fablabbcn/smartcitizen-enclosures/docs/Power Options/Power hub/README.md

# SmartCitizen Power Hub

A simple board to distribute 5V and (maybe in the future) control power outputs in Smart Citizen hardware setups.
