fablabbcn/smartcitizen-enclosures/docs/Power Options/Reset button/README.md

# SmartCitizen Reset

A tiny little board to mount a SWD connector that can be connected to the one in the data board and reset the kit. Serves the same function as the onboard reset button but with easier access.

This board normally can be done in a Fablab very easily.
