fablabbcn/smartcitizen-enclosures/SmartCitizen Water Enclosures/SmartCitizen Water Station/Tentacle Water Station/README.md

# Water Station

Water Station - Patí Científic

## Features

- Up to 6 Water metrics with BNC Connector compatibility
- GPS Location and outdoor antenna
- USB powered

## Enclosure

We used this enclosure with a translucid smoked cover from FIBOX:
https://www.fibox.com/catalog/62/product/176/6016915_ENG3.html

### Supports

All files for laser cutting and 3D printing can be found in [this folder](https://github.com/fablabbcn/smartcitizen-enclosures/tree/master/Smart%20Citizen%20Water%20Station/components).

### Cable glands

We used Icotek QVT16 and QVT20 with different cable grommets (no hole, 1 hole, 4 holes) for passing cables.

### BOM

Find all the components in the [BOM](BOM.csv)

### Docs 

More documentation can be found in [the docs](http://docs.smartcitizen.me/Components/Soil%20and%20water/)

## Contributors

Developed in collaboration with [ICM-CSIC](https://www.icm.csic.es/en) and the [Club Pati Vela de Barcelona](https://pativelabarcelona.com/). Thanks!
