fablabbcn/smartcitizen-enclosures/docs/Water/Electronics/SmartCitizen Water Station/README.md

# Smart Citizen Water Station

This folder contains two iterations of the Smart Citizen Water Station. Currently, we only use the [Isolated Carrier Design](Isolated Carriers Station/) because it's a much more easier to use, assemble, and fix design, with a much lower power consumption. The [Tentacle T3 Design](deprecated/Tentacle%20Water%20Station/) is left for reference.
