fablabbcn/smartcitizen-enclosures/docs/Air/misc/SCK2.1_BIKE_SADDLEBAG/README.md

# Bike enclosure

This folder contains the parts needed to mount the SCK 2.1 with a PMS5003 and a GPS inside a saddle bag.

## Components

1. [Laser Cut PPE Folding](components/ppe-folding.dxf)
2. [3D printed clip](components/clip.stl) and [frame](components/frame.stl)
3. 3D printed intakes: [Left clip](components/inlet-l-clip.stl) and [left shell](components/inlet-l-shell.stl). Same for the [right clip](components/inlet-r-clip.stl) and [shell](components/inlet-r-shell.stl)
4. [3D printed exhaust grid](components/exhaust-grid.stl) and [rim](components/exhaust-rim.stl)
5. [3D printed sensor support](components/support.stl)
6. [3D printed GPS bridge](components/gps-bridge.stl)
6. 2x M3x15mm screw and nut
7. Vaude Race Light L (or similar)

The sensors are placed inside a commercial saddle bag, held with a ppe folding:

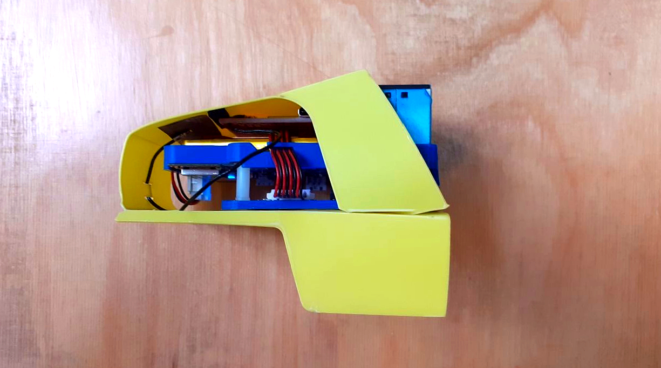
[picture p2: docs/assets/images/bike-saddle/ppe.jpg]


Below more information about how to assemble:

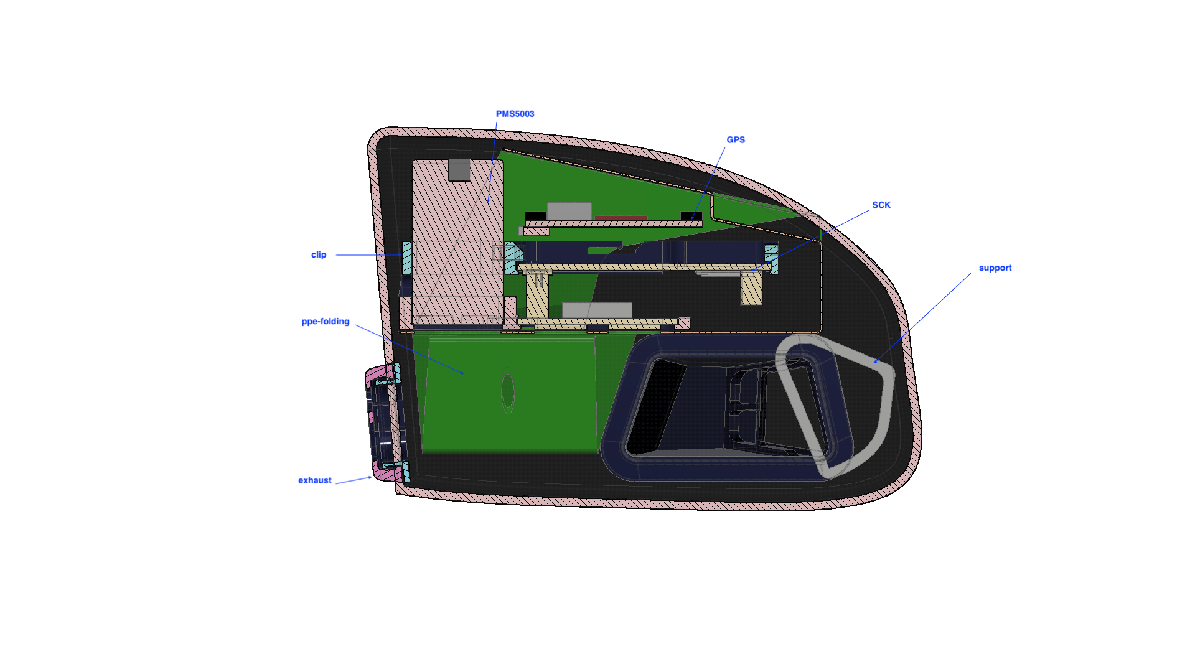
[picture p3: docs/assets/images/bike-saddle/cut-view.png]


## More information

Please, visit the [user manual](https://docs.smartcitizen.me/Use%20cases/Almabike/User%20Manual/) and the [test results](https://docs.smartcitizen.me/Use%20cases/Almabike/Test%20Results/) for more information.
