fablabbcn/smartcitizen-enclosures/docs/Air/SCK2.1/SCK2.1_PMS5003/README.md

Note:

The SCK and the PMS5003 are held together by a 3D printed clip. This can be found in the common components of the HDPE enclosure [here](/Air/SCK2.1/SCK2.1_PMS5003/CNC HDPE circle/components/CLIP_NO_ORING.stl)
