fablabbcn/smartcitizen-enclosures/docs/Air/SCK2.1/SCK2.1_PMS5003_2EC_CO2/README.md

These enclosures are used for the SCK2.1 + PMS5003 with 2xA-series alphasense sensors with one 2-way AFE and a Sensision SCD30 CO2 Sensor.
