fablabbcn/smartcitizen-enclosures/docs/Air/SCK2.1/SCK2.1_PMS5003_CO2/README.md

These enclosures are used for the SCK2.1 + PMS5003 with a Sensision SCD30 CO2 Sensor.
