fablabbcn/smartcitizen-enclosures/docs/Air/misc/CONNECTIVITY_UNIT/README.md

Smart Citizen Connectivity Unit
========================



Check the BOM to see the components needed.

## Enclousure 

An [ABS IP65 Wall Box](https://uk.rs-online.com/web/p/wall-boxes/7696125/?sra=pstk) is used for these unit. For mounting the components  you will need to drill the metal base of the IP65 Wall Box. Use the [*.dxf*](/SmartCitizen Connectivity Unit/base-template.dxf) file as a template using a 5mm drill and a 6mm drill. 


To hold the router, use two 3D printed tubes that you can found [here](/SmartCitizen Connectivity Unit/tube.stl).

 



They are also needed 2 holes on the top side of the box for the router antennas, using a 6.5mm drill, and 1 hole in the bottom part for the AC wire, using a 20mm drill.
