fablabbcn/smartcitizen-enclosures/docs/Air/SCK2.1/SCK2.1_2PMS5003_6EC/6-electrochemical-spec-2pm/README.md

# Station Rev 3.0 6-EC-2PM

This are the hardware design files for a Station Rev3.0 with 6 electrochemical sensors (SPEC) and 2PMS5003.

Components are in the [components](components) folder:

- [3DPRINTING](compontents/3DPRINTING) for parts to be 3D printed to hold components in
- [LASERCUT](compontents/LASERCUT) laser cut acrylic components
