fablabbcn/smartcitizen-enclosures/docs/Air/SCK2.1/SCK2.1_2PMS5003_4EC/4-electrochemical-alphasense-2pm/README.md

# Station Rev 3.0 4-EC-2PM

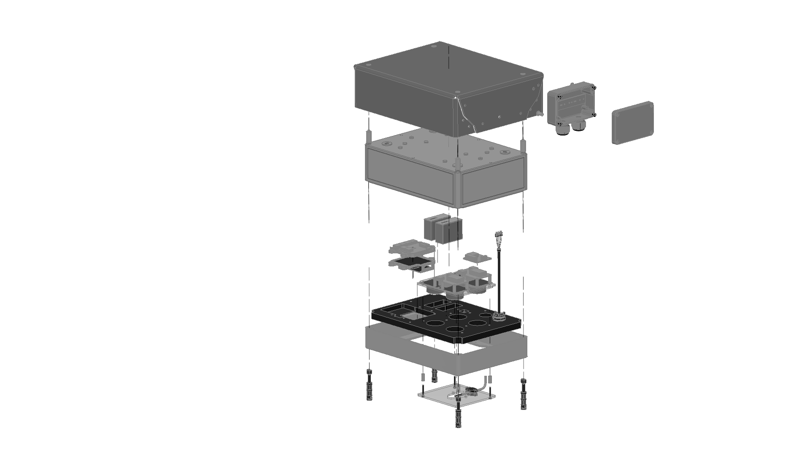
[picture p14: docs/Air/SCK2.1/SCK2.1_2PMS5003_4EC/4-electrochemical-alphasense-2pm/smartcitizen-station-passive-4-sensors.png]


This are the hardware design files for a Station Rev3.0 with 4 electrochemical sensors and 2PMS5003.

Components are in the [components](components) folder:

- [3DPRINTING](compontents/3DPRINTING) for parts to be 3D printed to hold components in
- [AUXLIARIES](compontents/AUXLIARIES) for elements such as the reset button
- [LASERCUT](compontents/LASERCUT) laser cut acrylic components
