fablabbcn/smartcitizen-enclosures/docs/Air/SCK2.1/SCK2.1_PMS5003/UMBRELLA/README.md

# Umbrella Cover

These are small and medium sized covers for the sensors. Made out of Dibond, with an stainless steel plate and some spacers.

Extras:

- M3 /M4 rivet nuts for hanging the enclosure using the spacers
- M4 rivet nuts for hanging the power supply on one side
