fablabbcn/smartcitizen-enclosures/docs/Air/SCK2.1/SCK2.1_2PMS5003_3EC/SmartCitizen Station V2.0/SmartCitizen Station V2.0 - 2.jpg

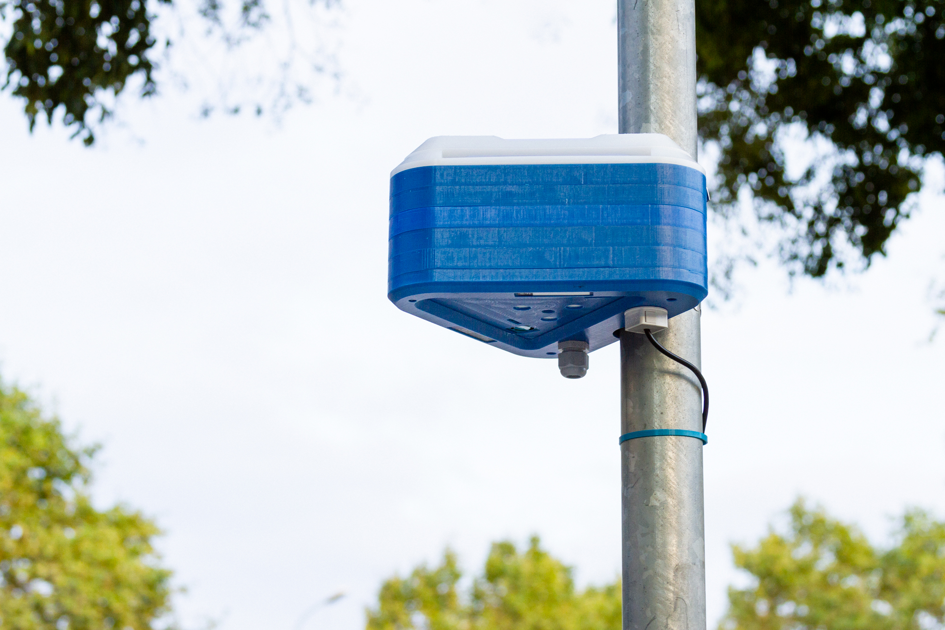
docs/Air/SCK2.1/SCK2.1_2PMS5003_3EC/SmartCitizen Station V2.0/SmartCitizen Station V2.0 - 2.jpg
