fablabbcn/smartcitizen-enclosures/docs/Air/SCK2.1/SCK2.1_PMS5003/CNC HDPE circle/final_render.png

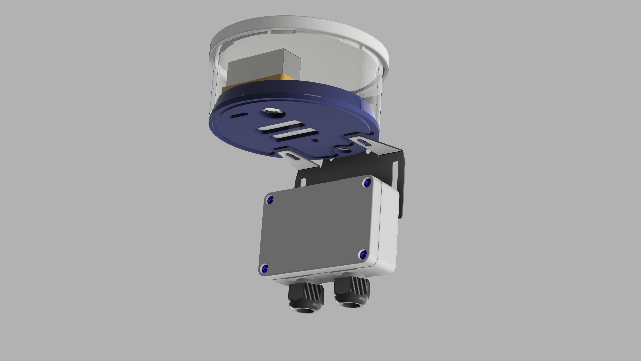
docs/Air/SCK2.1/SCK2.1_PMS5003/CNC HDPE circle/final_render.png
