fablabbcn/smartcitizen-enclosures/docs/assets/images/2.1/SCKit_21.png

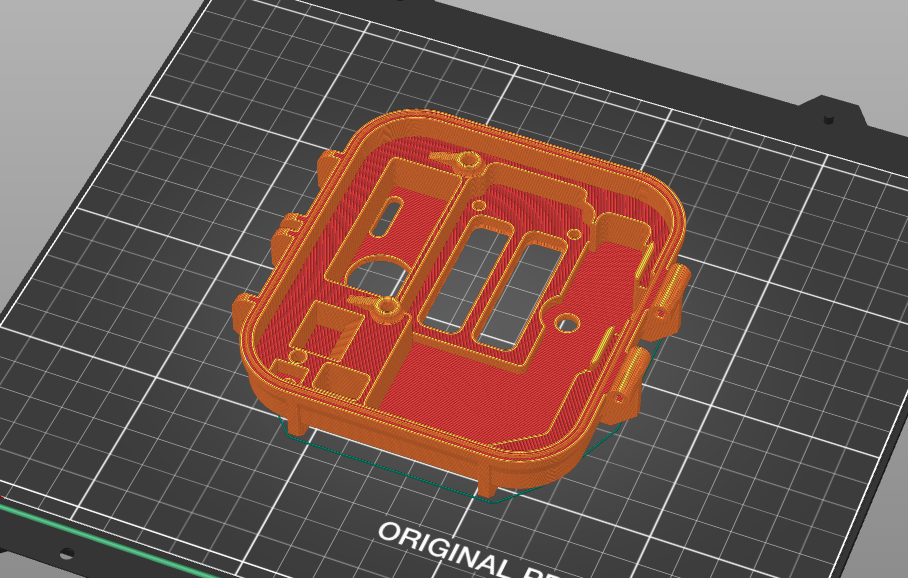
docs/assets/images/2.1/SCKit_21.png
