fablabbcn/smartcitizen-enclosures/docs/assets/images/2.2/PID_TIG_HCHO.jpg

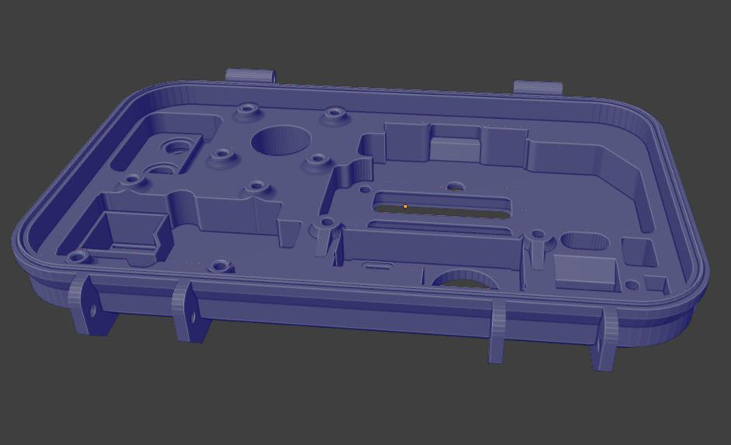
docs/assets/images/2.2/PID_TIG_HCHO.jpg
