fablabbcn/smartcitizen-enclosures/docs/assets/images/2.2/SCKit_22.png

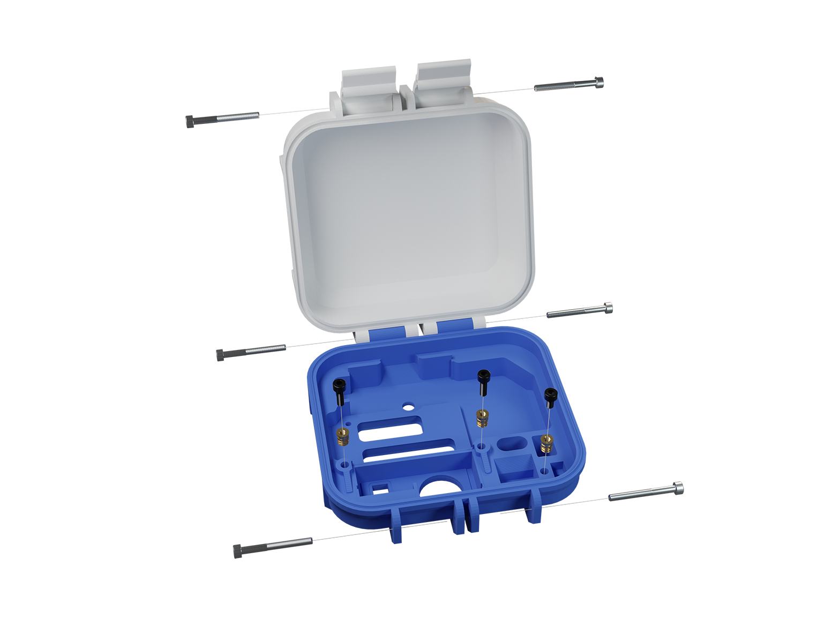
docs/assets/images/2.2/SCKit_22.png
