fablabbcn/smartcitizen-enclosures/docs/assets/images/2.2/SCKit_22_2EC.png

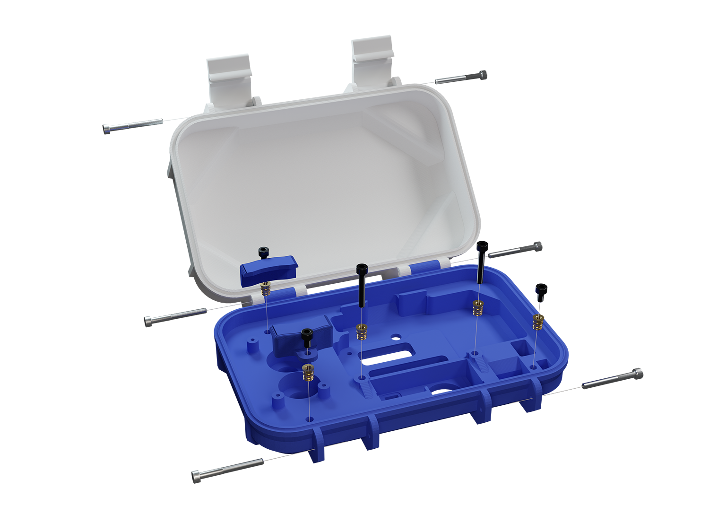
docs/assets/images/2.2/SCKit_22_2EC.png
