fablabbcn/smartcitizen-enclosures/docs/assets/images/2.2/SCKit_22_CO2+2EC.png

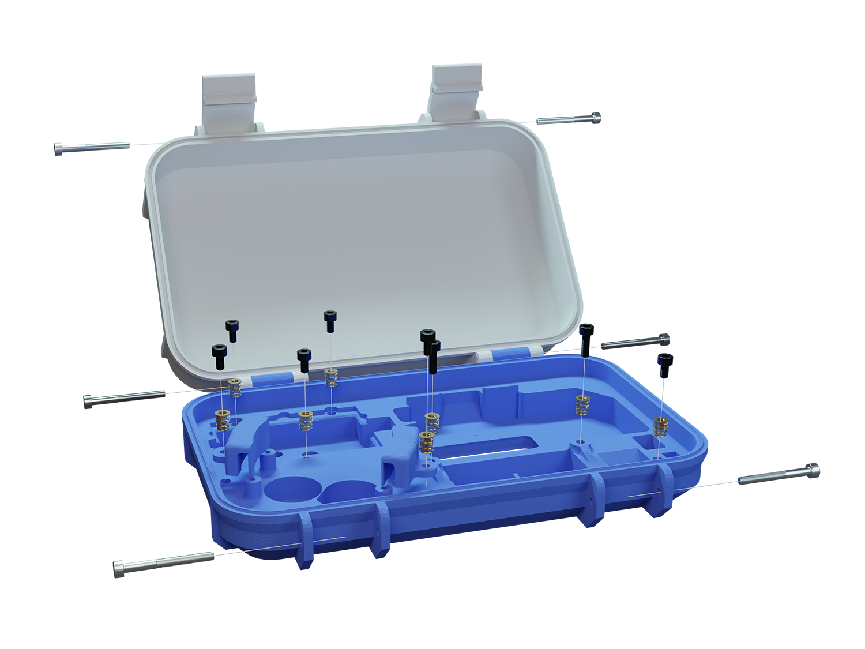
docs/assets/images/2.2/SCKit_22_CO2+2EC.png
