fablabbcn/smartcitizen-enclosures/docs/assets/images/2.2/SCKit_22_CO2+HCHO.png

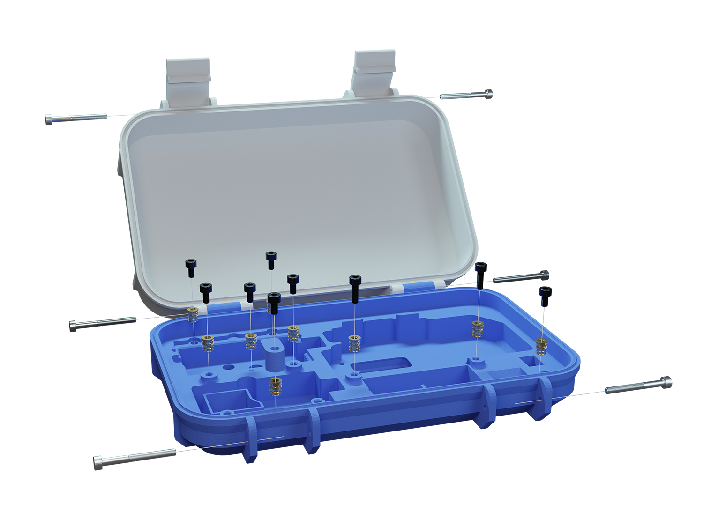
docs/assets/images/2.2/SCKit_22_CO2+HCHO.png
