fablabbcn/smartcitizen-enclosures/docs/assets/images/2.2/SCKit_EC_B-Series.jpg

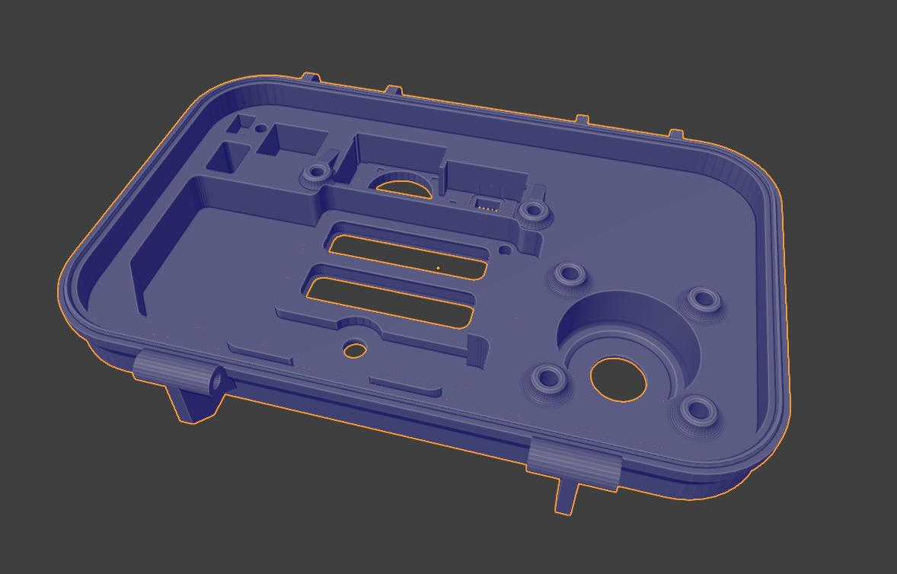
docs/assets/images/2.2/SCKit_EC_B-Series.jpg
