fablabbcn/smartcitizen-enclosures/docs/assets/images/2.3/Unfold.png

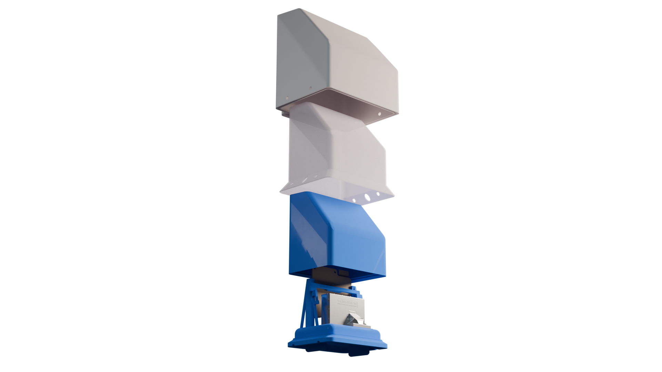
docs/assets/images/2.3/Unfold.png
