fablabbcn/smartcitizen-enclosures/docs/assets/images/power/schematic.png

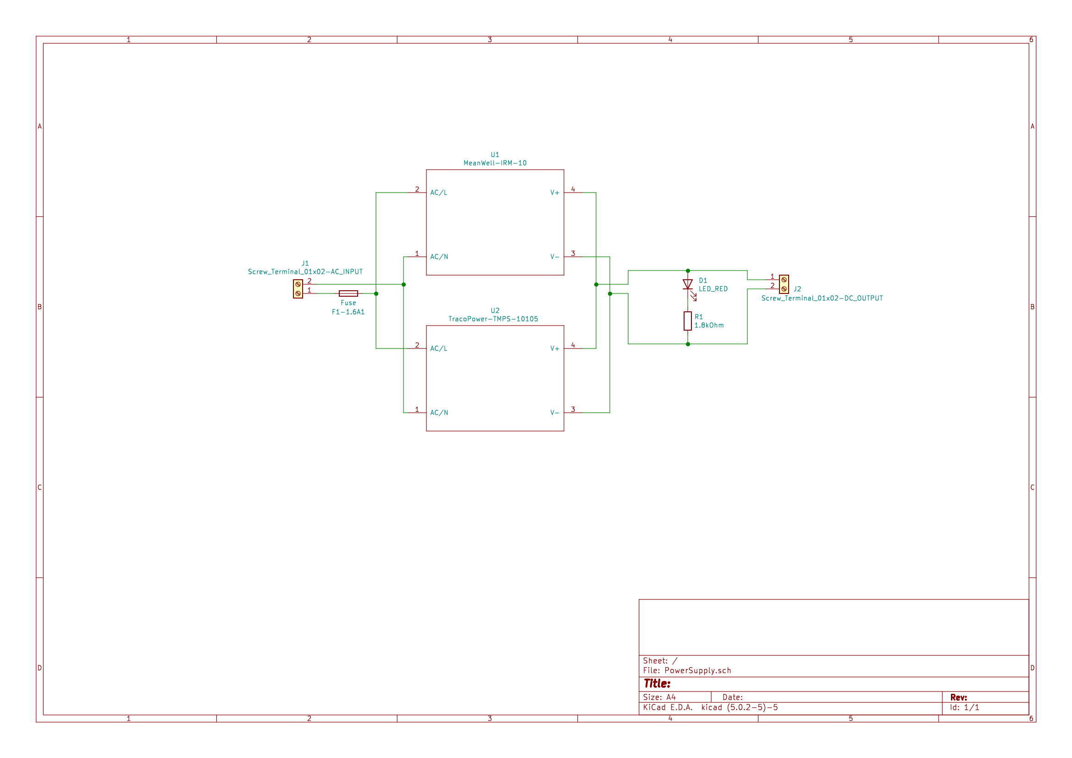
docs/assets/images/power/schematic.png
