fablabbcn/smartcitizen-enclosures/docs/assets/images/SCK2.1.jpg

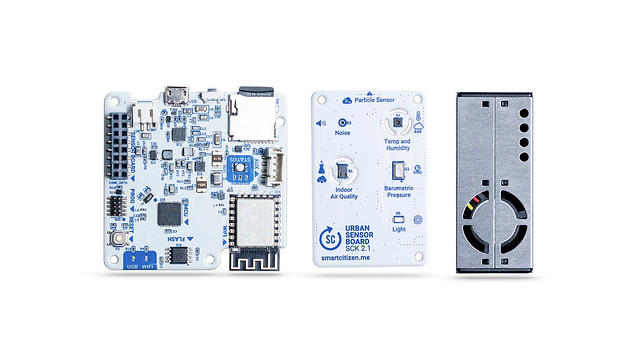
docs/assets/images/SCK2.1.jpg
