fablabbcn/smartcitizen-enclosures/docs/assets/images/SCK2.2.jpg

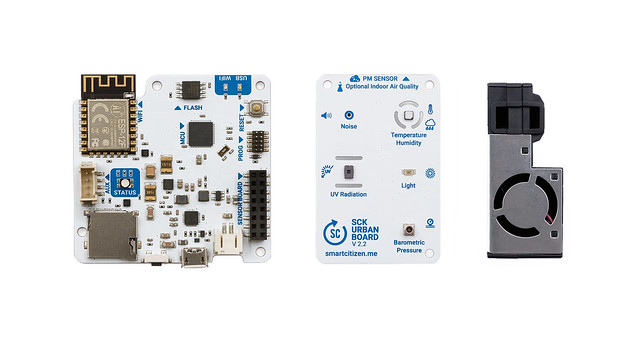
docs/assets/images/SCK2.2.jpg
