fablabbcn/smartcitizen-enclosures/docs/assets/images/water/cable_protection.png

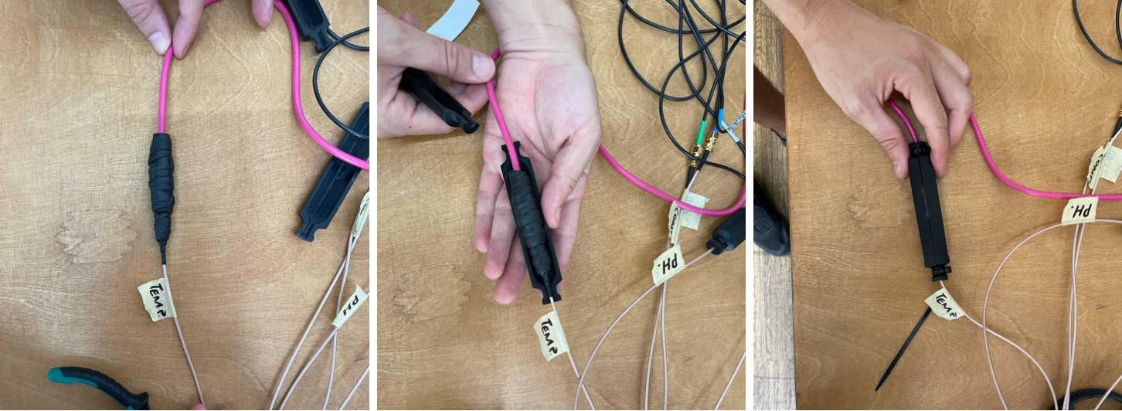
docs/assets/images/water/cable_protection.png
