fablabbcn/smartcitizen-enclosures/docs/assets/images/water/multiple_probe.png

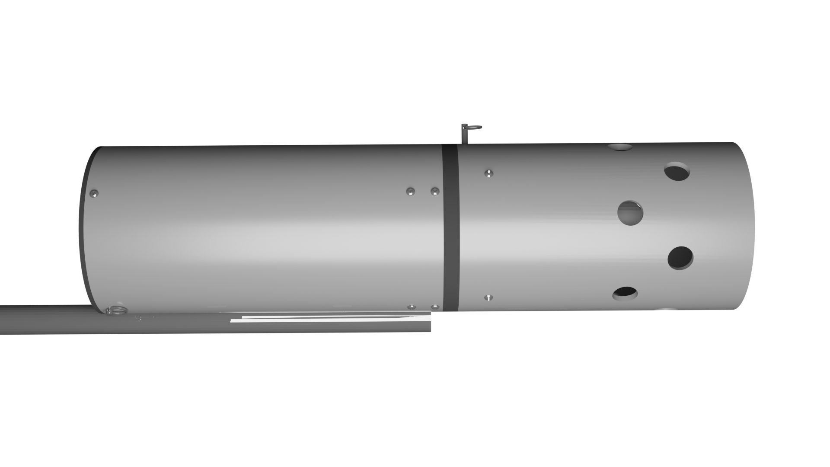
docs/assets/images/water/multiple_probe.png
