fablabbcn/smartcitizen-enclosures/docs/assets/images/water/render.png

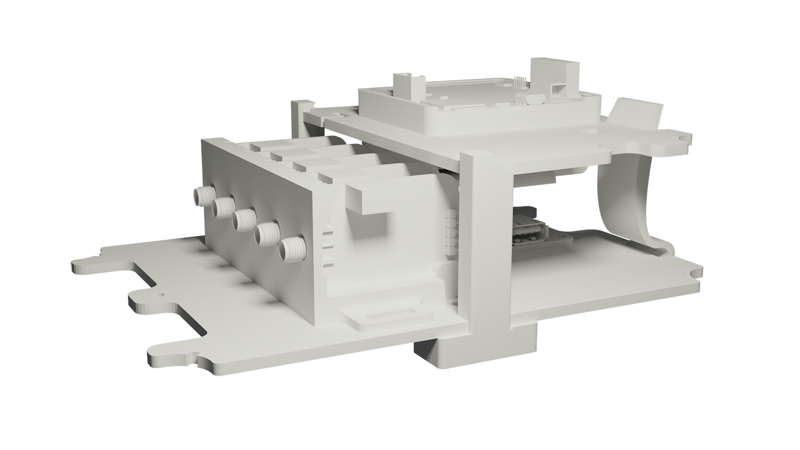
docs/assets/images/water/render.png
