fablabbcn/smartcitizen-enclosures/docs/assets/images/water/steel_tie.png

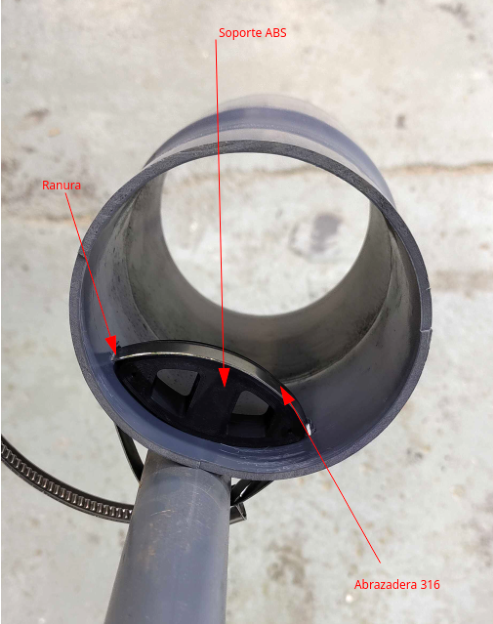
docs/assets/images/water/steel_tie.png
