fablabbcn/smartcitizen-enclosures/docs/assets/images/water/water-station-pipe_detail.png

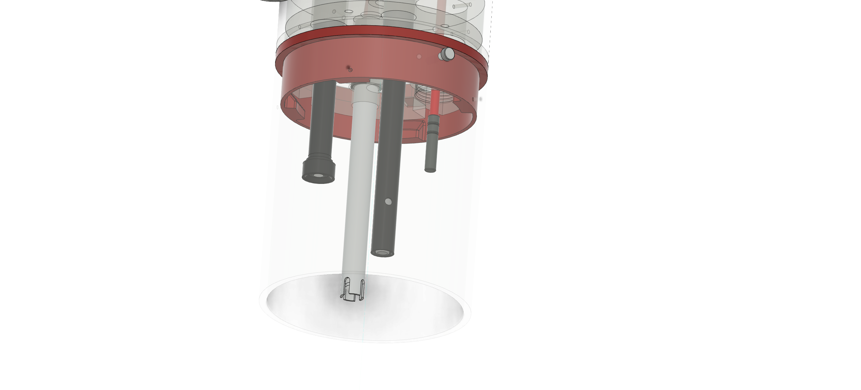
docs/assets/images/water/water-station-pipe_detail.png
