fablabbcn/smartcitizen-enclosures/docs/Power Options/Reset button/sc_reset/exports-fab/sc_reset_small-Drills.png

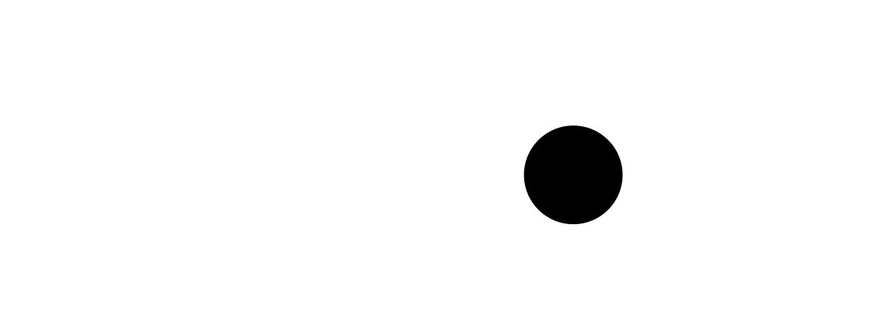
docs/Power Options/Reset button/sc_reset/exports-fab/sc_reset_small-Drills.png
