fablabbcn/smartcitizen-enclosures/docs/Power Options/Reset button/sc_reset/exports-fab/sc_reset_small-F_Cu.png

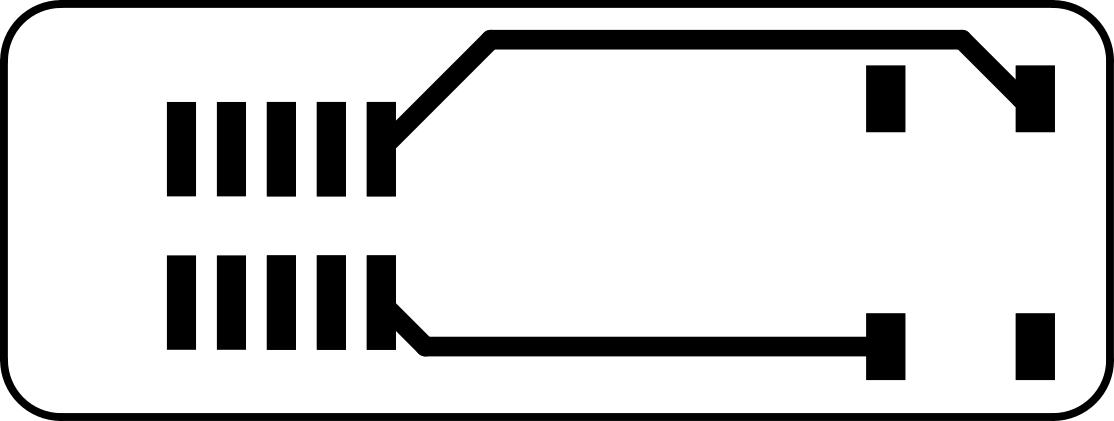
docs/Power Options/Reset button/sc_reset/exports-fab/sc_reset_small-F_Cu.png
