fablabbcn/smartcitizen-enclosures/docs/Power Options/Solar/CUT.png

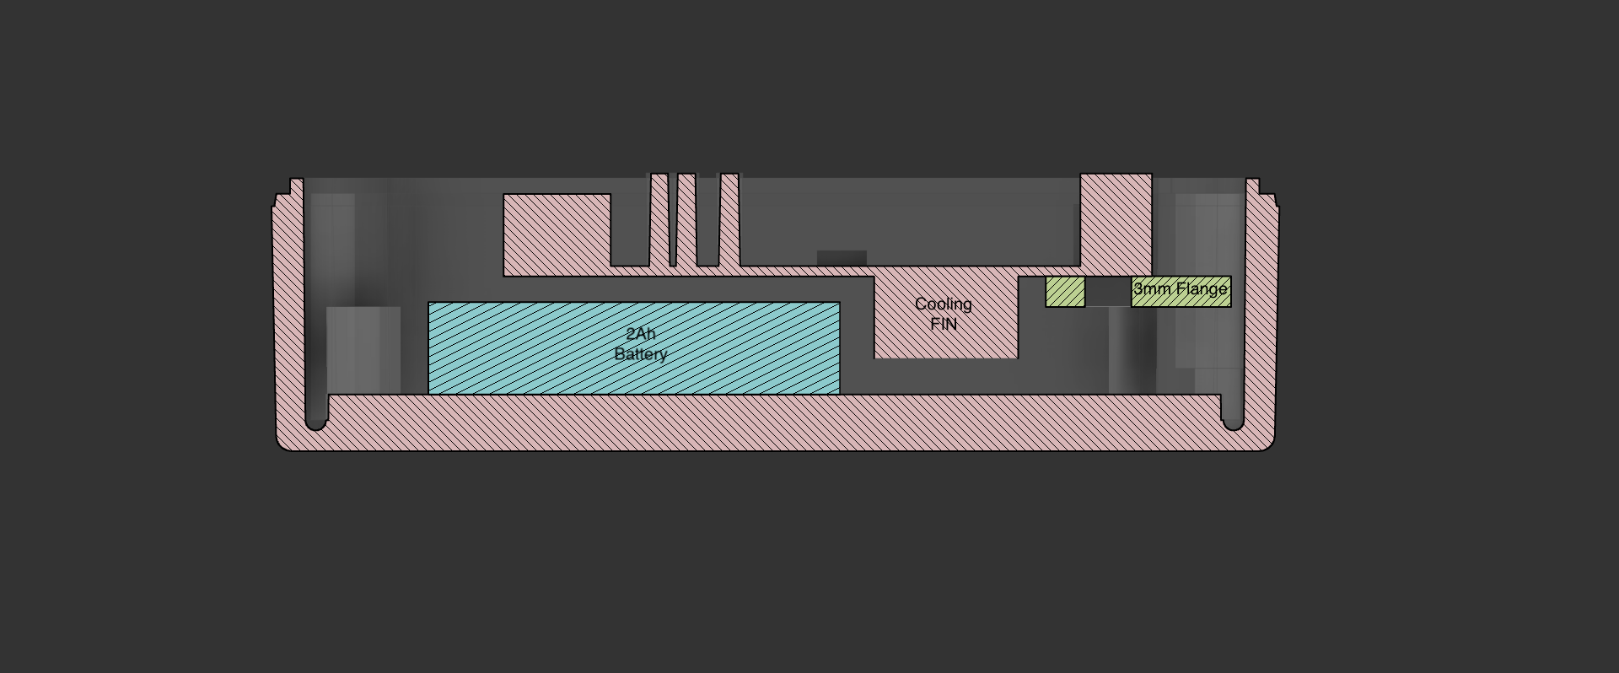
docs/Power Options/Solar/CUT.png
