fablabbcn/smartcitizen-enclosures/docs/Air/SCK2.1/SCK2.1_PMS5003/3D Printed Modular Viadukaduk/components/README.md

These are the components.

SCK 2.1 viadukaduk enclosure 1.0.skp is a file with all the componnents put together. Use this to make coordinated changes.

Other files are single component files.

U can use the stl's to make / order prints directly.

In reality the enclosures printed in PETG required some patience and a bit of corrections with a stanley knife.
