fablabbcn/smartcitizen-enclosures/docs/assets/images/power/DFR0559 (V1.1) Top Component Location.png

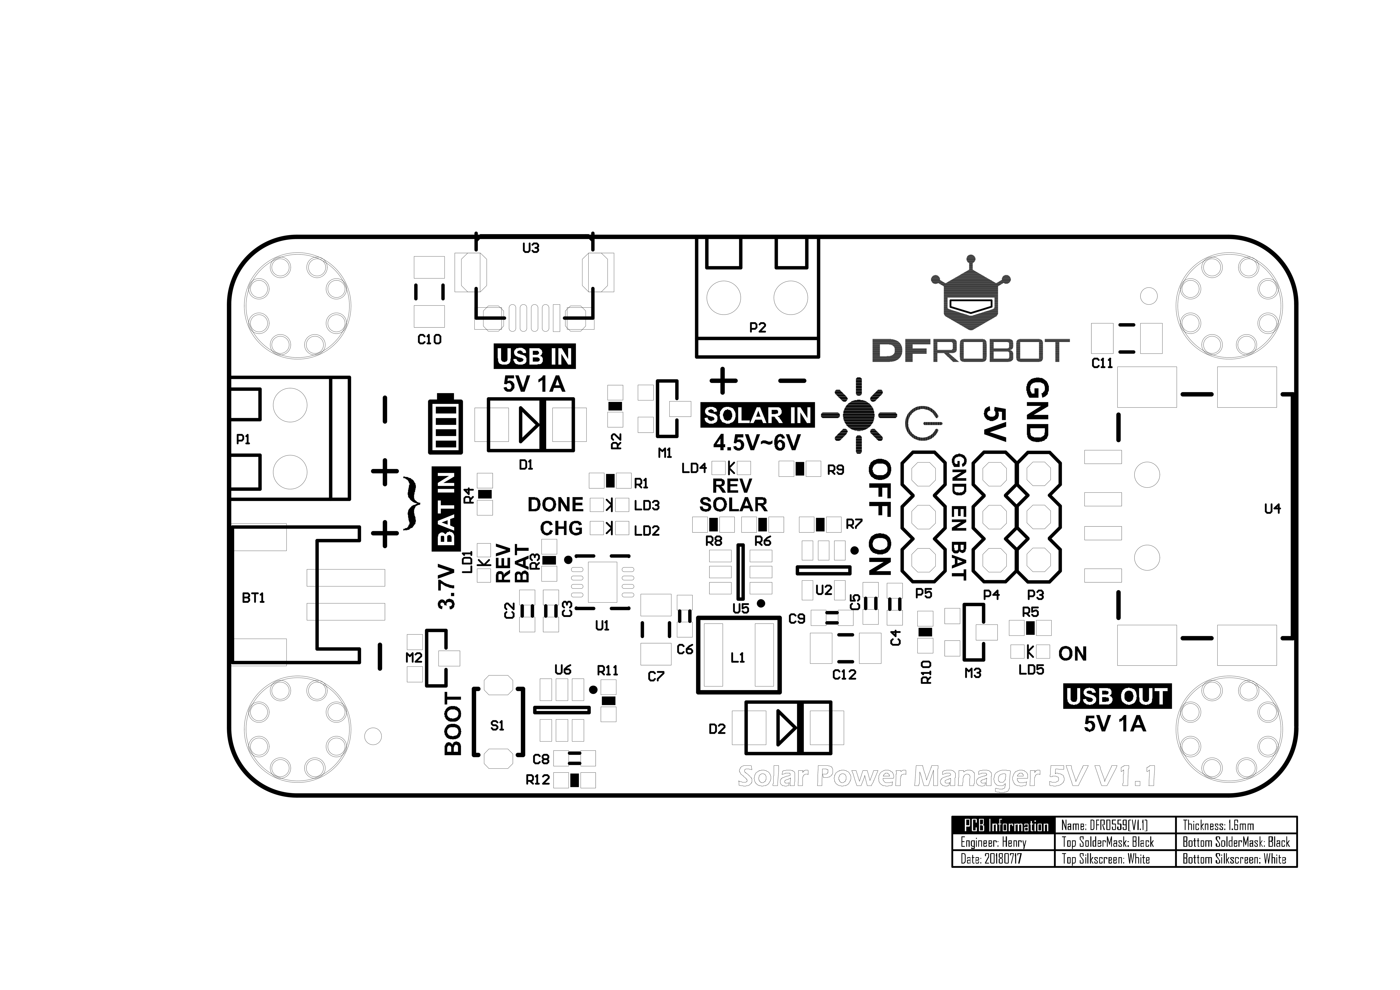
docs/assets/images/power/DFR0559 (V1.1) Top Component Location.png
