fablabbcn/smartcitizen-enclosures/docs/Air/SCK2.1/SCK2.1_PMS5003/3D Printed square/UMBRELLA/cover.dxf

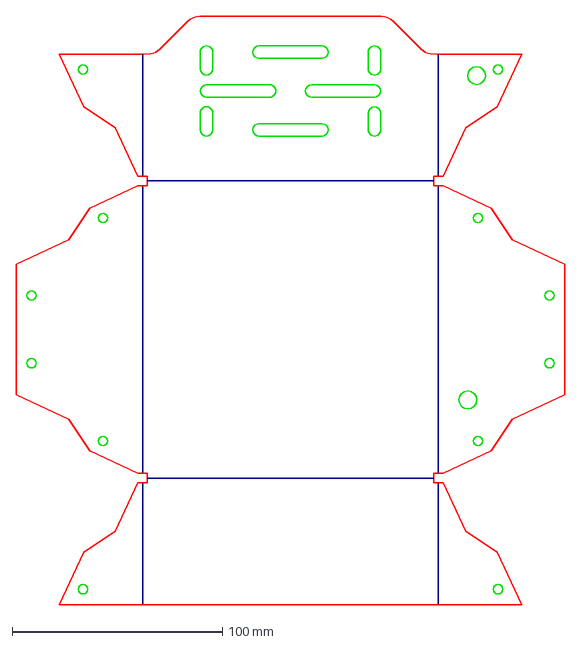
[picture p60: CAD file, 2024-11-13]
docs/Air/SCK2.1/SCK2.1_PMS5003/3D Printed square/UMBRELLA/cover.dxf
261.2 x 280.0 mm
