fablabbcn/smartcitizen-enclosures/docs/Air/SCK2.1/SCK2.1_PMS5003/CNC HDPE circle/components/CAP_MIRROR.stl

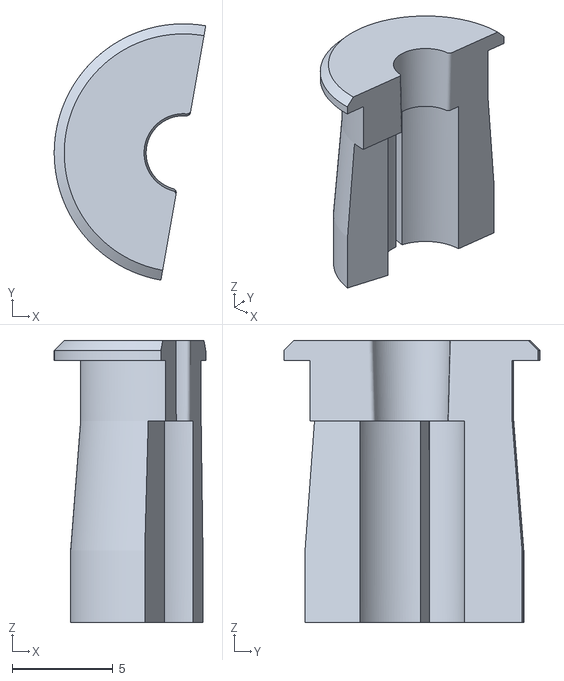
[picture p61: CAD file, 2022-10-10]
docs/Air/SCK2.1/SCK2.1_PMS5003/CNC HDPE circle/components/CAP_MIRROR.stl
7.52 x 12.7 x 14.0
