fablabbcn/smartcitizen-enclosures/docs/Air/SCK2.1/SCK2.1_PMS5003/CNC HDPE square/components/base.stl

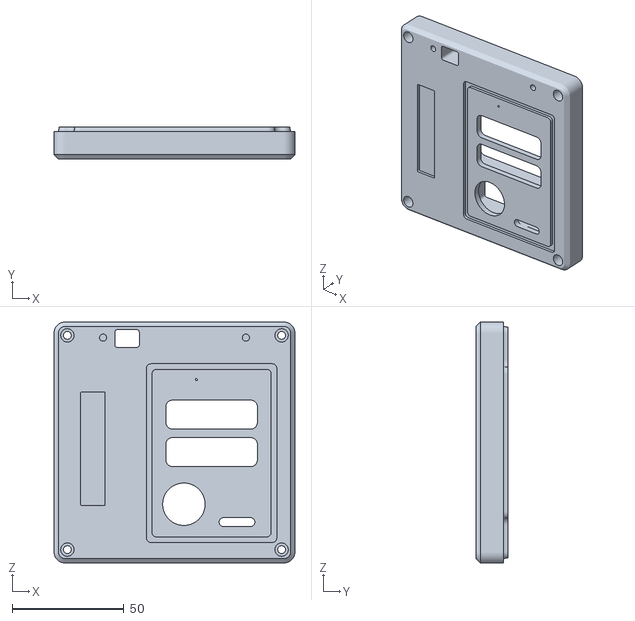
[picture p62: CAD file, 2021-04-20]
docs/Air/SCK2.1/SCK2.1_PMS5003/CNC HDPE square/components/base.stl
108.0 x 14.5 x 108.0
