fablabbcn/smartcitizen-enclosures/docs/Air/SCK2.1/SCK2.1_PMS5003/SCK_3Dprint_Assembly_GER_EN_USTTG_IIGS_2023/sck_17-sensor-rahmen.stl

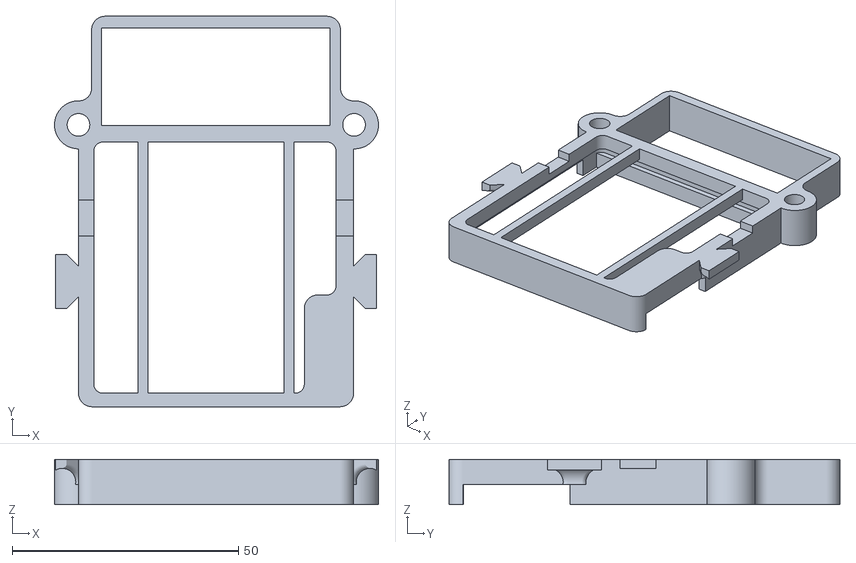
[picture p63: CAD file, 2024-04-08]
docs/Air/SCK2.1/SCK2.1_PMS5003/SCK_3Dprint_Assembly_GER_EN_USTTG_IIGS_2023/sck_17-sensor-rahmen.stl
71.6 x 86.3 x 10.0
