fablabbcn/smartcitizen-enclosures/docs/Air/SCK2.1/SCK2.1_PMS5003/UMBRELLA/components/#cover.dxf

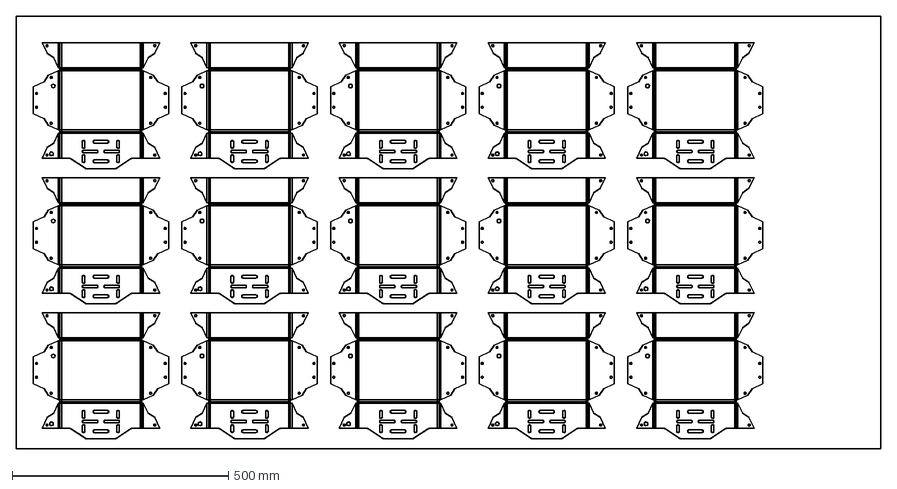
[picture p64: CAD file, 2024-04-19]
docs/Air/SCK2.1/SCK2.1_PMS5003/UMBRELLA/components/#cover.dxf
2000.0 x 1000.0 mm
