fablabbcn/smartcitizen-enclosures/docs/Air/SCK2.1/SCK2.1_PMS5003_1EC_B/3D Printed Square/components/base.step

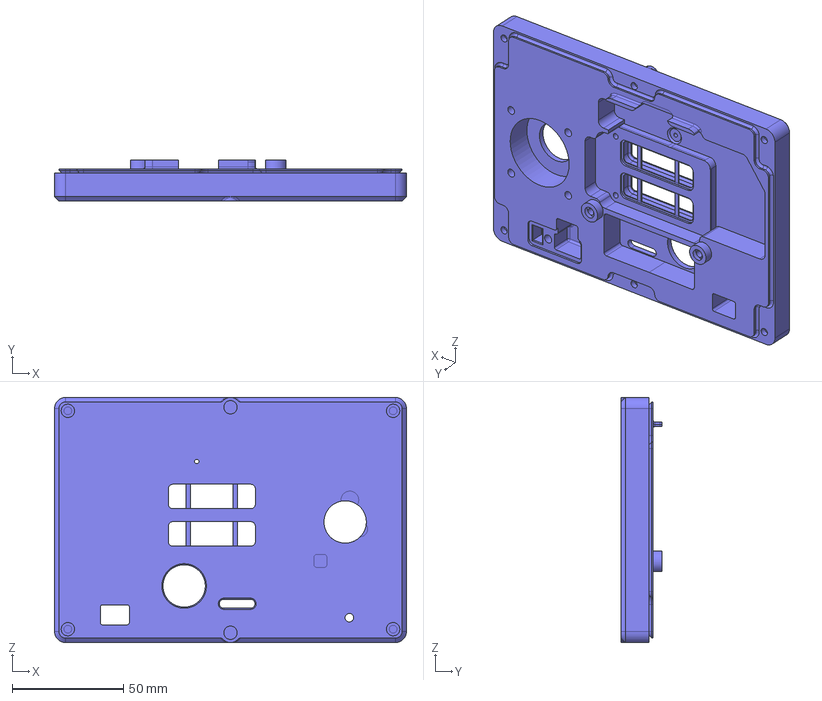
[picture p65: CAD file, 2023-01-04]
docs/Air/SCK2.1/SCK2.1_PMS5003_1EC_B/3D Printed Square/components/base.step
158.0 x 18.5 x 110.0 mm
