fablabbcn/smartcitizen-enclosures/docs/Air/SCK2.1/SCK2.1_PMS5003_2EC/3D Printed frog box/components/base.stl

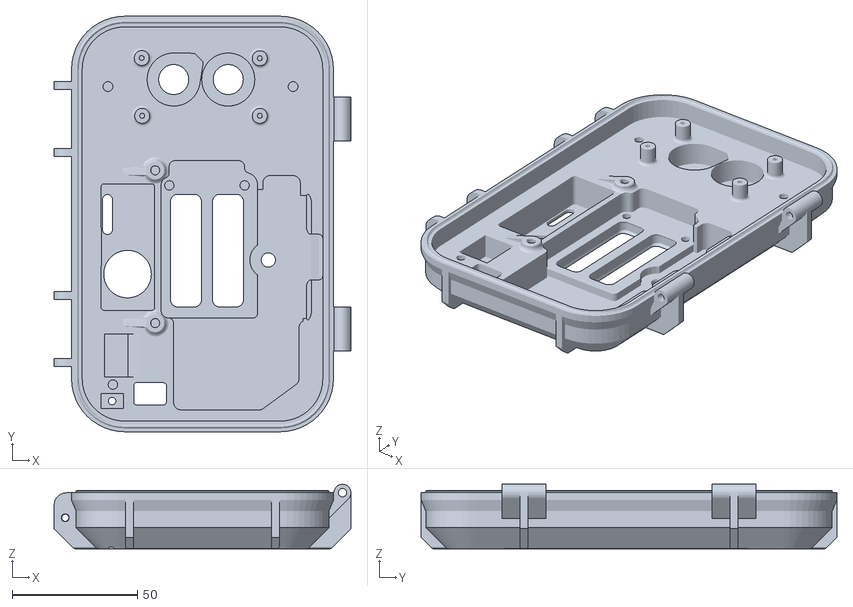
[picture p66: CAD file, 2024-09-17]
docs/Air/SCK2.1/SCK2.1_PMS5003_2EC/3D Printed frog box/components/base.stl
118.7 x 166.0 x 25.8
