fablabbcn/smartcitizen-enclosures/docs/Air/SCK2.1/SCK2.1_PMS5003_2EC/3D Printed/components/clip-3d-2000mAh_for_bridge.stl

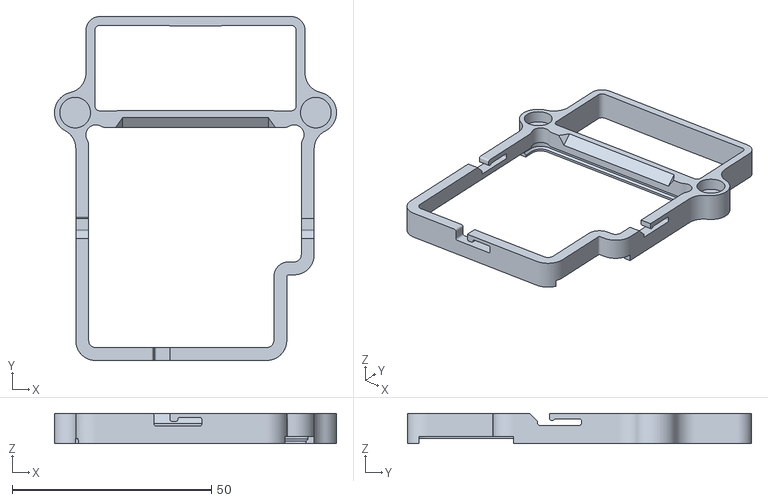
[picture p67: CAD file, 2022-10-26]
docs/Air/SCK2.1/SCK2.1_PMS5003_2EC/3D Printed/components/clip-3d-2000mAh_for_bridge.stl
70.8 x 86.3 x 7.60
