fablabbcn/smartcitizen-enclosures/docs/Air/SCK2.1/SCK2.1_PMS5003_2EC_CO2/(WIP) IP Box/clip_scd30.stl

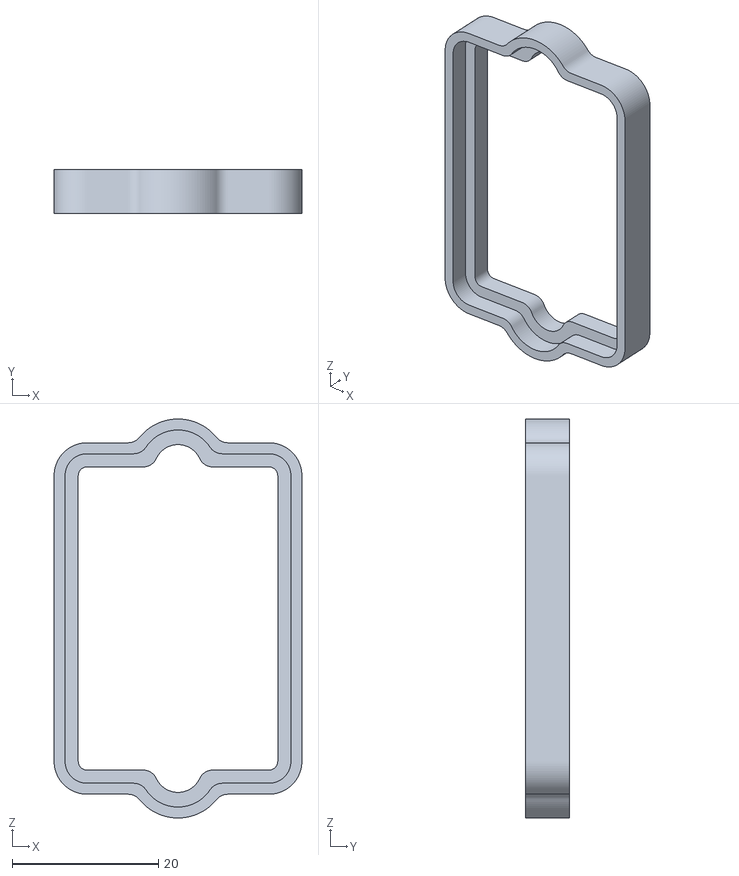
[picture p68: CAD file, 2023-01-04]
docs/Air/SCK2.1/SCK2.1_PMS5003_2EC_CO2/(WIP) IP Box/clip_scd30.stl
33.9 x 6.00 x 54.5
