fablabbcn/smartcitizen-enclosures/docs/Air/SCK2.1/SCK2.1_PMS5003_2EC_CO2/3D Printed Square/components/base.stl

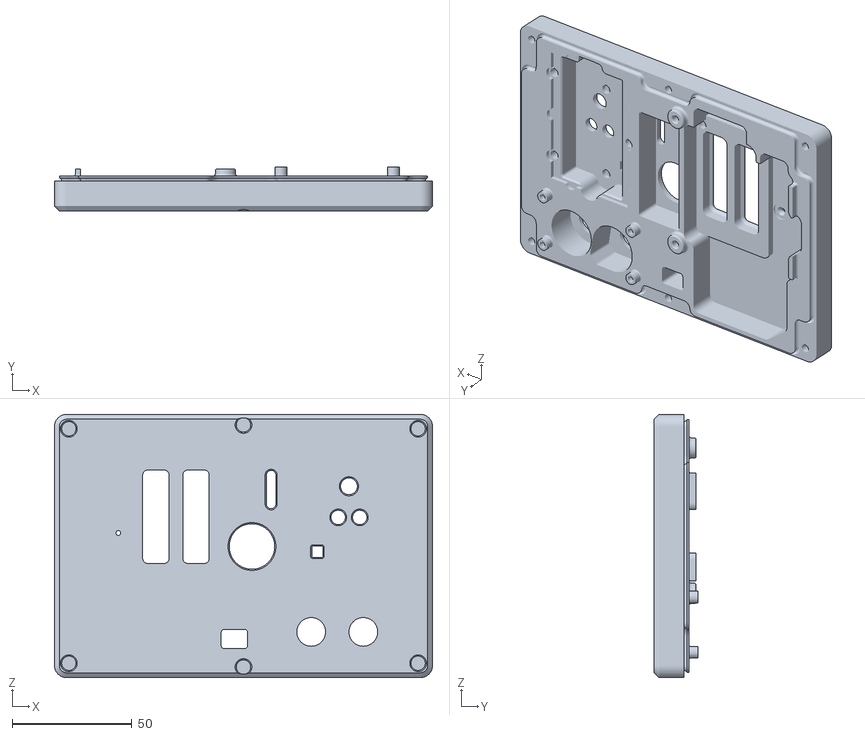
[picture p69: CAD file, 2021-11-16]
docs/Air/SCK2.1/SCK2.1_PMS5003_2EC_CO2/3D Printed Square/components/base.stl
158.0 x 18.3 x 110.0
