fablabbcn/smartcitizen-enclosures/docs/Air/SCK2.1/SCK2.1_PMS5003_CO2/3D Printed Square/components/cover-acrylic.step

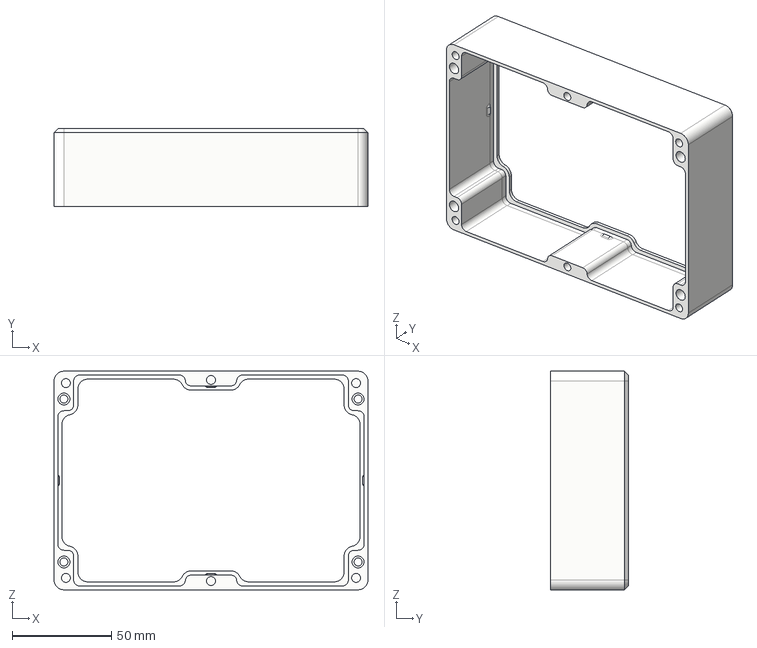
[picture p70: CAD file, 2022-10-26]
docs/Air/SCK2.1/SCK2.1_PMS5003_CO2/3D Printed Square/components/cover-acrylic.step
158.0 x 39.0 x 110.0 mm
