fablabbcn/smartcitizen-enclosures/docs/Air/SCK2.1/SCK2.1_PMS5003_CO2_HCHO/3D Printed frog box/components/base.stl

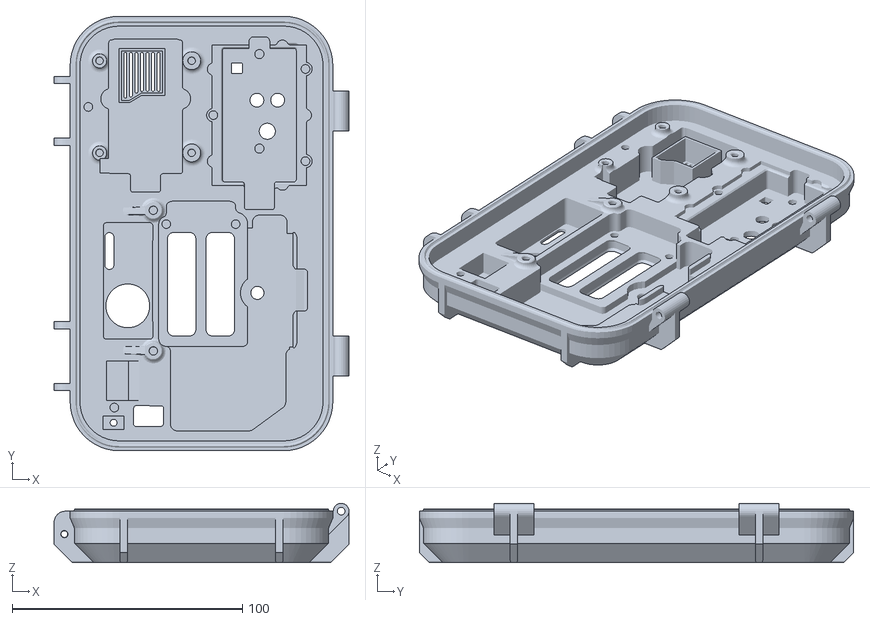
[picture p71: CAD file, 2024-09-17]
docs/Air/SCK2.1/SCK2.1_PMS5003_CO2_HCHO/3D Printed frog box/components/base.stl
128.0 x 188.5 x 25.8
