fablabbcn/smartcitizen-enclosures/docs/Air/SCK2.1/SCK2.1_SPS30/3D Printed Square/components/clip-3d-2000mAh-sps30.stl

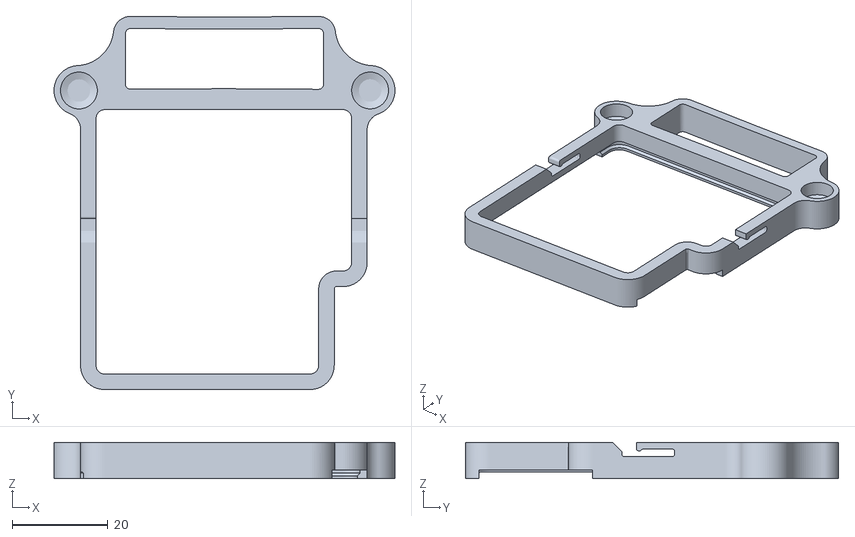
[picture p72: CAD file, 2023-05-24]
docs/Air/SCK2.1/SCK2.1_SPS30/3D Printed Square/components/clip-3d-2000mAh-sps30.stl
71.2 x 77.9 x 7.60
