fablabbcn/smartcitizen-enclosures/docs/Air/SCK2.2/SCK2.2_SEN5X/3D printed outdoor/components/sliderSCK.stl

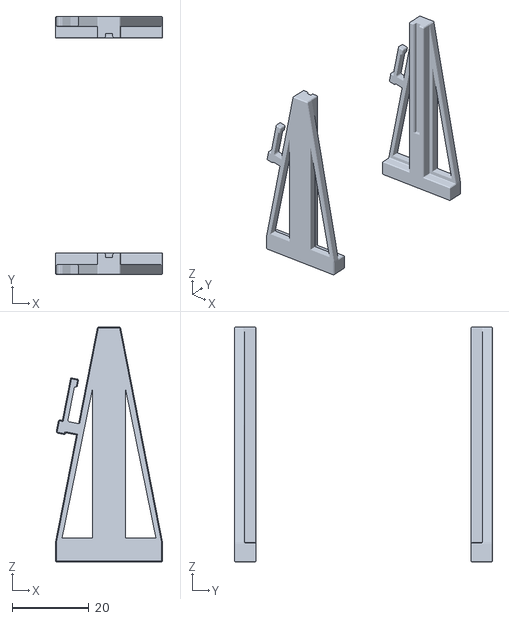
[picture p73: CAD file, 2024-11-13]
docs/Air/SCK2.2/SCK2.2_SEN5X/3D printed outdoor/components/sliderSCK.stl
28.0 x 67.4 x 61.4
