fablabbcn/smartcitizen-enclosures/docs/Air/SCK2.3/SCK2.3_SEN5X + CO2/3D_printed_frog_box/components/base_SCKit.stl

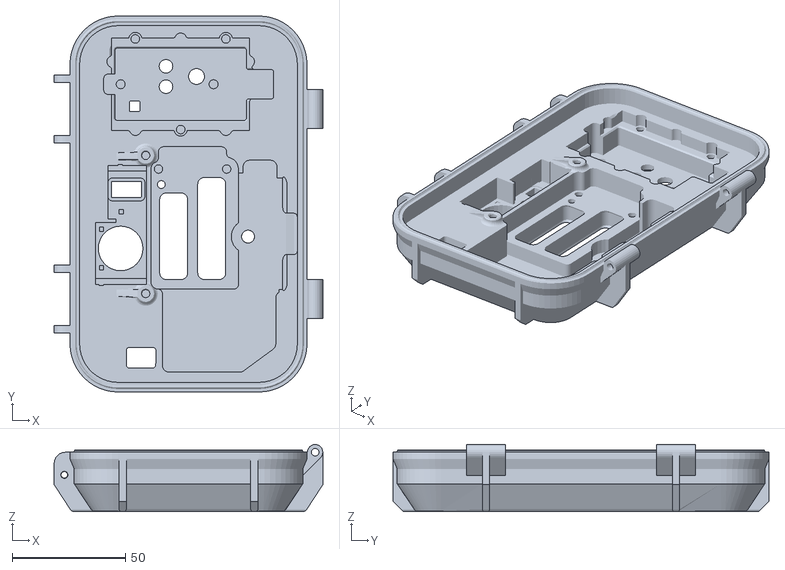
[picture p75: CAD file, 2025-04-24]
docs/Air/SCK2.3/SCK2.3_SEN5X + CO2/3D_printed_frog_box/components/base_SCKit.stl
118.7 x 166.0 x 29.6
