fablabbcn/smartcitizen-enclosures/docs/Air/SCK2.3/SCK2.3_SEN5X/3D_printed_outdoor_sen5x_only/components/innerCover.stl

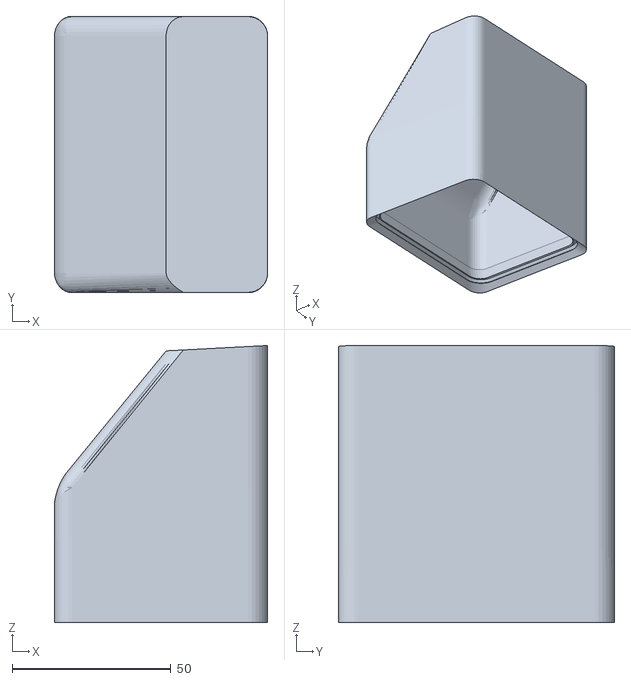
[picture p77: CAD file, 2025-12-11]
docs/Air/SCK2.3/SCK2.3_SEN5X/3D_printed_outdoor_sen5x_only/components/innerCover.stl
67.2 x 87.0 x 87.2
