fablabbcn/smartcitizen-enclosures/docs/Air/shared/clip-sck2.X-sen5X.stl

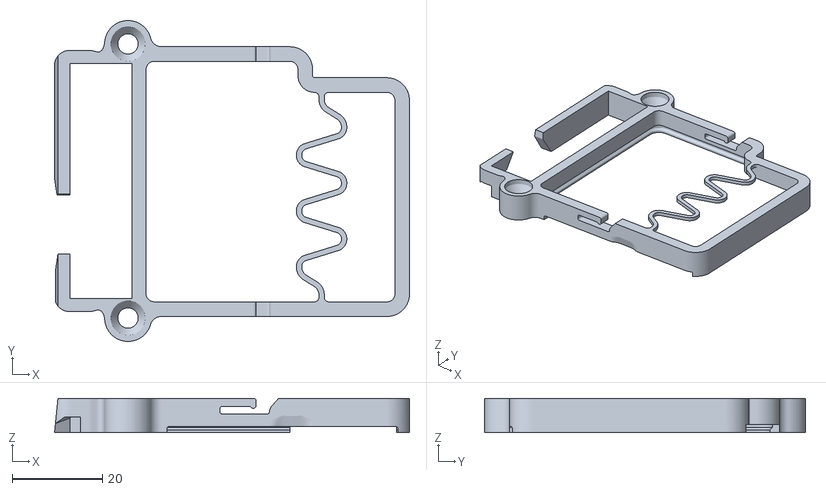
[picture p78: CAD file, 2026-04-29]
docs/Air/shared/clip-sck2.X-sen5X.stl
78.8 x 71.2 x 7.60
