fablabbcn/smartcitizen-enclosures/docs/Air/shared/large/cover_indoor.stl

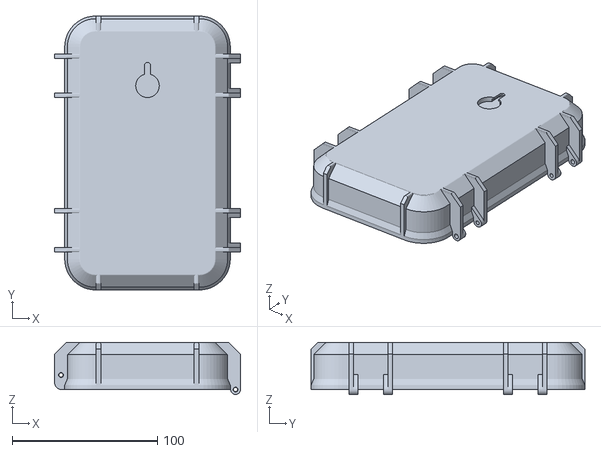
[picture p79: CAD file, 2024-03-20]
docs/Air/shared/large/cover_indoor.stl
128.0 x 188.5 x 35.8
