fablabbcn/smartcitizen-enclosures/docs/Air/shared/medium/cover_outdoor.3mf

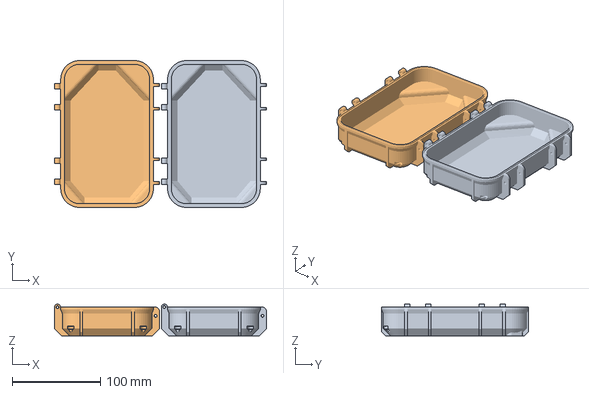
[picture p80: CAD file, 2025-07-16]
docs/Air/shared/medium/cover_outdoor.3mf
239.7 x 166.0 x 36.1 mm
cover_outdoor.stl x 2
