fablabbcn/smartcitizen-enclosures/docs/Air/shared/small/cover_multipurpose.3mf

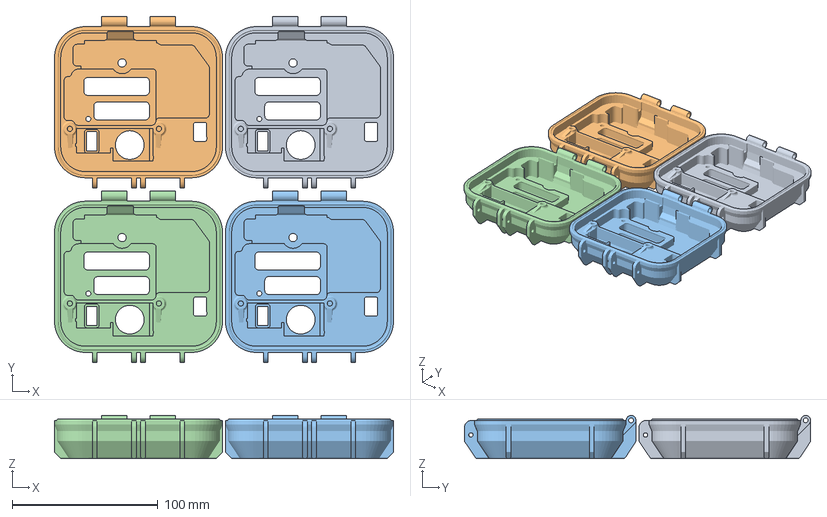
[picture p81: CAD file, 2025-08-28]
docs/Air/shared/small/cover_multipurpose.3mf
232.3 x 237.3 x 29.6 mm
base_SCKit.stl
base_SCKit.stl 1
base_SCKit.stl 2
base_SCKit.stl 3
