fablabbcn/smartcitizen-enclosures/docs/Air/shared/umbrella/components/umbrella-small.dxf

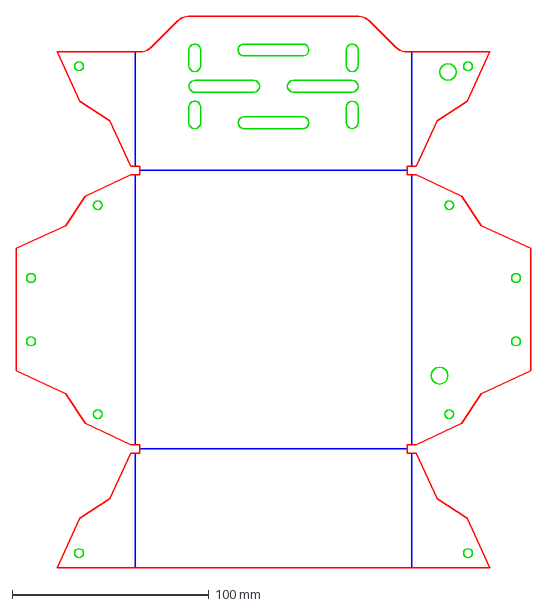
[picture p82: CAD file, 2025-02-17]
docs/Air/shared/umbrella/components/umbrella-small.dxf
261.2 x 280.0 mm
