fablabbcn/smartcitizen-enclosures/docs/Components/ALPHADELTA/AlphaDELTABoard.stp

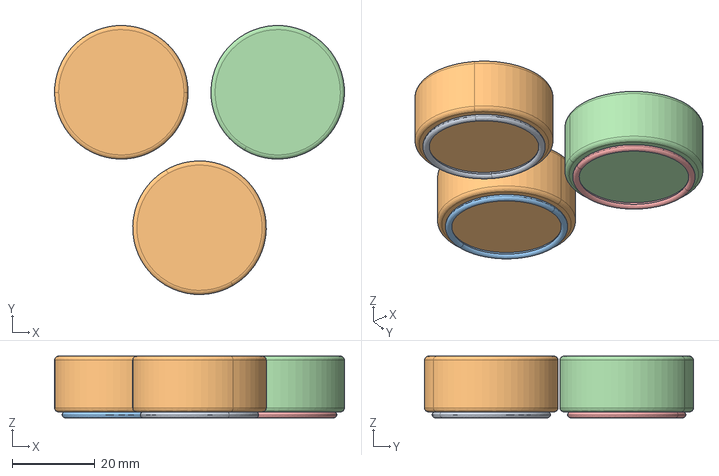
[picture p83: CAD file, 2019-09-09]
docs/Components/ALPHADELTA/AlphaDELTABoard.stp
70.1 x 65.0 x 14.9 mm
