fablabbcn/smartcitizen-enclosures/docs/Components/ALPHASENSE/alphasense-isb v11.step

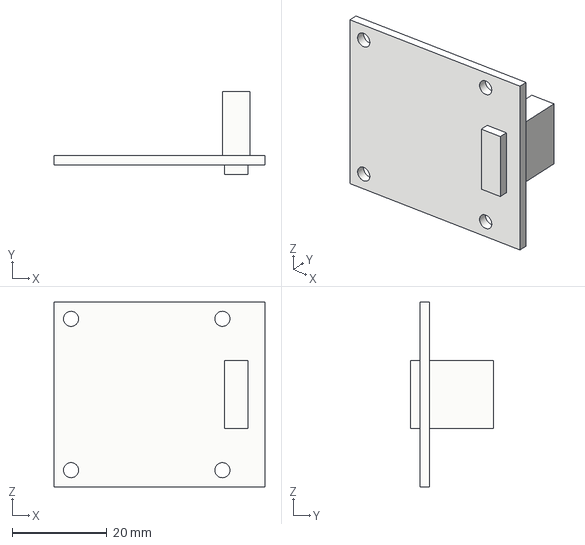
[picture p84: CAD file, 2023-10-24]
docs/Components/ALPHASENSE/alphasense-isb v11.step
44.6 x 17.5 x 39.1 mm
