fablabbcn/smartcitizen-enclosures/docs/Components/MESHTASTIC/Expansion-Board-for-Seeed-Studio-XIAO.stl

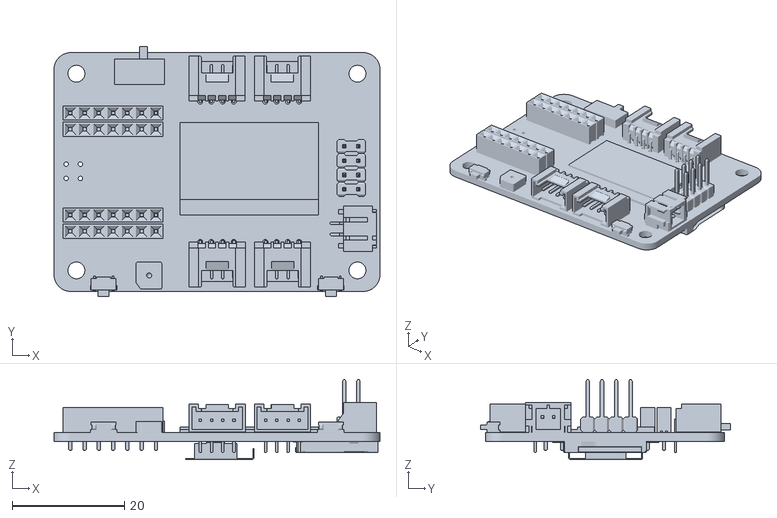
[picture p85: CAD file, 2025-06-26]
docs/Components/MESHTASTIC/Expansion-Board-for-Seeed-Studio-XIAO.stl
58.0 x 44.5 x 14.3
