fablabbcn/smartcitizen-enclosures/docs/Components/PMS5003/PMS5003.step

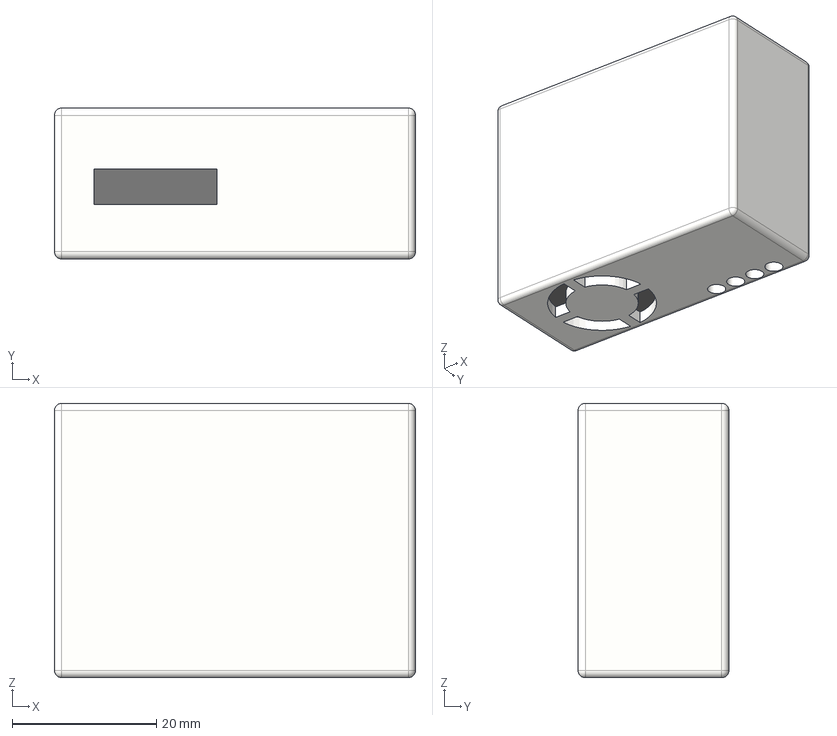
[picture p86: CAD file, 2020-04-24]
docs/Components/PMS5003/PMS5003.step
50.0 x 20.9 x 38.0 mm
