fablabbcn/smartcitizen-enclosures/docs/Components/POWER HUB/power-hub v4.step

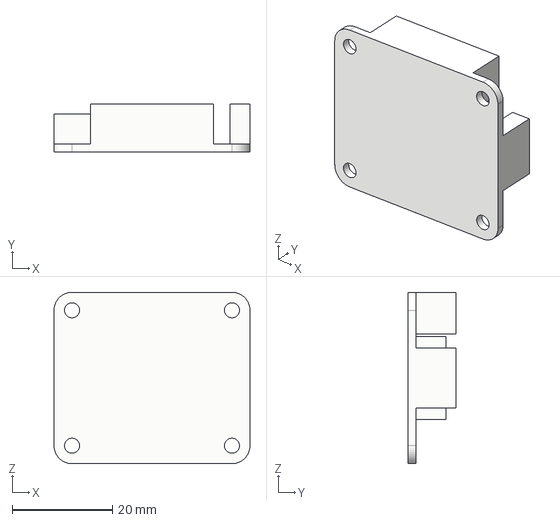
[picture p87: CAD file, 2023-10-24]
docs/Components/POWER HUB/power-hub v4.step
39.1 x 9.60 x 34.2 mm
