fablabbcn/smartcitizen-enclosures/docs/Components/RESET/sc_reset_small v1.step

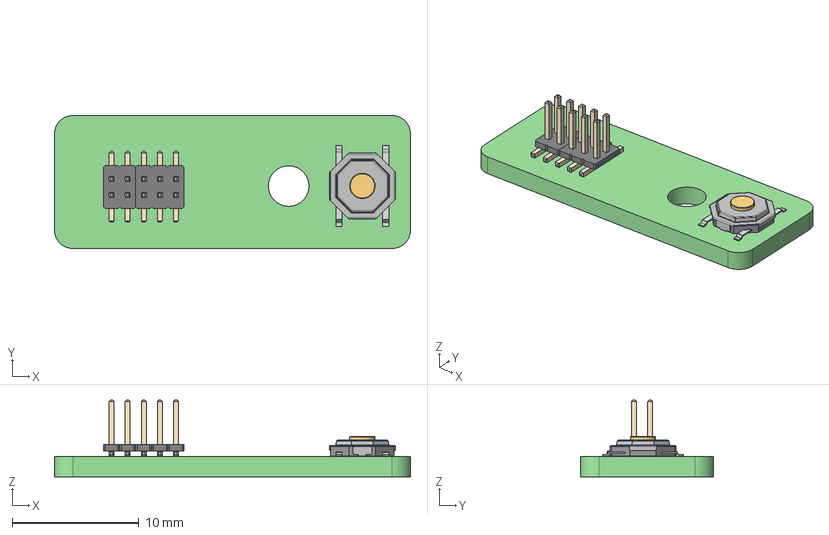
[picture p88: CAD file, 2023-10-24]
docs/Components/RESET/sc_reset_small v1.step
28.1 x 10.5 x 6.05 mm
