fablabbcn/smartcitizen-enclosures/docs/Components/SCD30/sensirion-scd30 v10.step

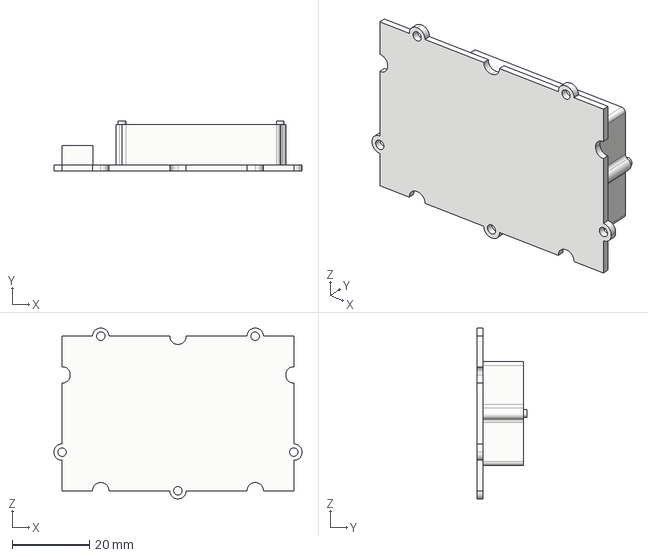
[picture p89: CAD file, 2023-10-24]
docs/Components/SCD30/sensirion-scd30 v10.step
64.2 x 13.0 x 44.2 mm
