fablabbcn/smartcitizen-enclosures/docs/Components/SCK/SCK2.1/sc-pm-board.stl

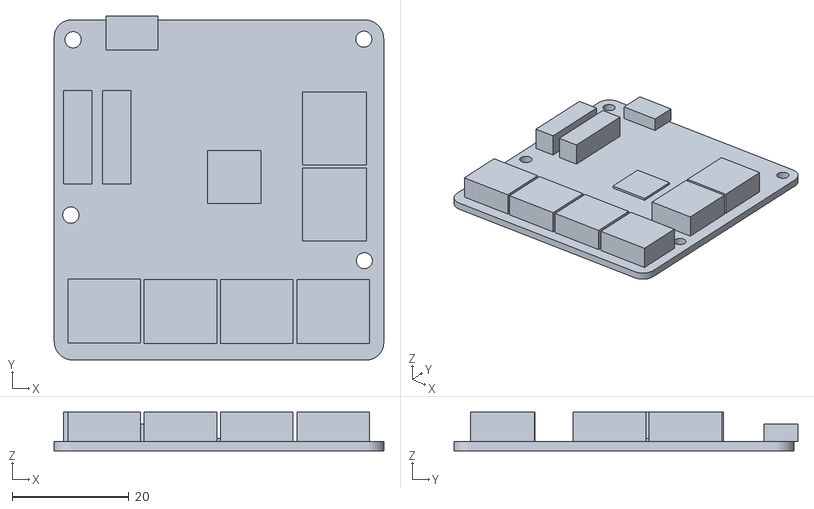
[picture p90: CAD file, 2022-07-28]
docs/Components/SCK/SCK2.1/sc-pm-board.stl
56.4 x 58.9 x 6.60
