fablabbcn/smartcitizen-enclosures/docs/Components/SEN5x/SEN5x mechanical design-in example.stl

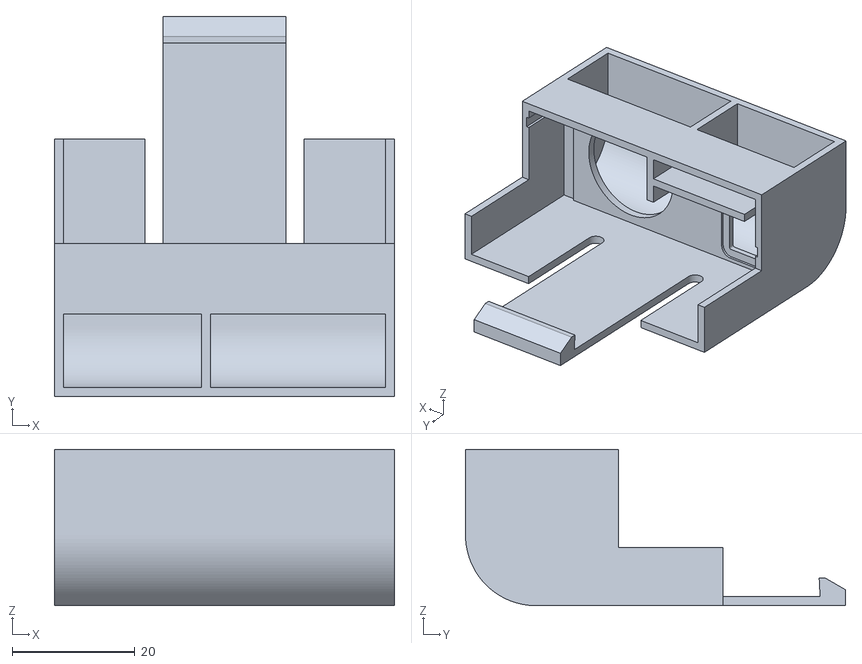
[picture p91: CAD file, 2025-06-26]
docs/Components/SEN5x/SEN5x mechanical design-in example.stl
55.5 x 62.0 x 25.5
