fablabbcn/smartcitizen-enclosures/docs/Components/SEN6x/SEN6x_Example_Retainer.stl

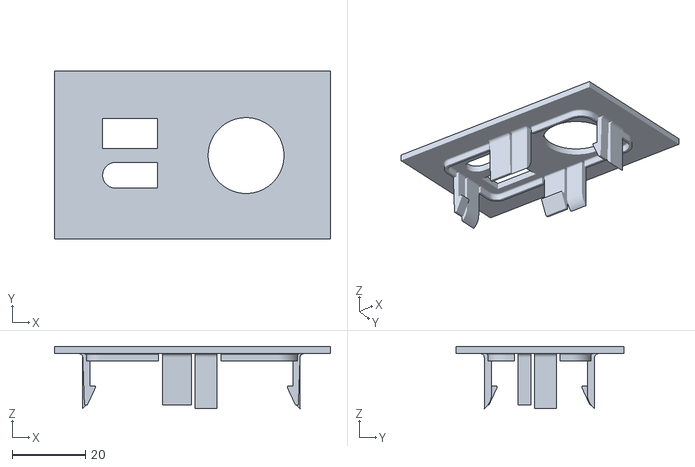
[picture p92: CAD file, 2025-06-26]
docs/Components/SEN6x/SEN6x_Example_Retainer.stl
75.5 x 45.9 x 17.0
