fablabbcn/smartcitizen-enclosures/docs/Components/SFA30/sensirion-sfa30 v4.step

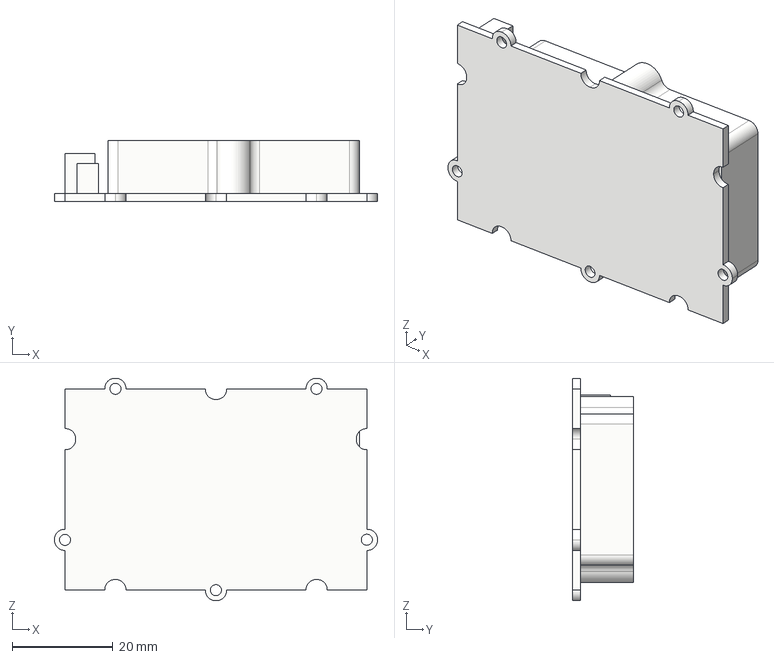
[picture p93: CAD file, 2023-10-28]
docs/Components/SFA30/sensirion-sfa30 v4.step
64.2 x 12.0 x 44.2 mm
