fablabbcn/smartcitizen-enclosures/docs/Power Options/Power hub/power-routing/exports/power-routing.step

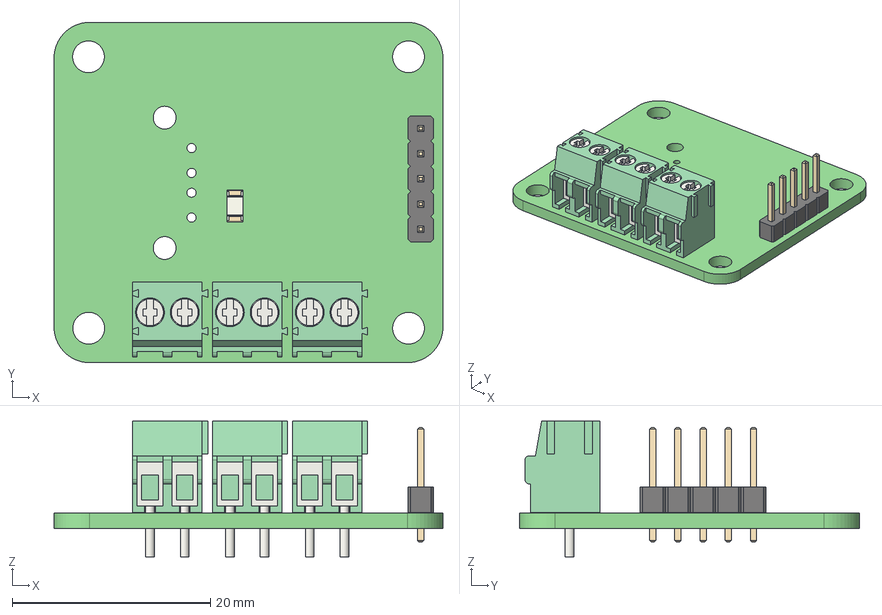
[picture p94: CAD file, 2021-07-12]
docs/Power Options/Power hub/power-routing/exports/power-routing.step
39.2 x 34.3 x 13.7 mm
