fablabbcn/smartcitizen-enclosures/docs/Power Options/Solar/FLANGE3mm.stl

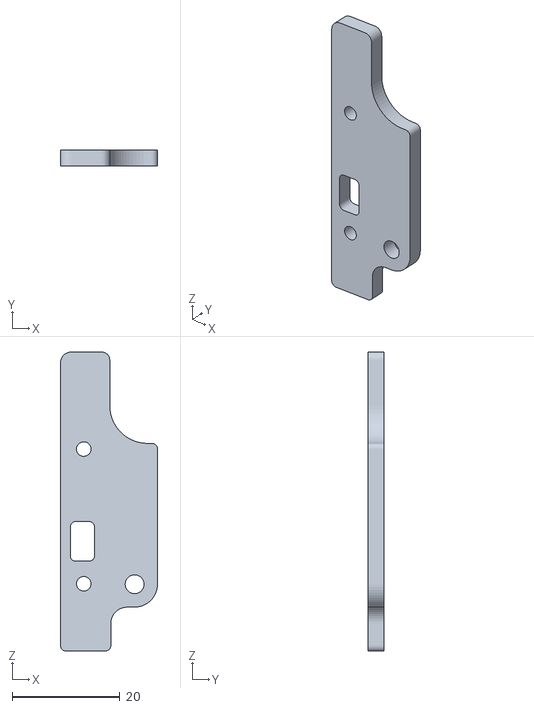
[picture p95: CAD file, 2020-04-28]
docs/Power Options/Solar/FLANGE3mm.stl
18.0 x 3.00 x 55.5
