fablabbcn/smartcitizen-enclosures/docs/Testing Units/Air Cabin/components/Ganxu.stl

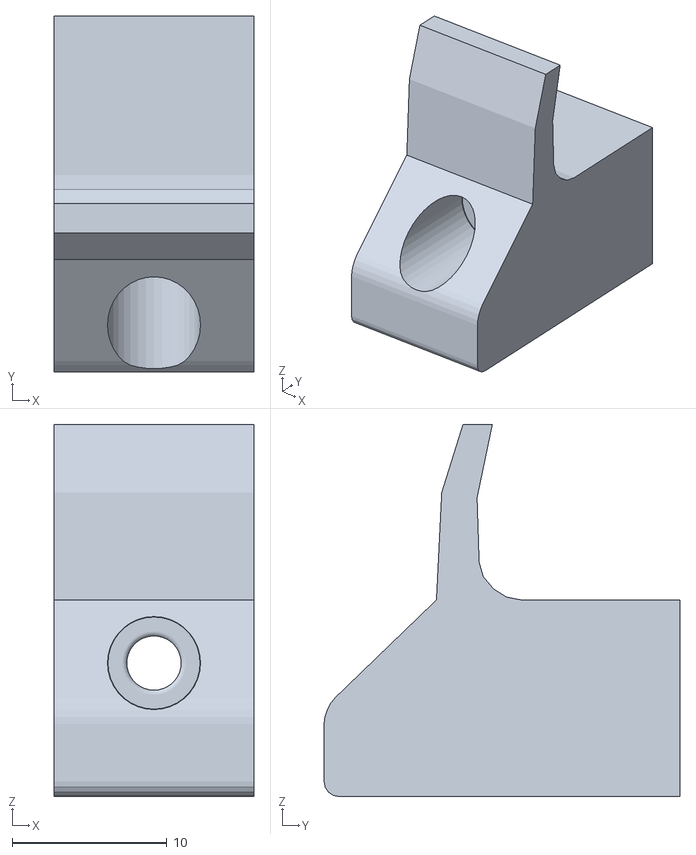
[picture p96: CAD file, 2024-05-23]
docs/Testing Units/Air Cabin/components/Ganxu.stl
12.9 x 23.0 x 24.0
