fablabbcn/smartcitizen-enclosures/docs/Water/Electronics/SmartCitizen Water Kit/IP Box One Carrier/Components/Carrier_holder.stl

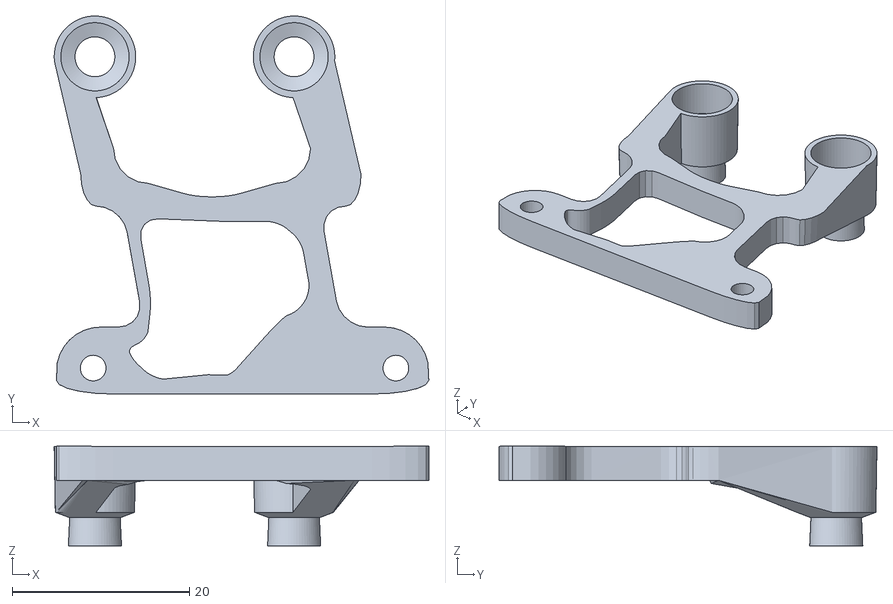
[picture p97: CAD file, 2023-07-28]
docs/Water/Electronics/SmartCitizen Water Kit/IP Box One Carrier/Components/Carrier_holder.stl
42.3 x 42.6 x 11.2
