fablabbcn/smartcitizen-enclosures/docs/Water/Electronics/SmartCitizen Water Station/Isolated Carriers Station/Components/3D printed/Clamp_acrylic.stl

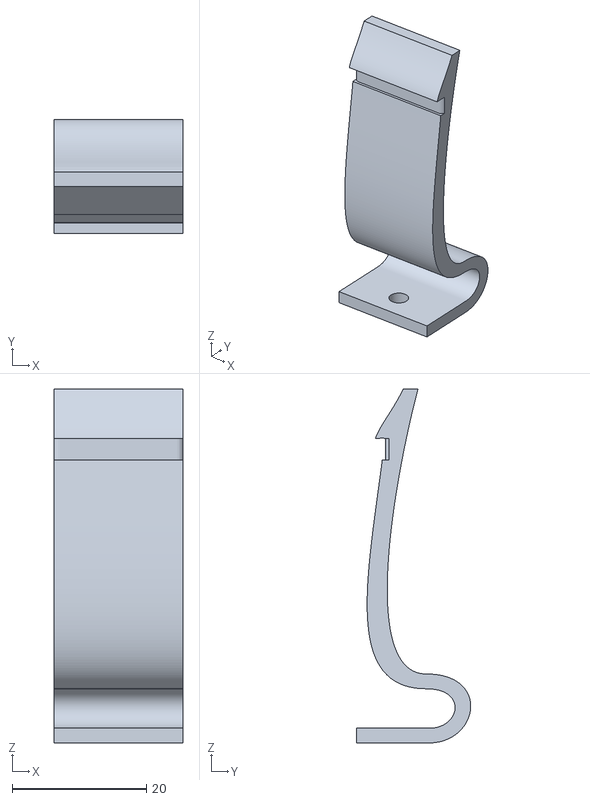
[picture p98: CAD file, 2023-10-23]
docs/Water/Electronics/SmartCitizen Water Station/Isolated Carriers Station/Components/3D printed/Clamp_acrylic.stl
19.2 x 17.0 x 52.7
