fablabbcn/smartcitizen-enclosures/docs/Water/Electronics/SmartCitizen Water Station/Isolated Carriers Station/Components/Acrylics/ACRYLIC-TOP.dxf

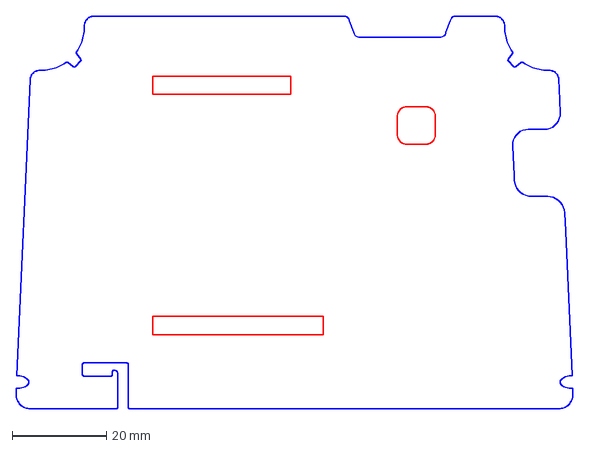
[picture p99: CAD file, 2023-10-23]
docs/Water/Electronics/SmartCitizen Water Station/Isolated Carriers Station/Components/Acrylics/ACRYLIC-TOP.dxf
118.0 x 83.2 mm
