fablabbcn/smartcitizen-enclosures/docs/Water/Probe Holders/multiple/components/cable_protectors/cable-clip_BNC.stl

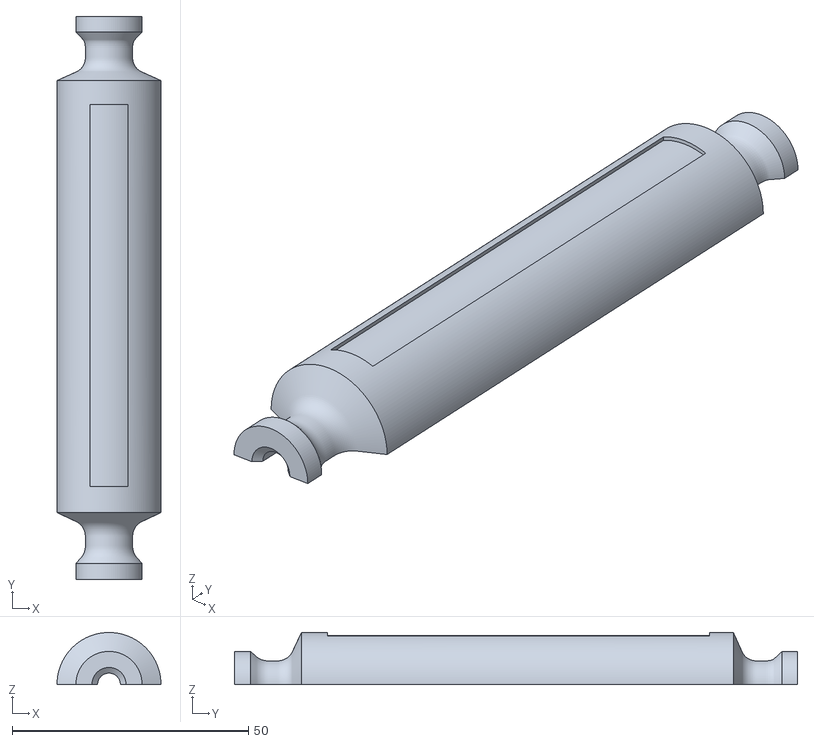
[picture p100: CAD file, 2024-04-16]
docs/Water/Probe Holders/multiple/components/cable_protectors/cable-clip_BNC.stl
22.0 x 119.1 x 11.0
