fablabbcn/smartcitizen-enclosures/docs/Water/Probe Holders/multiple/components/hook/hook-part2.stl

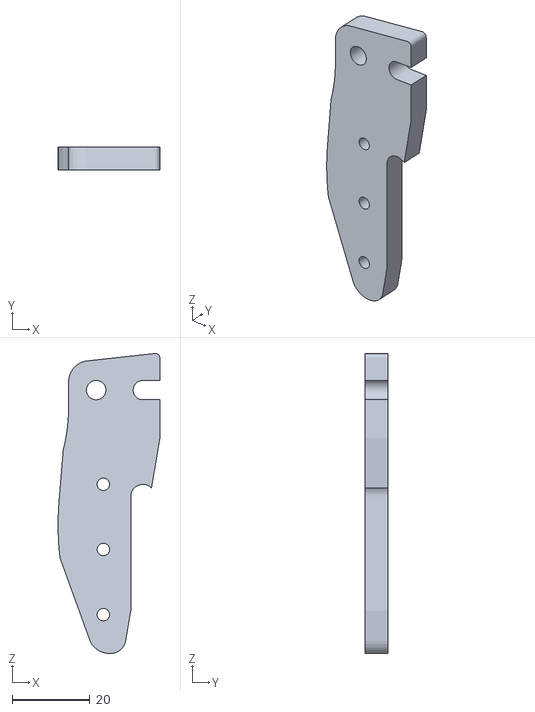
[picture p101: CAD file, 2024-03-19]
docs/Water/Probe Holders/multiple/components/hook/hook-part2.stl
26.2 x 6.00 x 77.1
