fablabbcn/smartcitizen-enclosures/docs/Water/Probe Holders/multiple/components/metalic-zipTie-enforcer.stl

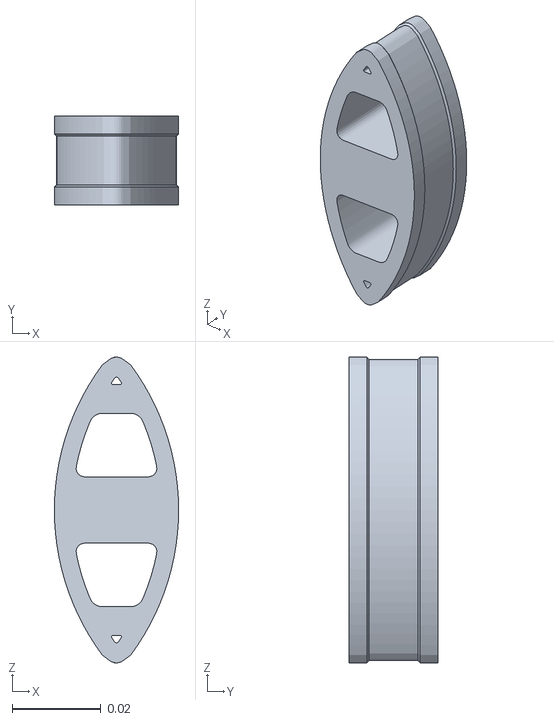
[picture p102: CAD file, 2024-05-06]
docs/Water/Probe Holders/multiple/components/metalic-zipTie-enforcer.stl
0.0281 x 0.02 x 0.0691
