fablabbcn/smartcitizen-enclosures/docs/Water/Probe Holders/multiple/components/tool/tool-cover.stl

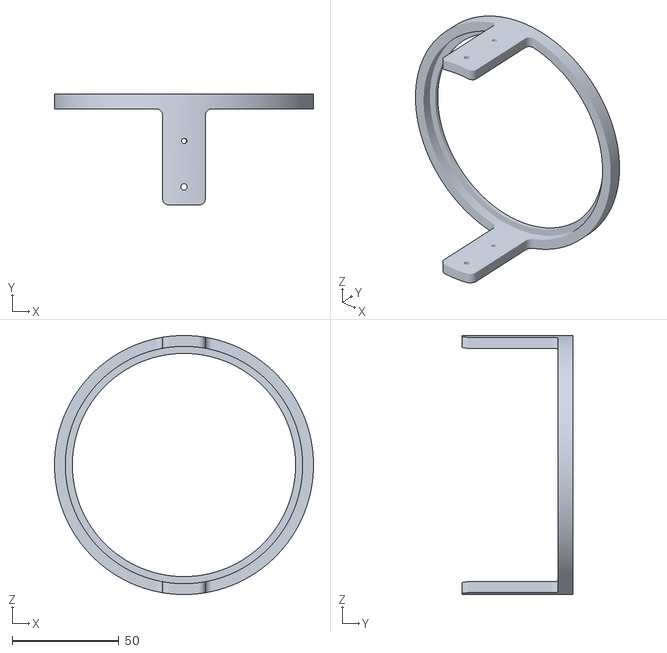
[picture p103: CAD file, 2023-09-08]
docs/Water/Probe Holders/multiple/components/tool/tool-cover.stl
121.1 x 52.0 x 121.2
