fablabbcn/smartcitizen-enclosures/docs/Water/Probe Holders/single/components/holder.stl

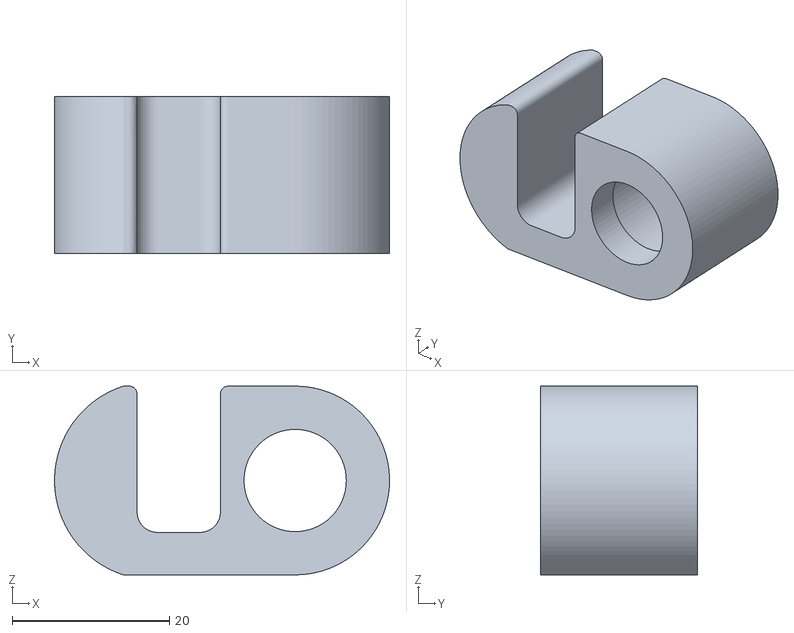
[picture p104: CAD file, 2022-11-16]
docs/Water/Probe Holders/single/components/holder.stl
42.6 x 20.0 x 24.0
