fablabbcn/smartcitizen-enclosures/SmartCitizen Air Enclosures/SCK2.1/SCK2.1 with PM Sensor/SCK2.1_PMS5003/3D Printed frog box v1/components/clamp_01.stl

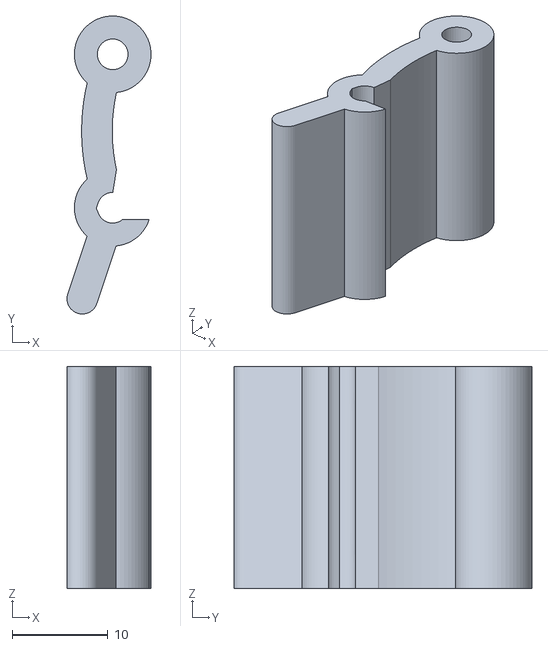
[picture p105: CAD file, 2024-03-19]
SmartCitizen Air Enclosures/SCK2.1/SCK2.1 with PM Sensor/SCK2.1_PMS5003/3D Printed frog box v1/components/clamp_01.stl
8.77 x 31.1 x 23.2
