fablabbcn/smartcitizen-enclosures/SmartCitizen Air Enclosures/SCK2.2/SCK2.2 with PM Sensor/SCK2.2_SEN5X/3D printed frog box INDOOR/components/latch_hinge.stl

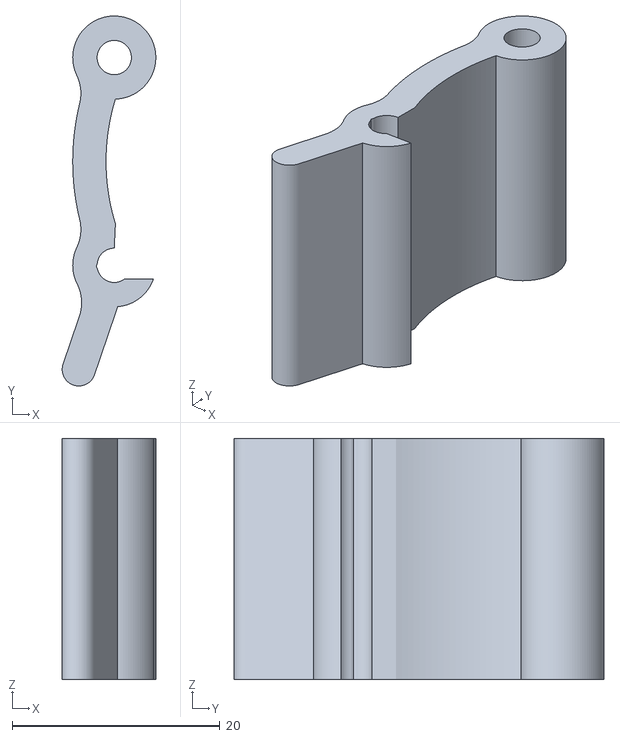
[picture p106: CAD file, 2023-10-28]
SmartCitizen Air Enclosures/SCK2.2/SCK2.2 with PM Sensor/SCK2.2_SEN5X/3D printed frog box INDOOR/components/latch_hinge.stl
9.01 x 35.6 x 23.2
