fablabbcn/smartcitizen-enclosures/SmartCitizen Air Enclosures/SCK2.2/SCK2.2 with PM Sensor/SCK2.2_SEN5X/3D printed frog box/components/SCKit_base.stl

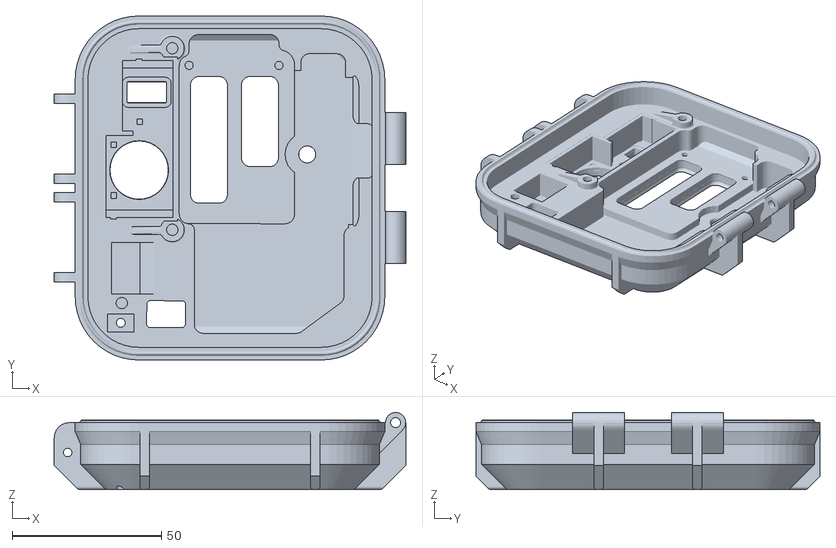
[picture p107: CAD file, 2024-02-13]
SmartCitizen Air Enclosures/SCK2.2/SCK2.2 with PM Sensor/SCK2.2_SEN5X/3D printed frog box/components/SCKit_base.stl
117.7 x 115.2 x 25.8
