fablabbcn/smartcitizen-enclosures/SmartCitizen Outdoor Cases V2.*/SCK2.1_PMS5003_CO2/3D Printed/components/base.stl

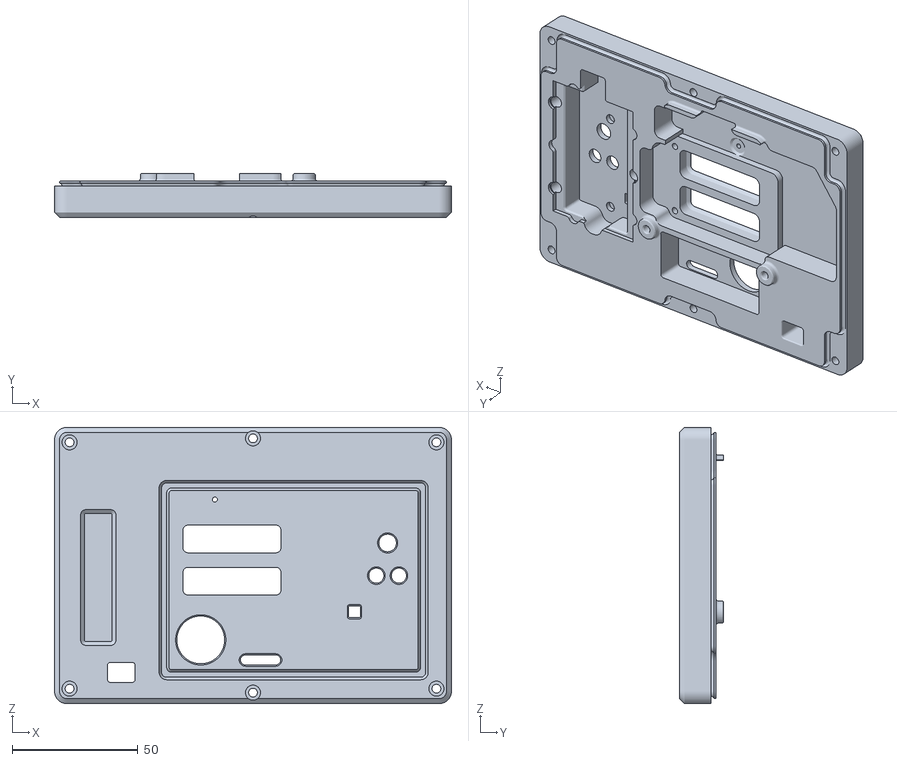
[picture p108: CAD file, 2021-06-21]
SmartCitizen Outdoor Cases V2.*/SCK2.1_PMS5003_CO2/3D Printed/components/base.stl
158.0 x 17.5 x 110.0
