fablabbcn/smartcitizen-enclosures/SmartCitizen Water Enclosures/Probe Holders/bulk/components/adaptor-do.step

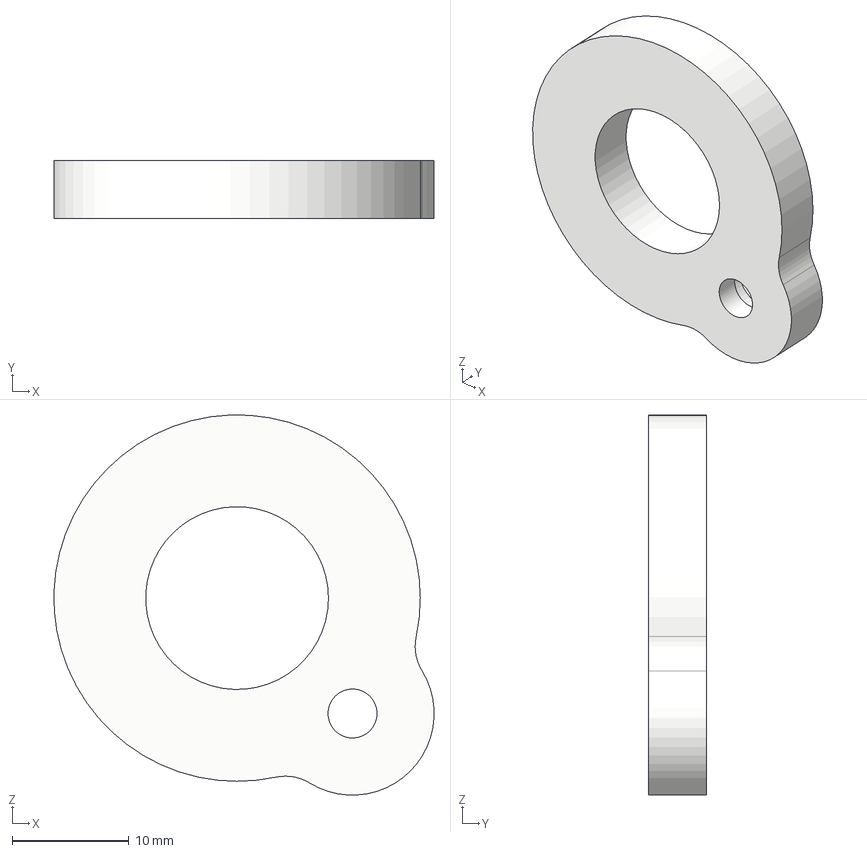
[picture p109: CAD file, 2022-11-16]
SmartCitizen Water Enclosures/Probe Holders/bulk/components/adaptor-do.step
32.6 x 5.00 x 32.6 mm
