fablabbcn/smartcitizen-enclosures/SmartCitizen Water Enclosures/SmartCitizen Water Station/Tentacle Water Station/components/sep_hex.stl

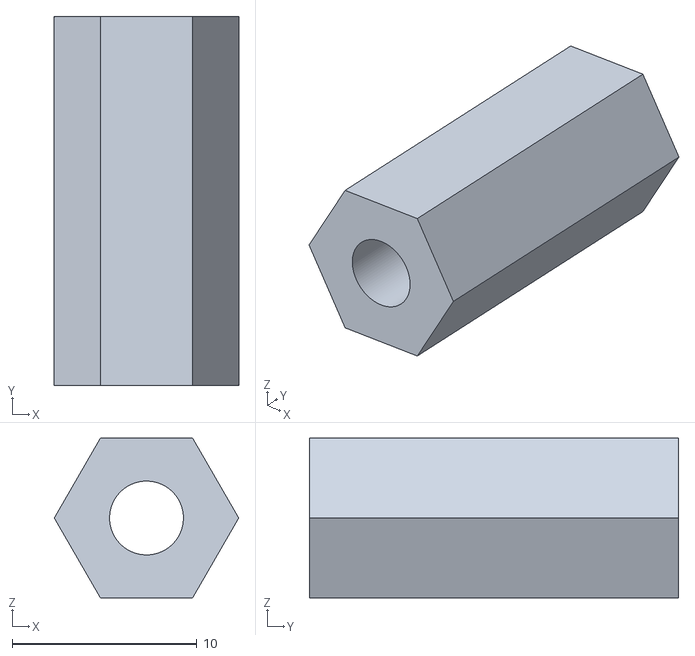
[picture p110: CAD file, 2022-11-16]
SmartCitizen Water Enclosures/SmartCitizen Water Station/Tentacle Water Station/components/sep_hex.stl
10.0 x 20.0 x 8.66
