fablabbcn/smartcitizen-enclosures/docs/Air/misc/CONNECTIVITY_UNIT/base-template.dxf

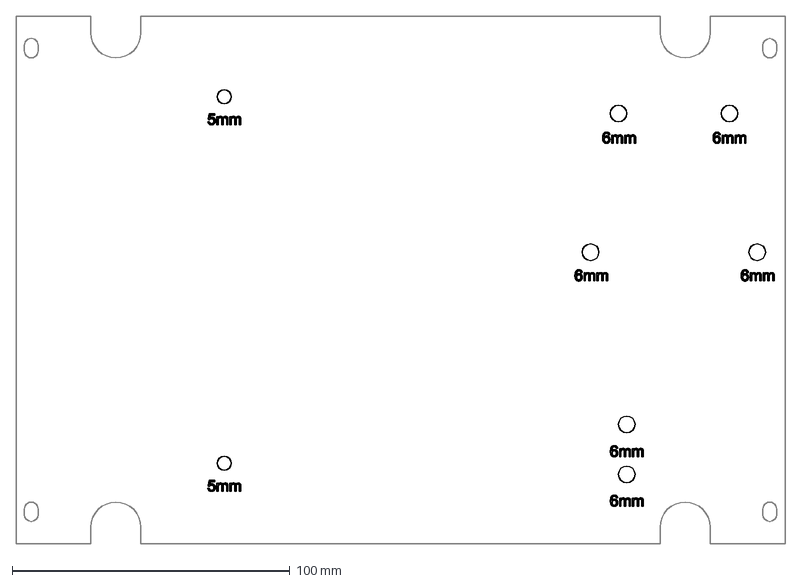
[picture p111: CAD file, 2020-09-15]
docs/Air/misc/CONNECTIVITY_UNIT/base-template.dxf
277.0 x 190.0 mm
