fablabbcn/smartcitizen-enclosures/docs/Air/misc/SCK2.1_ANALOG_BOX/components/clip.stl

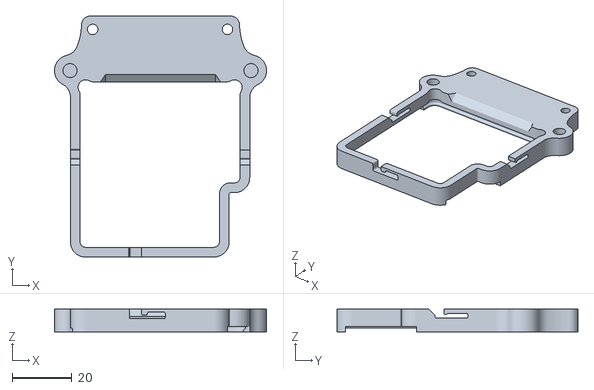
[picture p112: CAD file, 2023-01-04]
docs/Air/misc/SCK2.1_ANALOG_BOX/components/clip.stl
70.8 x 80.4 x 7.60
