fablabbcn/smartcitizen-enclosures/docs/Air/misc/SCK2.1_BIKE_SADDLEBAG/components/inlet-l-shell.stl

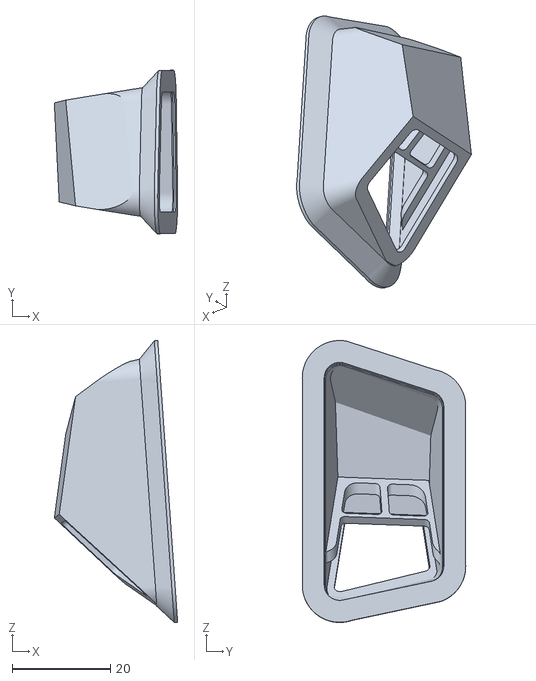
[picture p113: CAD file, 2020-11-11]
docs/Air/misc/SCK2.1_BIKE_SADDLEBAG/components/inlet-l-shell.stl
25.1 x 33.2 x 57.3
