fablabbcn/smartcitizen-enclosures/docs/Air/SCK2.1/SCK2.1_2PMS5003_4EC/4-electrochemical-alphasense-2pm/components/base.stl

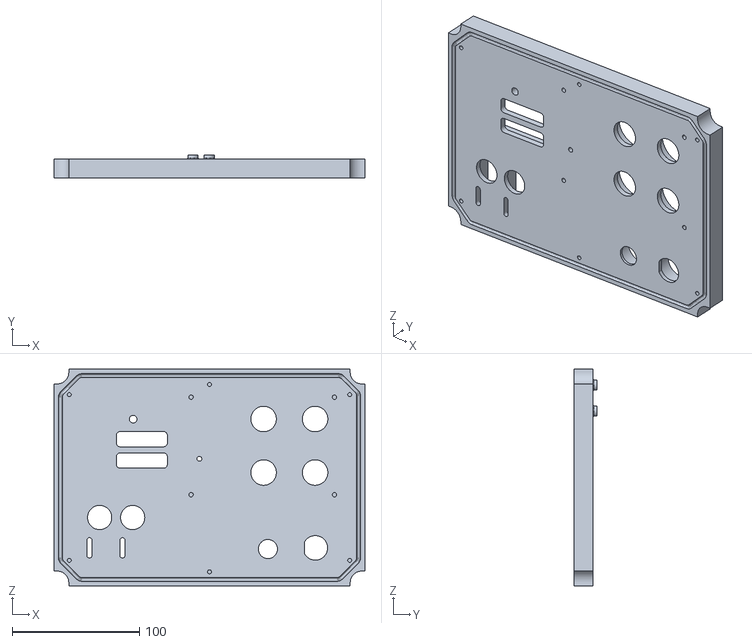
[picture p114: CAD file, 2023-06-14]
docs/Air/SCK2.1/SCK2.1_2PMS5003_4EC/4-electrochemical-alphasense-2pm/components/base.stl
244.0 x 18.0 x 170.0
