fablabbcn/smartcitizen-enclosures/docs/Air/SCK2.1/SCK2.1_2PMS5003_4EC_CO2/4-electrochemical-2pm-co2/components/plate.dxf

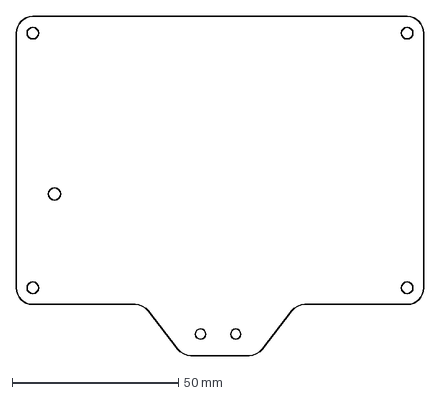
[picture p115: CAD file, 2023-02-16]
docs/Air/SCK2.1/SCK2.1_2PMS5003_4EC_CO2/4-electrochemical-2pm-co2/components/plate.dxf
122.4 x 101.8 mm
