fablabbcn/smartcitizen-enclosures/docs/Air/SCK2.1/SCK2.1_2PMS5003_6EC/6-electrochemical-spec-2pm/components/3DPRINTING/clip-spec.stl

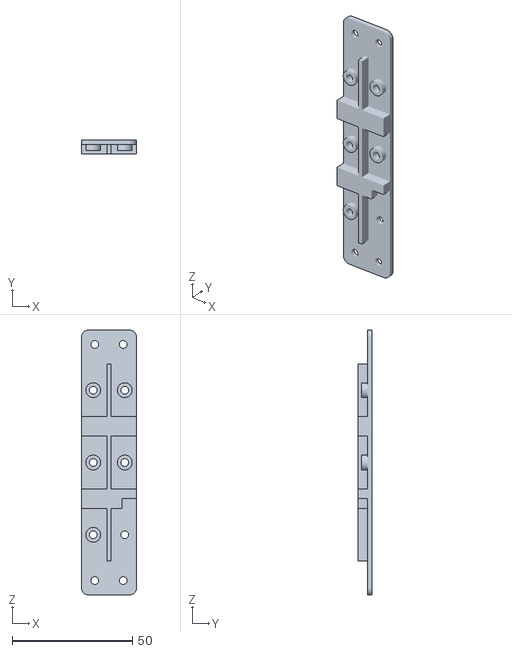
[picture p116: CAD file, 2023-01-04]
docs/Air/SCK2.1/SCK2.1_2PMS5003_6EC/6-electrochemical-spec-2pm/components/3DPRINTING/clip-spec.stl
22.9 x 5.95 x 110.0
