fablabbcn/smartcitizen-enclosures/docs/Air/SCK2.1/SCK2.1_2PMS5003_6EC/6-electrochemical-spec-2pm/components/LASERCUT/acrylic-oleds.dxf

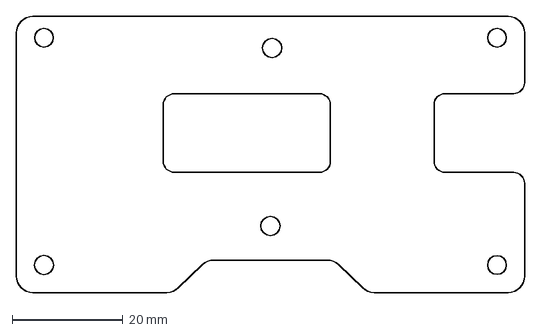
[picture p117: CAD file, 2023-01-04]
docs/Air/SCK2.1/SCK2.1_2PMS5003_6EC/6-electrochemical-spec-2pm/components/LASERCUT/acrylic-oleds.dxf
92.0 x 50.0 mm
