fablabbcn/smartcitizen-enclosures/docs/Air/SCK2.1/SCK2.1_PMS5003/3D Printed + HDPE/components/LOCK.stl

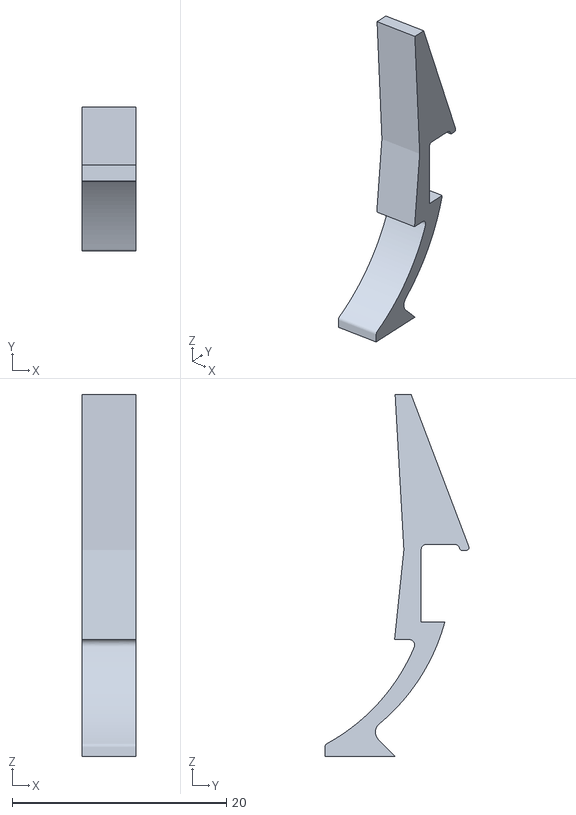
[picture p118: CAD file, 2019-09-09]
docs/Air/SCK2.1/SCK2.1_PMS5003/3D Printed + HDPE/components/LOCK.stl
5.00 x 13.5 x 33.8
