fablabbcn/smartcitizen-enclosures/docs/Air/SCK2.1/SCK2.1_PMS5003/3D Printed Modular Viadukaduk/components/sck2.1_enclosure_vdk_1.0_top.stl

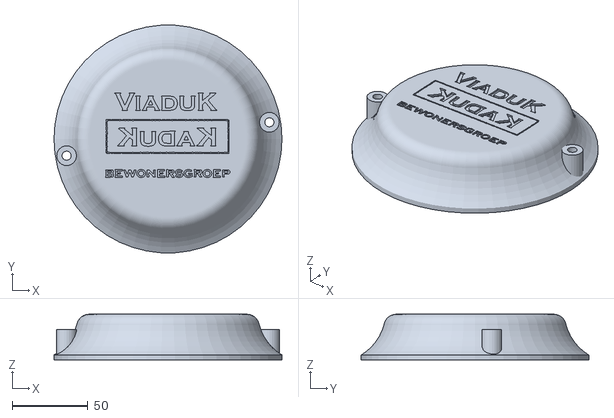
[picture p119: CAD file, 2021-02-11]
docs/Air/SCK2.1/SCK2.1_PMS5003/3D Printed Modular Viadukaduk/components/sck2.1_enclosure_vdk_1.0_top.stl
150.0 x 149.7 x 30.0
