fablabbcn/smartcitizen-enclosures/docs/Air/SCK2.1/SCK2.1_PMS5003/3D Printed Prototype/components/BASE.step

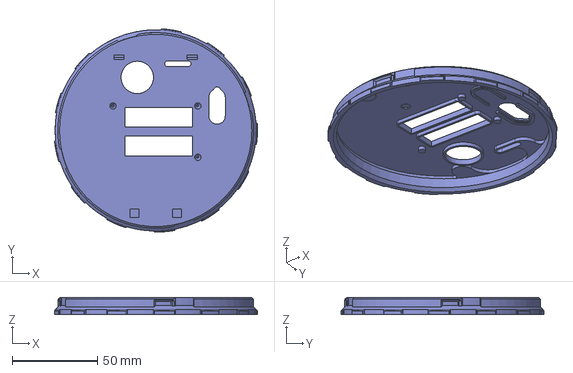
[picture p120: CAD file, 2020-04-24]
docs/Air/SCK2.1/SCK2.1_PMS5003/3D Printed Prototype/components/BASE.step
119.0 x 119.3 x 10.0 mm
