fablabbcn/smartcitizen-enclosures/docs/Air/SCK2.1/SCK2.1_PMS5003/3D Printed Slim/base.stl

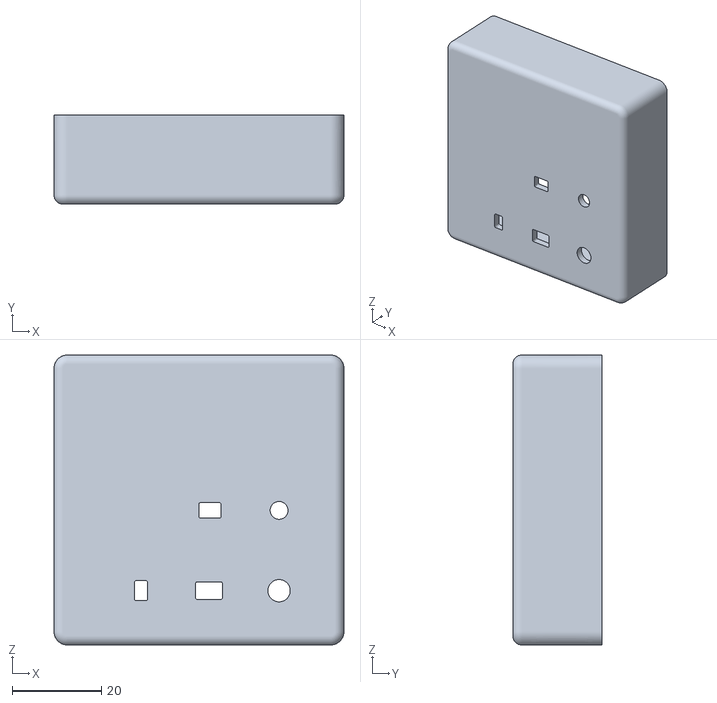
[picture p121: CAD file, 2021-03-25]
docs/Air/SCK2.1/SCK2.1_PMS5003/3D Printed Slim/base.stl
65.0 x 20.0 x 65.0
