fablabbcn/smartcitizen-enclosures/docs/Air/SCK2.1/SCK2.1_PMS5003/3D Printed square/components/holder-extras-short.stl

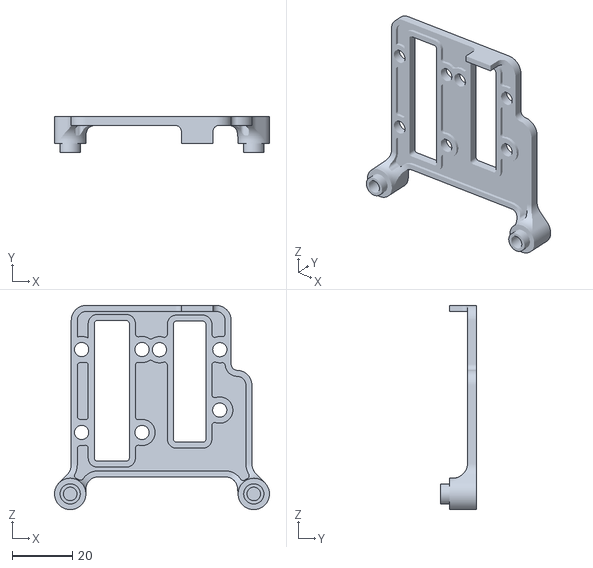
[picture p122: CAD file, 2023-02-09]
docs/Air/SCK2.1/SCK2.1_PMS5003/3D Printed square/components/holder-extras-short.stl
71.2 x 12.0 x 67.6
