fablabbcn/smartcitizen-enclosures/docs/Air/SCK2.1/SCK2.1_PMS5003/CNC HDPE circle/components/clip-foam-reduced.stl

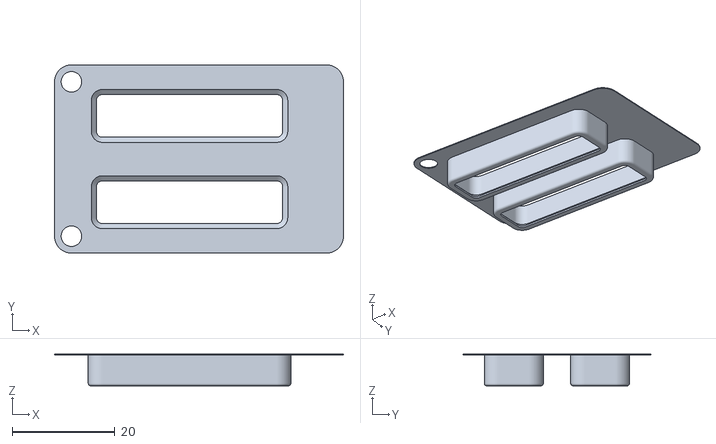
[picture p123: CAD file, 2021-02-23]
docs/Air/SCK2.1/SCK2.1_PMS5003/CNC HDPE circle/components/clip-foam-reduced.stl
56.3 x 36.7 x 6.20
