fablabbcn/smartcitizen-enclosures/docs/Air/SCK2.1/SCK2.1_PMS5003/CNC HDPE square/components/cover.stl

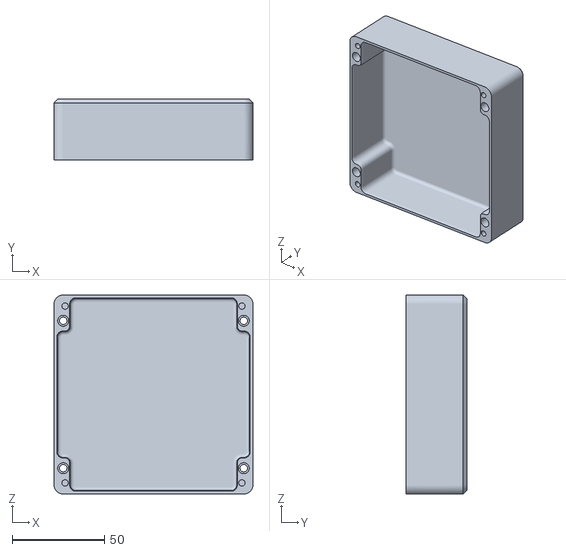
[picture p124: CAD file, 2021-04-12]
docs/Air/SCK2.1/SCK2.1_PMS5003/CNC HDPE square/components/cover.stl
108.0 x 33.0 x 108.0
