fablabbcn/smartcitizen-enclosures/docs/Air/SCK2.1/SCK2.1_PMS5003/SCK_3Dprint_Assembly_GER_EN_USTTG_IIGS_2023/sck_17-spacer.stl

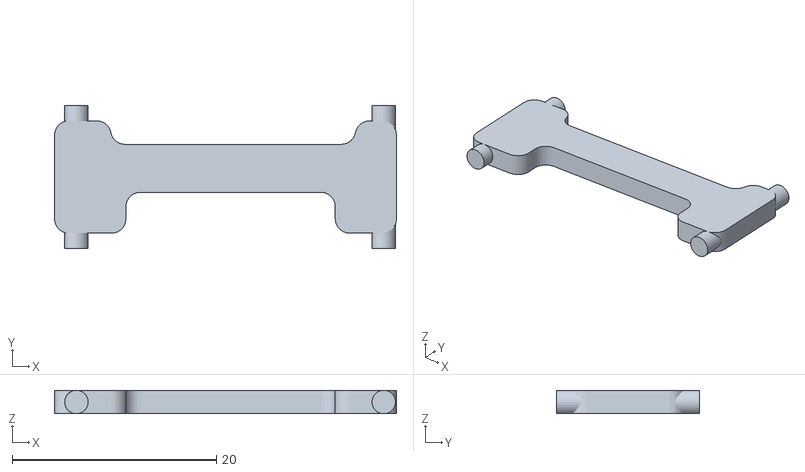
[picture p125: CAD file, 2024-04-08]
docs/Air/SCK2.1/SCK2.1_PMS5003/SCK_3Dprint_Assembly_GER_EN_USTTG_IIGS_2023/sck_17-spacer.stl
33.5 x 14.0 x 2.30
