fablabbcn/smartcitizen-enclosures/docs/Air/SCK2.1/SCK2.1_PMS5003/UMBRELLA/components/#pletina_unfold.dxf

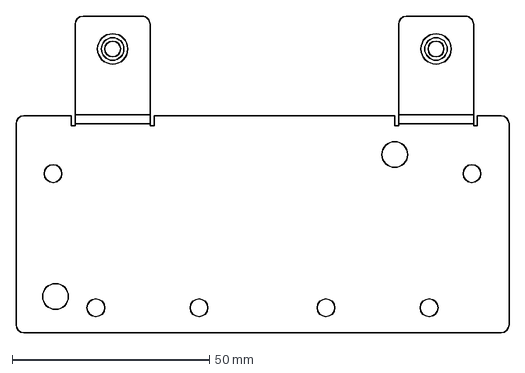
[picture p126: CAD file, 2024-01-18]
docs/Air/SCK2.1/SCK2.1_PMS5003/UMBRELLA/components/#pletina_unfold.dxf
125.0 x 80.3 mm
