fablabbcn/smartcitizen-enclosures/docs/Air/SCK2.1/SCK2.1_PMS5003_2EC/3D Printed/components/base.step

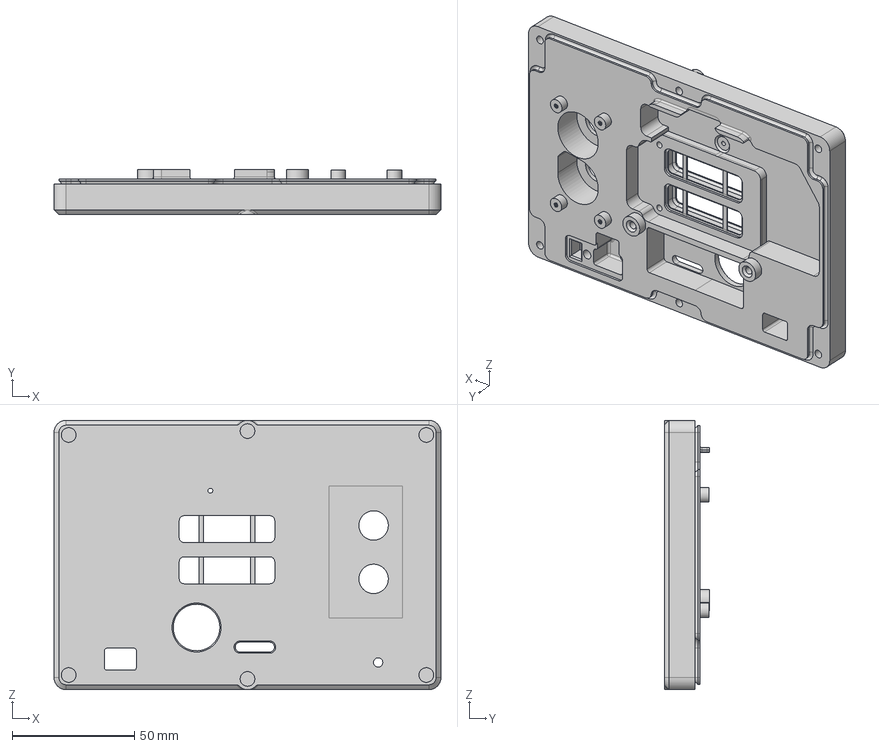
[picture p127: CAD file, 2022-02-03]
docs/Air/SCK2.1/SCK2.1_PMS5003_2EC/3D Printed/components/base.step
158.0 x 18.5 x 110.0 mm
