fablabbcn/smartcitizen-enclosures/docs/Air/SCK2.1/SCK2.1_PMS5003_2EC_CO2/(WIP) IP Box/clip_sck v1.stl

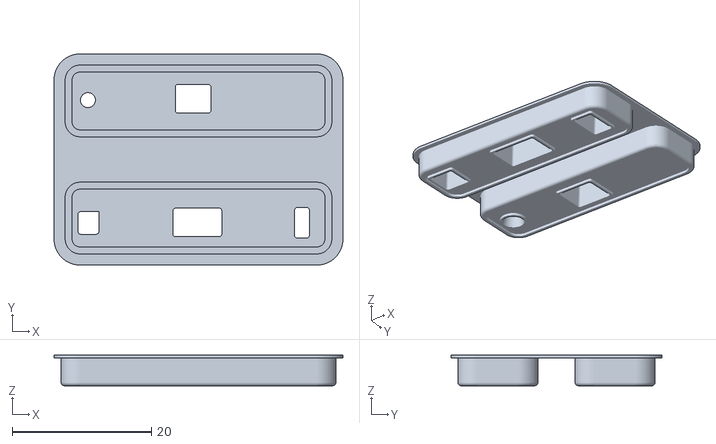
[picture p128: CAD file, 2023-01-04]
docs/Air/SCK2.1/SCK2.1_PMS5003_2EC_CO2/(WIP) IP Box/clip_sck v1.stl
41.5 x 30.3 x 4.40
