fablabbcn/smartcitizen-enclosures/docs/Air/SCK2.1/SCK2.1_SPS30/3D Printed Square/components/base_sps30_draft.stl

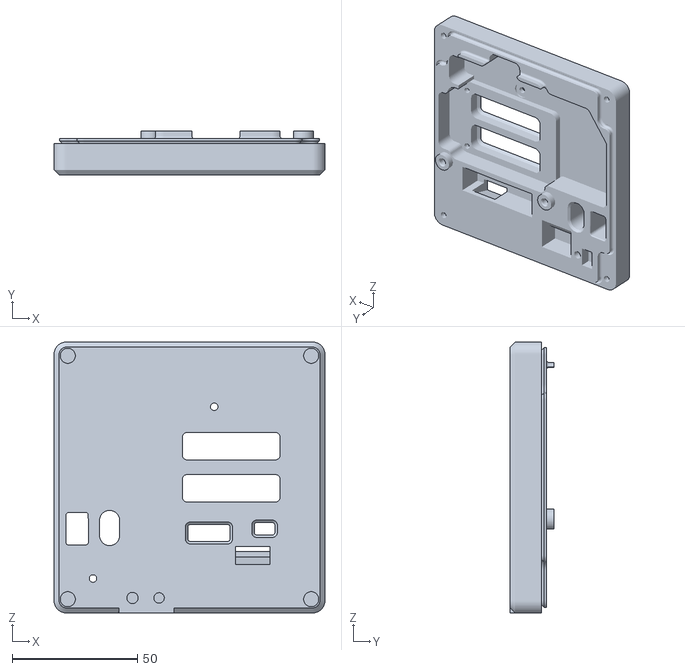
[picture p130: CAD file, 2023-05-23]
docs/Air/SCK2.1/SCK2.1_SPS30/3D Printed Square/components/base_sps30_draft.stl
108.0 x 17.5 x 108.0
