fablabbcn/smartcitizen-enclosures/docs/Air/SCK2.2/SCK2.2_SEN5X/3D printed outdoor/components/baseLOW.stl

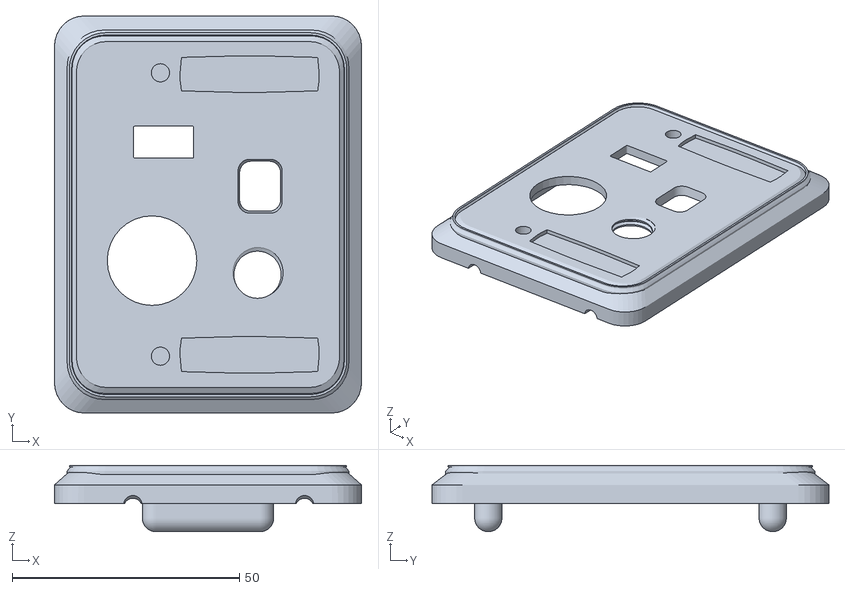
[picture p131: CAD file, 2024-11-13]
docs/Air/SCK2.2/SCK2.2_SEN5X/3D printed outdoor/components/baseLOW.stl
67.5 x 87.3 x 14.6
