fablabbcn/smartcitizen-enclosures/docs/Air/SCK2.3/SCK2.3_SEN5X/3D_printed_frog_box/components/cover_outdoor.3mf

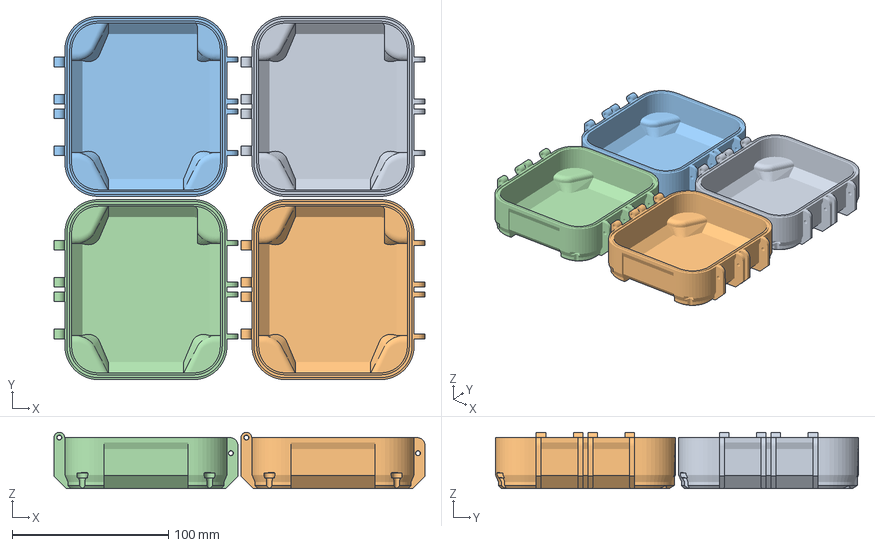
[picture p132: CAD file, 2025-08-28]
docs/Air/SCK2.3/SCK2.3_SEN5X/3D_printed_frog_box/components/cover_outdoor.3mf
237.3 x 232.3 x 36.1 mm
cover_outdoor.stl
cover_outdoor.stl 1
cover_outdoor.stl 2
cover_outdoor.stl 3
