fablabbcn/smartcitizen-enclosures/docs/Air/shared/large/cover_multipurpose.stl

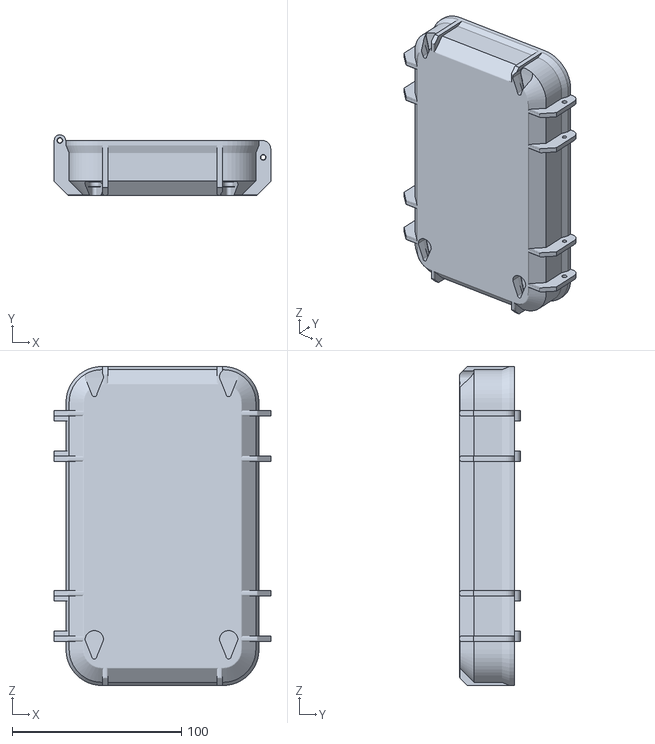
[picture p133: CAD file, 2024-02-28]
docs/Air/shared/large/cover_multipurpose.stl
128.0 x 35.8 x 188.5
