fablabbcn/smartcitizen-enclosures/docs/Air/shared/medium/cover_multipurpose.stl

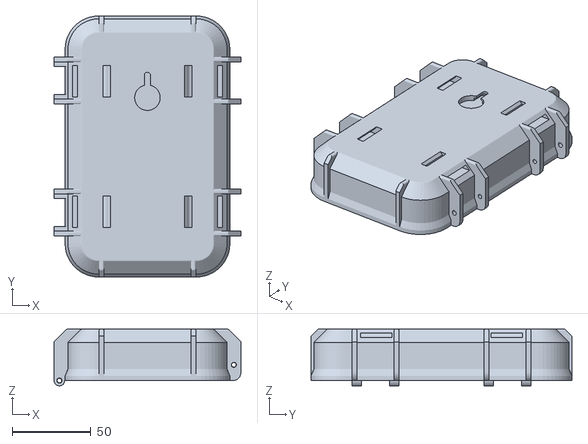
[picture p134: CAD file, 2024-09-17]
docs/Air/shared/medium/cover_multipurpose.stl
118.9 x 166.0 x 36.1
