fablabbcn/smartcitizen-enclosures/docs/Air/shared/umbrella/components/#umbrella-medium.dxf

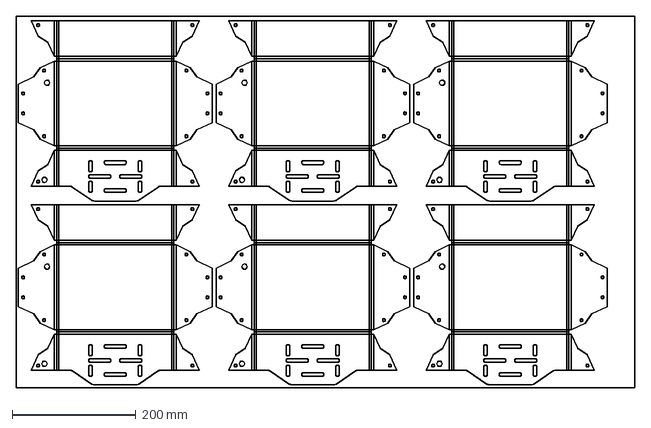
[picture p135: CAD file, 2024-11-13]
docs/Air/shared/umbrella/components/#umbrella-medium.dxf
1000.0 x 600.0 mm
