fablabbcn/smartcitizen-enclosures/docs/Components/ALPHASENSE/alphasense-b4 v4.step

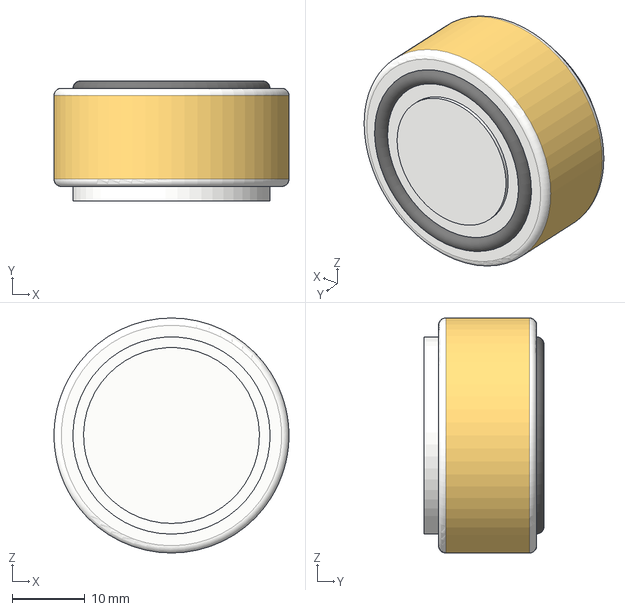
[picture p136: CAD file, 2023-10-24]
docs/Components/ALPHASENSE/alphasense-b4 v4.step
32.3 x 16.5 x 32.3 mm
