fablabbcn/smartcitizen-enclosures/docs/Components/SCK/SCK2.1/sck-2.x v13.step

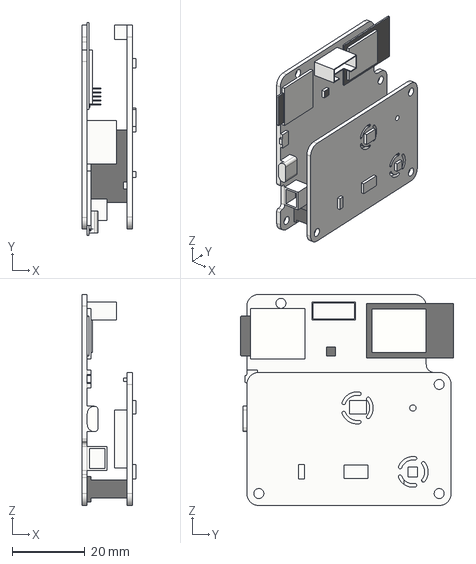
[picture p137: CAD file, 2022-05-18]
docs/Components/SCK/SCK2.1/sck-2.x v13.step
15.0 x 58.7 x 58.2 mm
