fablabbcn/smartcitizen-enclosures/docs/Testing Units/Water Wall/components/Cable_Holder_v1.stl

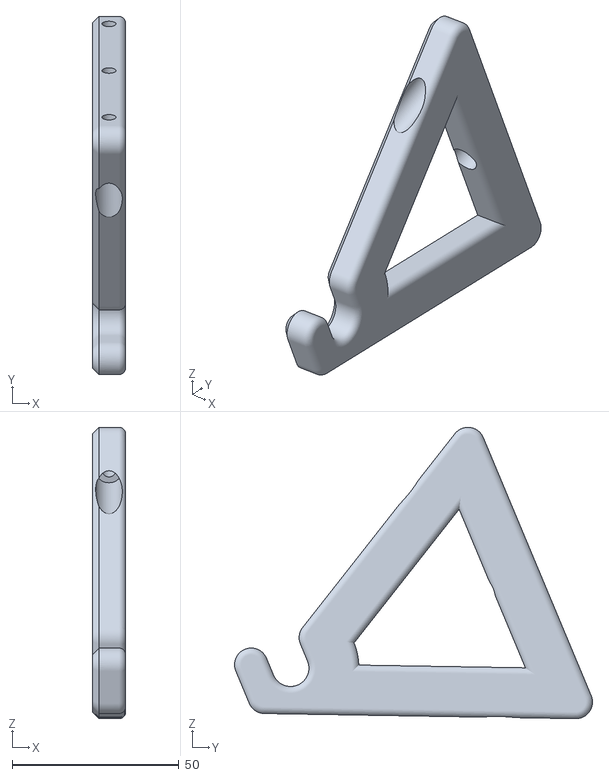
[picture p138: CAD file, 2024-04-24]
docs/Testing Units/Water Wall/components/Cable_Holder_v1.stl
10.0 x 107.3 x 87.4
