fablabbcn/smartcitizen-enclosures/docs/Water/Electronics/SmartCitizen Water Kit/IP Box One Carrier/Components/SEP.stl

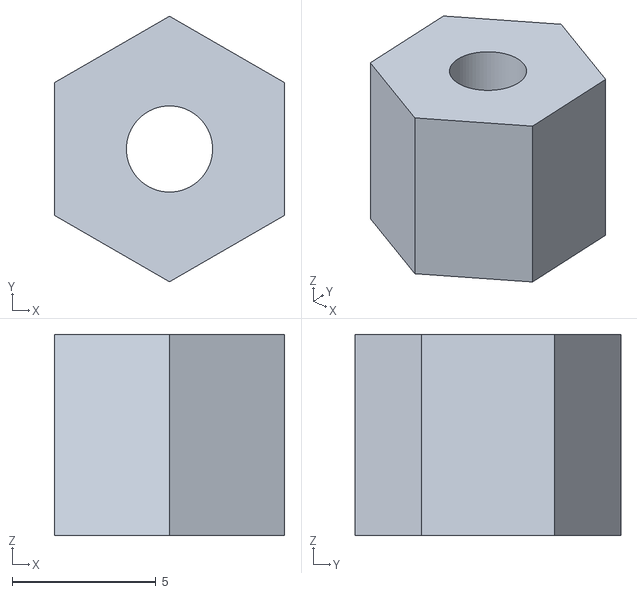
[picture p139: CAD file, 2023-07-28]
docs/Water/Electronics/SmartCitizen Water Kit/IP Box One Carrier/Components/SEP.stl
8.01 x 9.25 x 7.00
