fablabbcn/smartcitizen-enclosures/docs/Water/Electronics/SmartCitizen Water Station/Isolated Carriers Station/Components/3D printed/carrier_holder.stl

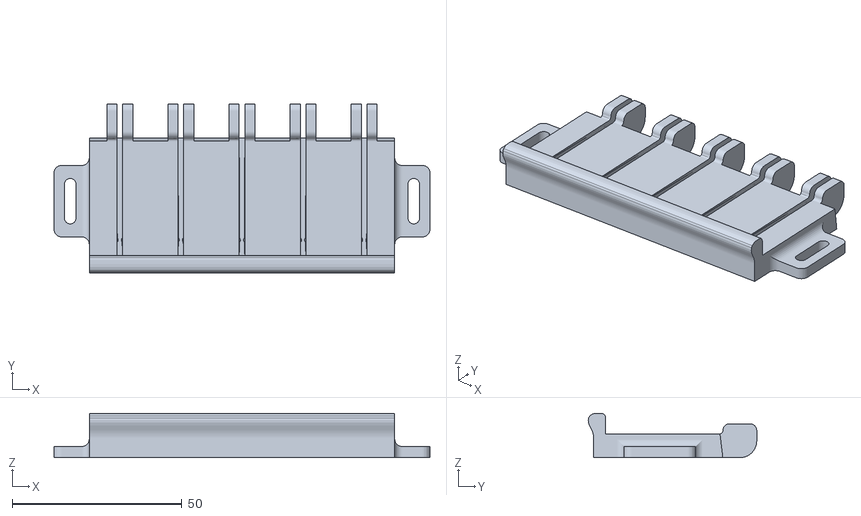
[picture p140: CAD file, 2023-10-23]
docs/Water/Electronics/SmartCitizen Water Station/Isolated Carriers Station/Components/3D printed/carrier_holder.stl
110.8 x 49.7 x 13.1
