fablabbcn/smartcitizen-enclosures/docs/Water/Electronics/SmartCitizen Water Station/Isolated Carriers Station/Components/Acrylics/ACRYLIC-BOTTOM.dxf

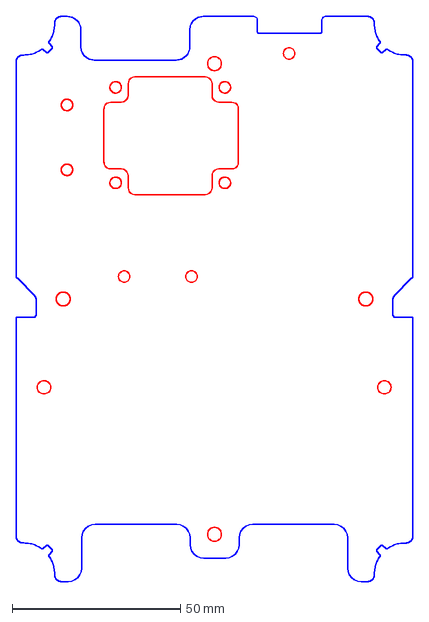
[picture p141: CAD file, 2023-10-23]
docs/Water/Electronics/SmartCitizen Water Station/Isolated Carriers Station/Components/Acrylics/ACRYLIC-BOTTOM.dxf
118.0 x 168.0 mm
