fablabbcn/smartcitizen-enclosures/docs/Water/Probe Holders/multiple/components/bend-support.stl

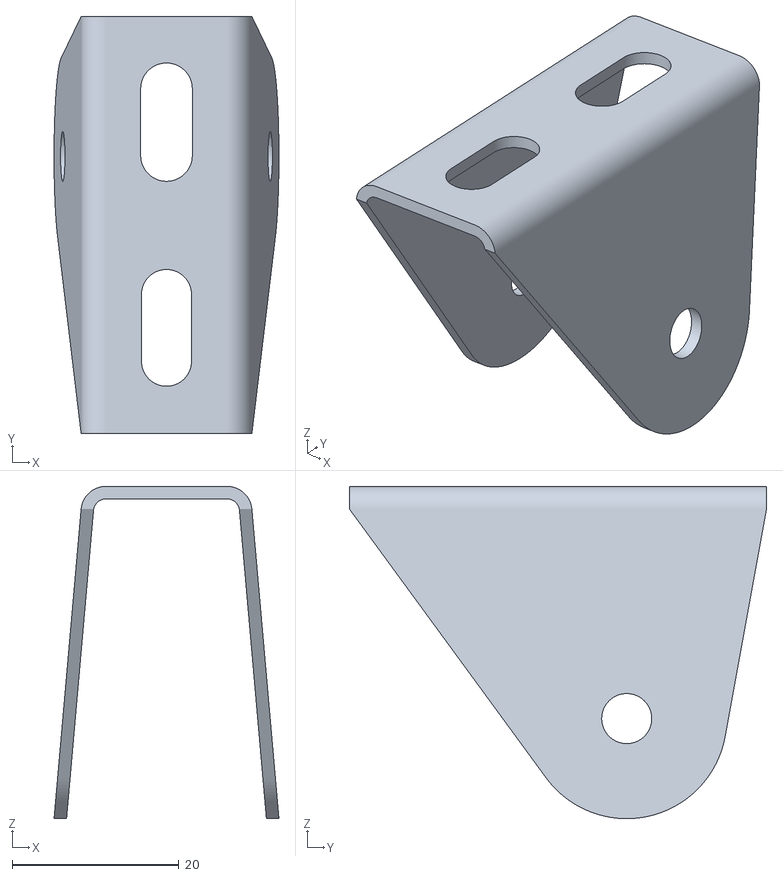
[picture p142: CAD file, 2024-05-03]
docs/Water/Probe Holders/multiple/components/bend-support.stl
27.0 x 50.0 x 39.8
