fablabbcn/smartcitizen-enclosures/docs/Water/Probe Holders/multiple/components/cable_protectors/cable-clip_SMA.stl

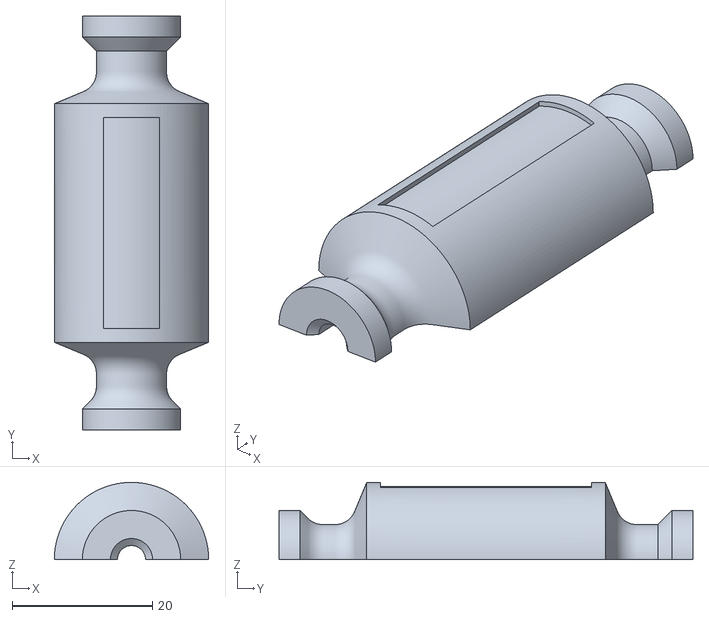
[picture p143: CAD file, 2023-09-17]
docs/Water/Probe Holders/multiple/components/cable_protectors/cable-clip_SMA.stl
22.0 x 59.0 x 11.0
