fablabbcn/smartcitizen-enclosures/docs/Water/Probe Holders/multiple/components/hook/hook-part1.stl

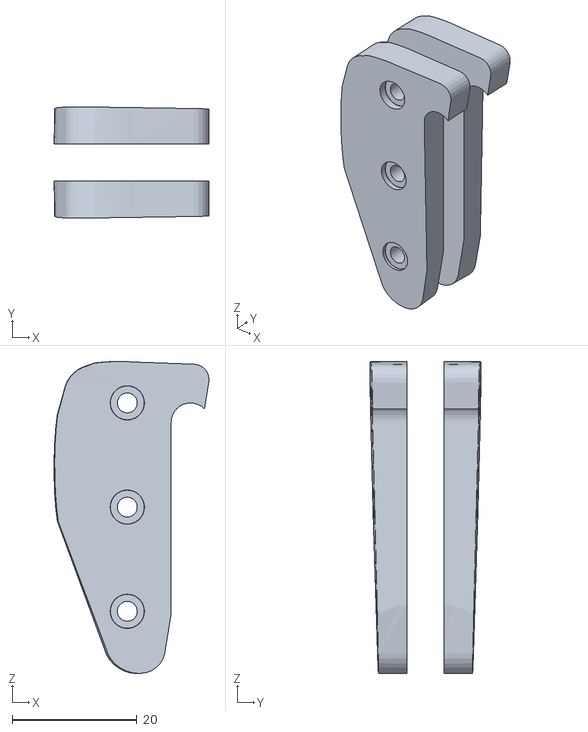
[picture p144: CAD file, 2024-03-19]
docs/Water/Probe Holders/multiple/components/hook/hook-part1.stl
24.9 x 17.9 x 50.1
