fablabbcn/smartcitizen-enclosures/docs/Water/Probe Holders/single/components/cap.stl

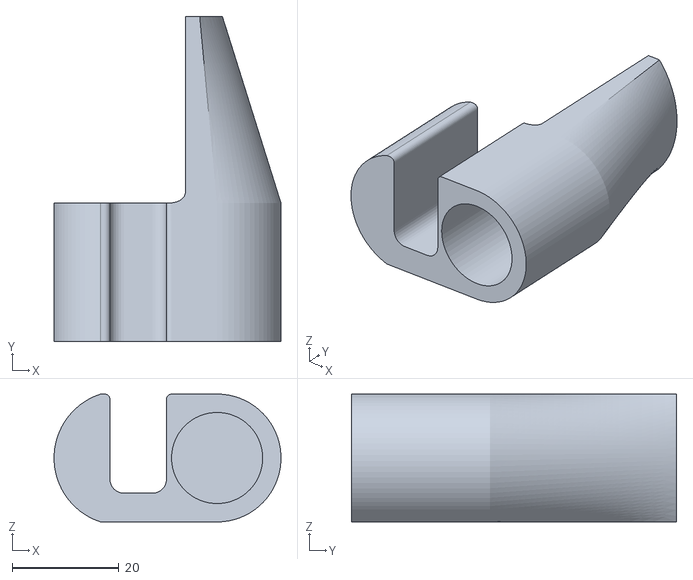
[picture p145: CAD file, 2022-11-16]
docs/Water/Probe Holders/single/components/cap.stl
42.6 x 61.0 x 24.0
