fablabbcn/smartcitizen-enclosures/SmartCitizen Air Enclosures/SCK2.1/SCK2.1 with PM Sensor/SCK2.1_PMS5003/3D Printed frog box v1/components/cover_04.stl

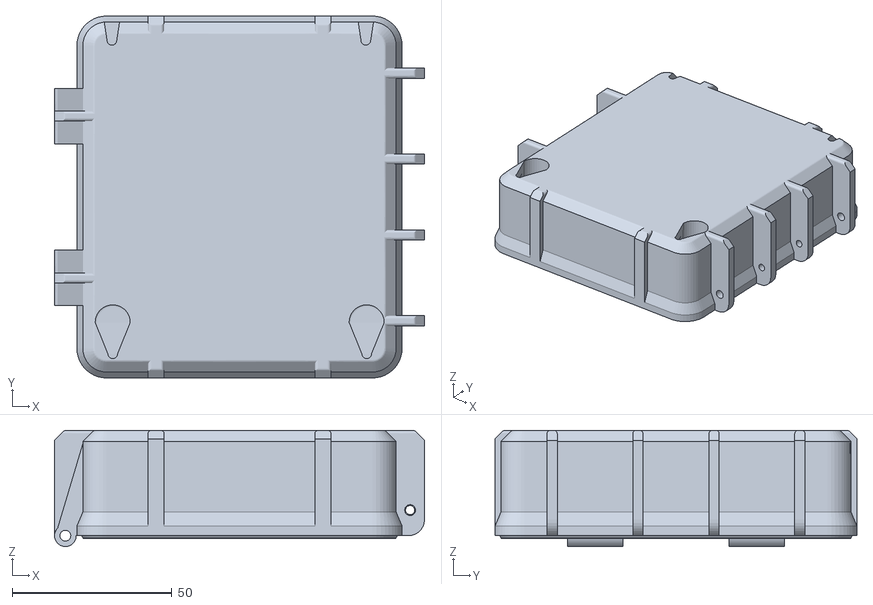
[picture p146: CAD file, 2024-03-19]
SmartCitizen Air Enclosures/SCK2.1/SCK2.1 with PM Sensor/SCK2.1_PMS5003/3D Printed frog box v1/components/cover_04.stl
115.7 x 113.2 x 36.3
