fablabbcn/smartcitizen-enclosures/SmartCitizen Water Enclosures/SmartCitizen Water Station/Tentacle Water Station/components/acrylic_top.dxf

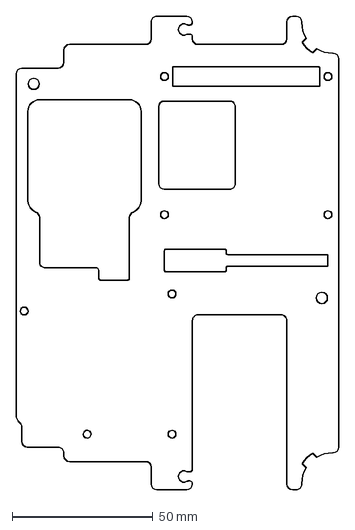
[picture p147: CAD file, 2022-07-07]
SmartCitizen Water Enclosures/SmartCitizen Water Station/Tentacle Water Station/components/acrylic_top.dxf
114.4 x 167.9 mm
