fablabbcn/smartcitizen-enclosures/docs/Air/misc/SCK2.1_BIKE_SADDLEBAG/components/exhaust-grid.stl

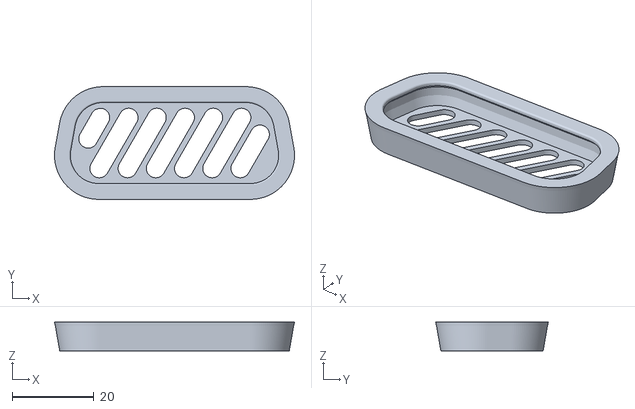
[picture p148: CAD file, 2020-11-11]
docs/Air/misc/SCK2.1_BIKE_SADDLEBAG/components/exhaust-grid.stl
58.7 x 27.6 x 7.00
