fablabbcn/smartcitizen-enclosures/docs/Air/SCK2.1/SCK2.1_2PMS5003_4EC_CO2/4-electrochemical-2pm-co2/components/holder-sht31.stl

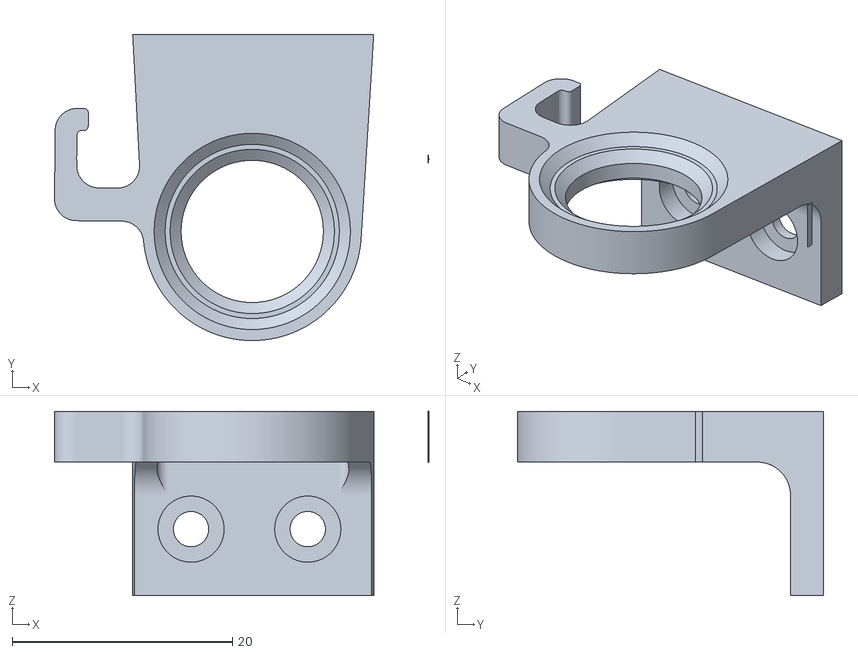
[picture p149: CAD file, 2023-02-09]
docs/Air/SCK2.1/SCK2.1_2PMS5003_4EC_CO2/4-electrochemical-2pm-co2/components/holder-sht31.stl
33.9 x 27.8 x 16.7
