fablabbcn/smartcitizen-enclosures/docs/Air/SCK2.1/SCK2.1_2PMS5003_6EC/6-electrochemical-spec-2pm/components/3DPRINTING/frame-spec.stl

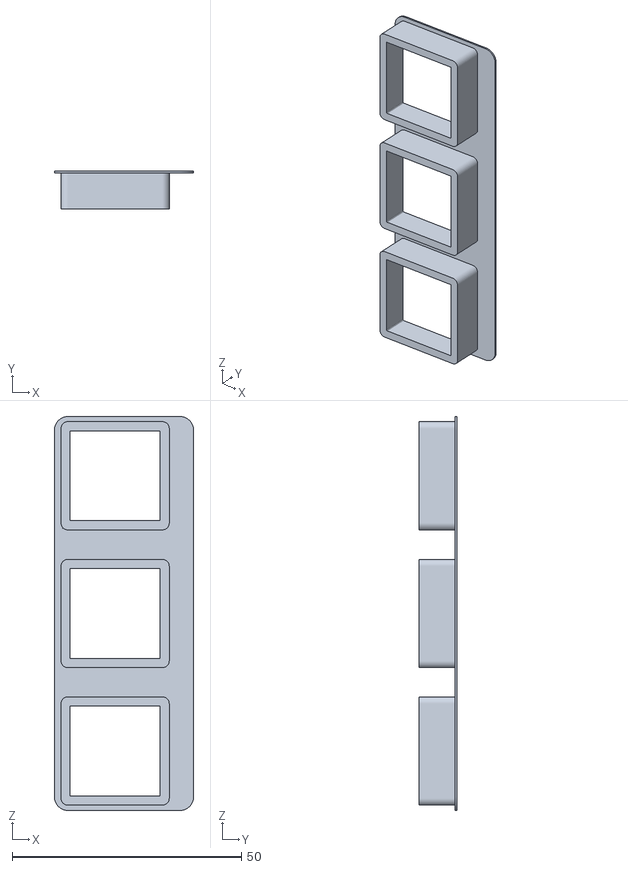
[picture p150: CAD file, 2023-01-04]
docs/Air/SCK2.1/SCK2.1_2PMS5003_6EC/6-electrochemical-spec-2pm/components/3DPRINTING/frame-spec.stl
30.4 x 8.20 x 86.0
