fablabbcn/smartcitizen-enclosures/docs/Air/SCK2.1/SCK2.1_PMS5003/3D Printed + HDPE/components/BASE_WO_SUPPORT.stl

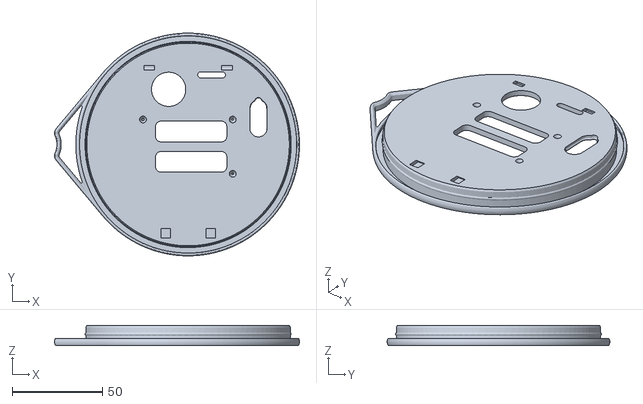
[picture p151: CAD file, 2019-09-09]
docs/Air/SCK2.1/SCK2.1_PMS5003/3D Printed + HDPE/components/BASE_WO_SUPPORT.stl
135.8 x 123.5 x 11.1
