fablabbcn/smartcitizen-enclosures/docs/Air/SCK2.1/SCK2.1_PMS5003/3D Printed frog box/components/base.stl

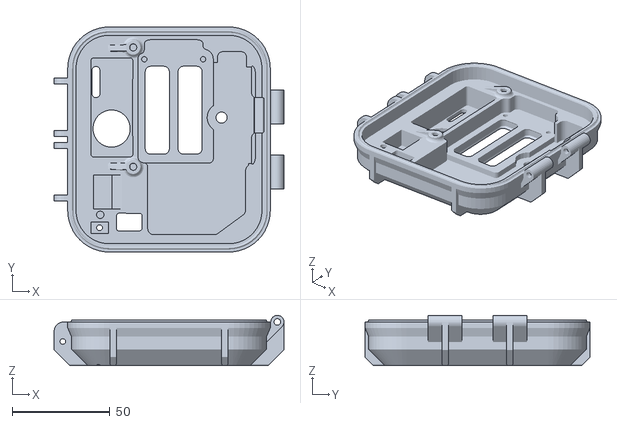
[picture p152: CAD file, 2024-09-17]
docs/Air/SCK2.1/SCK2.1_PMS5003/3D Printed frog box/components/base.stl
117.7 x 115.2 x 25.8
