fablabbcn/smartcitizen-enclosures/docs/Air/SCK2.1/SCK2.1_PMS5003/3D Printed Modular Viadukaduk/components/sck2.1_enclosure_vdk_1.0_middle.stl

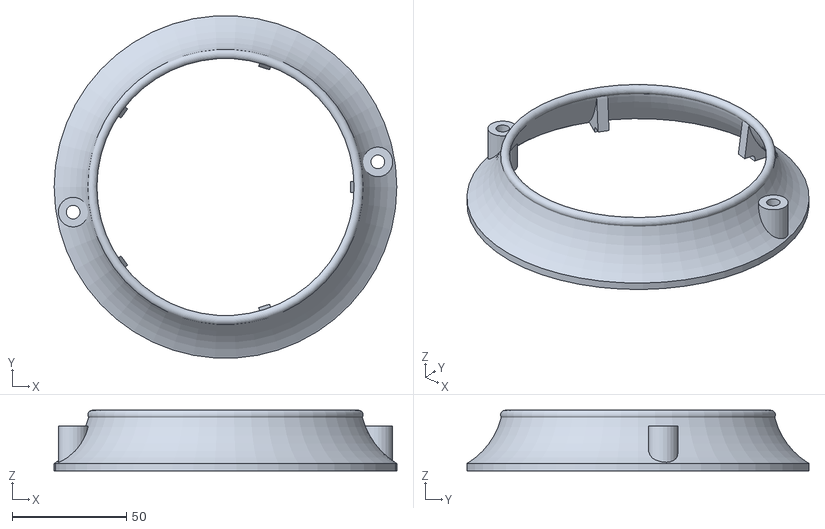
[picture p153: CAD file, 2021-02-11]
docs/Air/SCK2.1/SCK2.1_PMS5003/3D Printed Modular Viadukaduk/components/sck2.1_enclosure_vdk_1.0_middle.stl
150.0 x 149.7 x 26.5
