fablabbcn/smartcitizen-enclosures/docs/Air/SCK2.1/SCK2.1_PMS5003/3D Printed Prototype/components/COVER.step

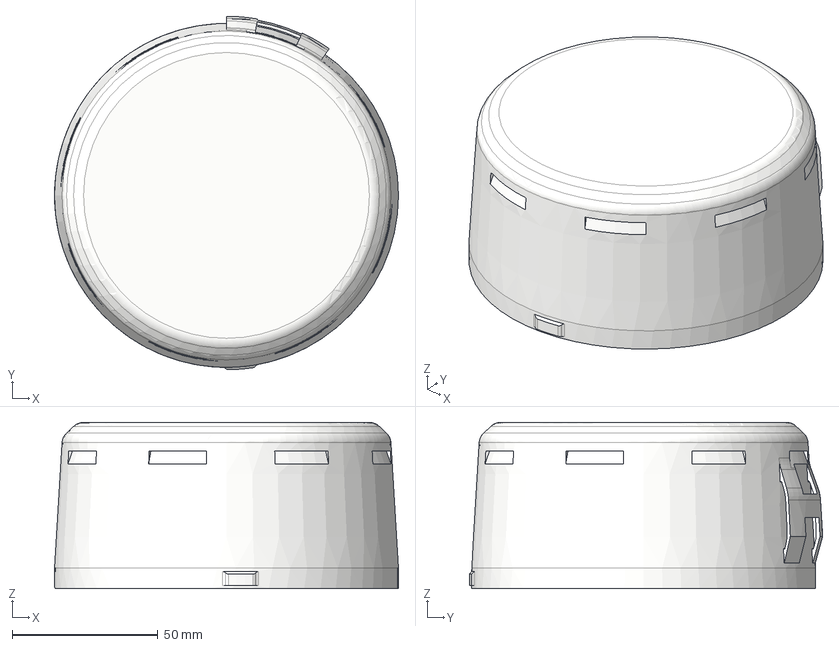
[picture p154: CAD file, 2020-04-24]
docs/Air/SCK2.1/SCK2.1_PMS5003/3D Printed Prototype/components/COVER.step
118.0 x 121.2 x 57.0 mm
