fablabbcn/smartcitizen-enclosures/docs/Air/SCK2.2/SCK2.2_SEN5X + 2EC/3D printed frog box/README.md

---
card: true
type: unit
name: SCK2.2 + 2x Alphasense (A-series)
page_type: enclosure
version: SCK2.2
field:
  - air
grade: intermediate
feature_img: /assets/images/2.2/SCKit_22_2EC.png
excerpt: SCK2.2 with two Alphasense sensors (A-series).
---

# {{ name }}

RENDER

{{ excerpt }}

This enclosure is to be used with the {{version}}. It's based on the [Frog Box design](https://www.thingiverse.com/thing:4582978), with additional modifications, remade from scratch in [Blender]([url](https://www.blender.org/)).

⚠️ WARNING: There are various covers that can be used with this enclosure. The cover_INDOOR.stl is meant to be used in indoor spaces. The cover_FREESTYLE.stl is

To use it, you need to print:

- 1x cover of your choice: [indoor version](components/cover_indoor.stl), [freestyle version](components/cover_multipurpose.stl). The [outdoor version](components/cover_outdoor.stl) is currently a WIP only, and it's meant to be used with a protective umbrella.
- 1x [base](components/base.stl)
- 1x [clip](components/clip-sck2.X-sen5X.stl)
- 2x [latches](components/latch-hinge-frog-box.stl)
- 1x [afe support](components/afe_support.stl)
- 1x [asb breidge](components/asb_bridge.stl)

## Printing

We have tested this on a Prusa MK3 3D printer, using PLA and the following settings:

- No supports
- 0.2mm layer height
- At least 3 vertical walls
<!--- We recommend to avoid using gyroid as an infill-->

See the slicer capture below:

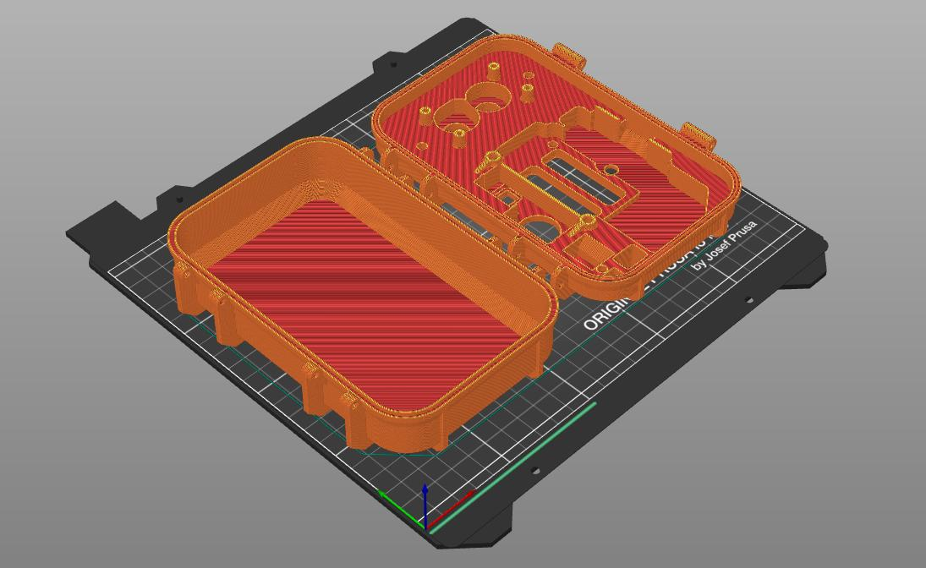
[picture p157: docs/assets/images/2.2/slicer_SCKit_2EC.jpg]
**SLICER**


## Additional components

- 5x M3 Inserts
- 6x M3x30mm INOX screws
- 2x M3x20mm screws
- 3x M3x6mm screw
- One external [SC reset button](https://github.com/fablabbcn/smartcitizen-enclosures/tree/master/SmartCitizen%20Power%20Options/Reset%20button)
- Rubber seal 2.5mm
