fablabbcn/smartcitizen-enclosures/docs/Air/SCK2.2/SCK2.2_SEN5X + EC B-Series/3D printed frog box/README.md

---
card: true
type: unit
name: SCK2.2 + Alphasense (B-Series)
page_type: enclosure
version: SCK2.2
field:
  - air
grade: advanced
feature_img: /assets/images/2.2/SCKit_EC_B-Series.jpg
excerpt: SCK2.2 with an Alphasense B-series sensor.
---

# {{ name }}

RENDER

{{ excerpt }}

- 1x cover of your choice: [indoor version](components/cover_indoor.stl), [multiporpuse version](components/cover_multipurpose.stl).
- 1x [base](components/base.stl)
- 1x [clip](components/clip-sck2.X-sen5X.stl)
- 2x [latches](components/latch-hinge-frog-box.stl)
