fablabbcn/smartcitizen-enclosures/docs/Air/SCK2.3/SCK2.3_SEN5X + EC B-Series/3D_printed_frog_box/README.md

---
card: true
type: unit
name: SCK2.2 + Alphasense (B-Series)
page_type: enclosure
version: SCK2.3
field:
  - air
grade: intermediate
feature_img: /assets/images/2.3/SCKit_23_ECB.png
excerpt: SCK2.3 with an Alphasense B-series sensor.
---

# {{ name }}

RENDER

{{ excerpt }}

This enclosure is to be used with the {{version}}. It's based on the [Frog Box design](https://www.thingiverse.com/thing:4582978), with additional modifications, remade from scratch in [Blender](https://www.blender.org/).

!!! warning "Various cover designs"
	There are various covers that can be used with this enclosure:
	    - [`cover_indoor.stl`](components/cover_indoor.stl) is meant to be used in indoor spaces.
		- [`cover_freestyle.stl`](components/cover_multipurpose.stl) is meant to be used with zipties, or hung on a wall but for short-term deployments.
		- [`cover_outdoor.stl`](components/cover_outdoor.stl) is meant to be used with an [umbrella](/Air/shared/umbrella/), for long-term outdoor deployments.

To use it, you need to print:

- 1x cover of your choice: [indoor version](components/cover_indoor.stl), [freestyle version](components/cover_multipurpose.stl) or the [outdoor version](components/cover_outdoor.stl).
- 1x [base](components/base_SCKit.stl)
- 1x [clip](components/clip-sck2.X-sen5X.stl)
- 2x [latches](components/latch-hinge-frog-box.stl)

## Printing

We have tested this on a Prusa MK3 3D printer, using PLA and the following settings:

- No supports
- 0.2mm layer height
- At least 3 vertical walls
<!--- We recommend to avoid using gyroid as an infill-->

See the slicer capture below:
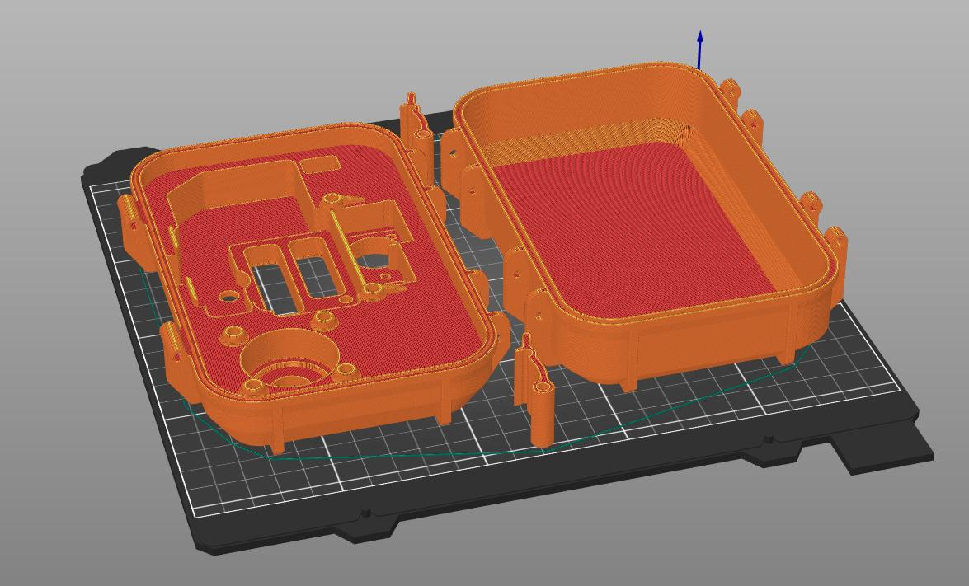
[picture p164: docs/assets/images/2.3/slicerSCKit_23_ECB.jpg]
**SLICER**


## Additional components

- 6x M3 Inserts
- 6x M3x30mm INOX screws
- 2x M3x10mm screws
- 4x M3x6mm screws
- Rubber seal 2.5mm
- Umbrella (for outdoor settings)

!!! danger "Not outdoor by itself"
	For deployments outdoors, you will need to use the protective [umbrella](/Air/shared/umbrella/) to make sure it doesn't get soaked! The umbrella can be substituted by a physical cover, for instance placing the device protected under a balcony.
