fablabbcn/smartcitizen-enclosures/docs/Air/SCK2.1/SCK2.1_PMS5003/SCK_3Dprint_Assembly_GER_EN_USTTG_IIGS_2023/README.md

# Smart Citizen Enclosures description - CoKLIMAx project

The following folder includes the 3D print files for the enclosures developed for the Smart Citizen Kit Sensor Hardware and Stations (Versions 1.5, 2.0 and 2.1) families, designed for 3D printing and another rapid prototyping method. See also Smart Citizen Cases reference below.

The development of the enclosure was done by the Institute of Engineering Geodesy (IIGS) https://www.iigs.uni-stuttgart.de/, supported by the Institute of Navigation (INS) https://www.ins.uni-stuttgart.de/ at the University of Stuttgart as part of the CoKLIMAx project, which is funded under the funding guideline "Development and Implementation Preparation of Copernicus Services for Public Needs on Climate Adaptation Strategies for Municipal Applications in Germany" of the German Federal Ministry of Digital Affairs and Transport (BMDV). 

CoKLIMAx project https://coklimax.net/ and https://maps.coklimax.net/portal/apps/sites/#/coklimax

```
Funding code: 50EW2103A-D 
Project duration: 11.2021 - 06.2024 
All the authors acknowledge the funding received via BMDV for the CoKLIMAx project.
```

## Additional sources

Guillem Camprodon, Óscar González, Víctor Barberán, Máximo Pérez, Viktor Smári, Miguel Ángel de Heras, Alejandro Bizzotto, Smart Citizen Kit and Station: An open environmental monitoring system for citizen participation and scientific experimentation, HardwareX, Volume 6, 2019, e00070, ISSN 2468-0672,
https://doi.org/10.1016/j.ohx.2019.e00070, https://www.sciencedirect.com/science/article/pii/S2468067219300203#b0195
Smart Citizen Enclosures https://data.mendeley.com/datasets/r9bfyxdfw4/1
