fablabbcn/smartcitizen-enclosures/docs/Air/SCK2.1/SCK2.1_PMS5003_2EC_CO2/3D Printed Square/README.md

Use clip and bridge from [SCK2.1_PMS5003_2EC/3D Printed version](/SmartCitizen Outdoor Cases V2.X/SCK2.1_PMS5003_2EC/3D Printed version).
