fablabbcn/smartcitizen-enclosures/docs/Air/SCK2.1/SCK2.1_PMS5003_2EC/3D Printed/README.md

The ASB is held by a bridge behind the SCK, use the [bridge](components/bridge-asb.stl) for this purpose.
