fablabbcn/smartcitizen-enclosures/docs/Air/SCK2.1/SCK2.1_PMS5003/3D Printed Modular Viadukaduk/README.md

# 3D printed Modular Viadukaduk

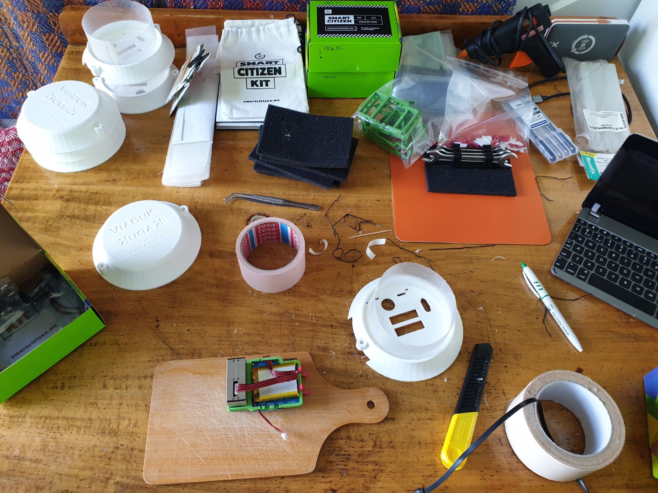
[picture p176: docs/Air/SCK2.1/SCK2.1_PMS5003/3D Printed Modular Viadukaduk/pictures/20200601_133633.jpg]


We decided to make our own enclosure to make sure we had the best results addressing potential issues like:

- condensation of vapour - good ventillation
- overheating from sun
- good enough waterproofing
- easy to hang on a facade at the height of about 4 meters
- good access to sensors

As of January 2021 there are 12 sensors with this enclosure, which have been active for over half a year. See sensors with hashtag #viadukaduk.

As for the enclosures they are a success so far. They’ve been in the weather since april and withstood all sorts of conditions including storms and -10°. Some small amount of dust accumulates in the enclosure over time.

Moreover the design seems to prevent any overheating from the sun. The sensors are hanging in all orientations towards the north and all the readings of temperature seem to be consistent.

For UV durability we printed the outside enclosure in white PETG and installed them like this without further adjustments. Well, some stanley knife trimming was necessary due to 3d print quality. Internal parts (standard frame and clip) have been printed in ABS. We used commercial services of 3Dhubs for this.

The internal parts proven to be strong enough but could be better. The openings in the enclosure provided for the clip and frame could be better too - but you can print this right away and solve any problems with a stanley knife...

Inside of the enclosure there is a synthetic mesh, with small holes. Our meshes are not UV resistant but given they are postioned out of direct UV exposure we didn't have any problems with sun related damage. If you can find one which can resist UV better, use that one instead.
The role of the mesh is to stop any big droplets of water which could still penetrate under the hood at strong wind conditions. There are some holes around the base of the mesh for drainage. The mesh also keeps insects away. It is glued with hot glue pistol to the bottom part of the enclosure. We ordered those laser cut to size in a company in Haarlem, Netherlands.

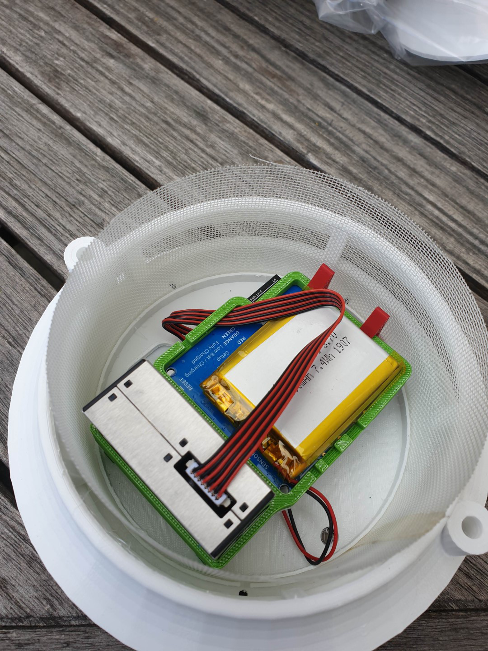
[picture p177: docs/Air/SCK2.1/SCK2.1_PMS5003/3D Printed Modular Viadukaduk/pictures/20200512_170249.jpg]


The dimensions of the meshes are 335x58mm.

The enclosure is modular. So you can add the “middle” element multiple times. This would influence the width of the meshes, however. The mesh fits in groves provided in the enclosure. The mesh company is http://www.topzeven.com/ You will notice that the grips between the main 3 rings of the enclosure on the 1.0 version are different and much simplier and durable then illustrated.

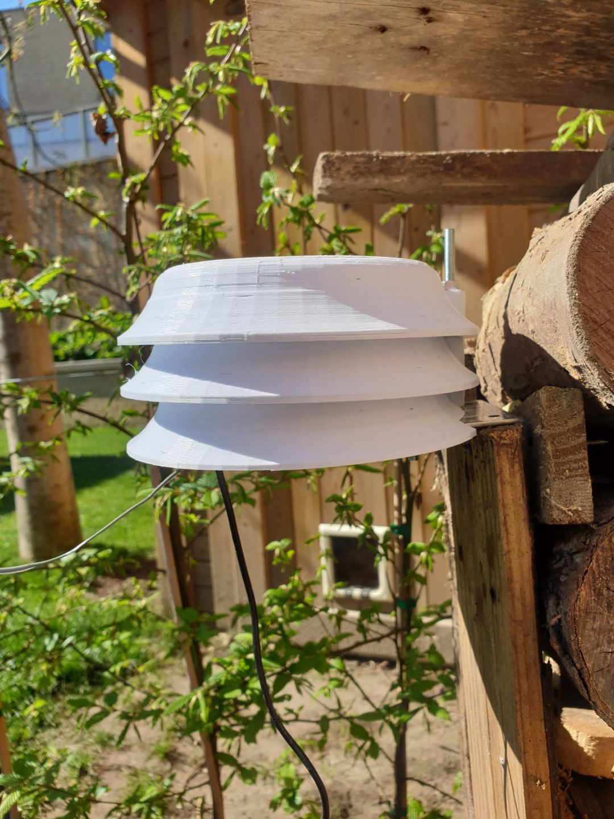
[picture p178: docs/Air/SCK2.1/SCK2.1_PMS5003/3D Printed Modular Viadukaduk/pictures/20200411_113658.jpg]


The included section depicts an older version of the enclosure where there also were two grove ridges at the TOP part. Since then the 1.0 has higher ridges and the TOP part has only one, which goes INSIDE the mesh. After a minute of patient manipulation your enclosrure will fit together neatly. Also glueing the mesh to the BOTTOM part helps to maneuver.

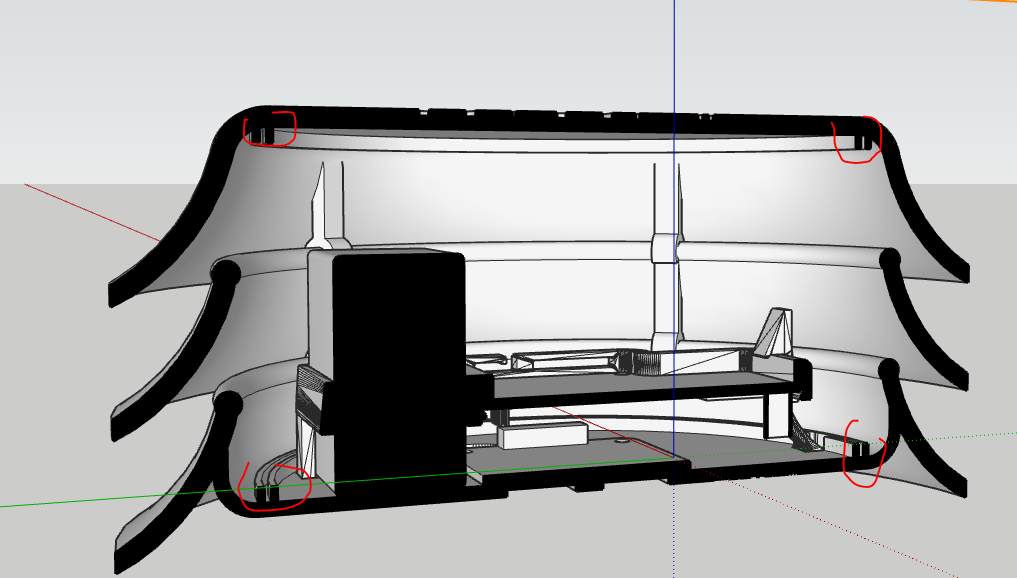
[picture p179: docs/Air/SCK2.1/SCK2.1_PMS5003/3D Printed Modular Viadukaduk/pictures/section_0.2.png]


There are 3 ports for screws on the enclosure. 2 of them are located on the perimeter of the enclosure. These are used with 9cm (I think 9cm...) long, 6mm inox screws to shut the enclosure.

A recess for a 90° square bracket is present to one side of the BOTTOM part. One of the perimeter screws and a separate screw port, the 3rd port, from within the enclosure is used to fix the enclosure to the bracket. Given that you probably will have a different bracket than we did, you might need to adjust the position of the 3rd port in the sketchup file before you print.
