fablabbcn/smartcitizen-enclosures/docs/Air/SCK2.1/SCK2.1_PMS5003/3D Printed Modular Viadukaduk/pictures/20200504_203755.jpg

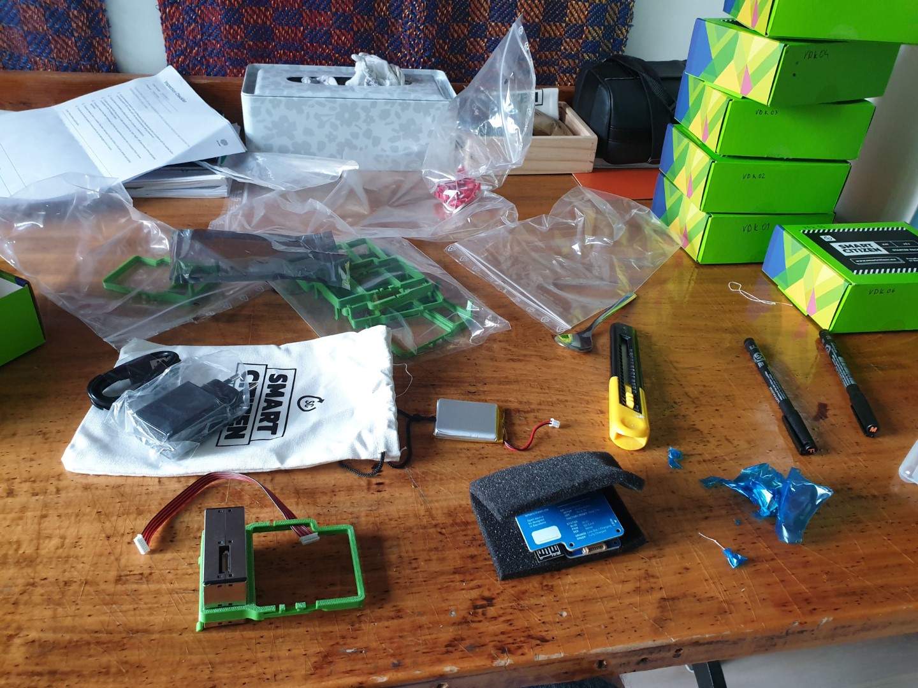
docs/Air/SCK2.1/SCK2.1_PMS5003/3D Printed Modular Viadukaduk/pictures/20200504_203755.jpg
