fablabbcn/smartcitizen-enclosures/docs/Air/SCK2.1/SCK2.1_PMS5003/3D Printed Prototype/Case25.png

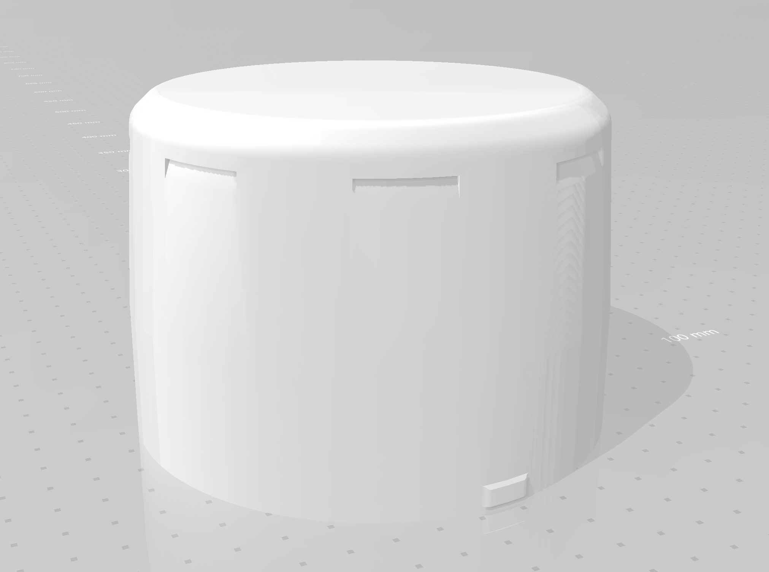
docs/Air/SCK2.1/SCK2.1_PMS5003/3D Printed Prototype/Case25.png
