fablabbcn/smartcitizen-enclosures/docs/Air/SCK2.1/SCK2.1_PMS5003/3D Printed SCK2.1 IaaC Style/From below.JPG

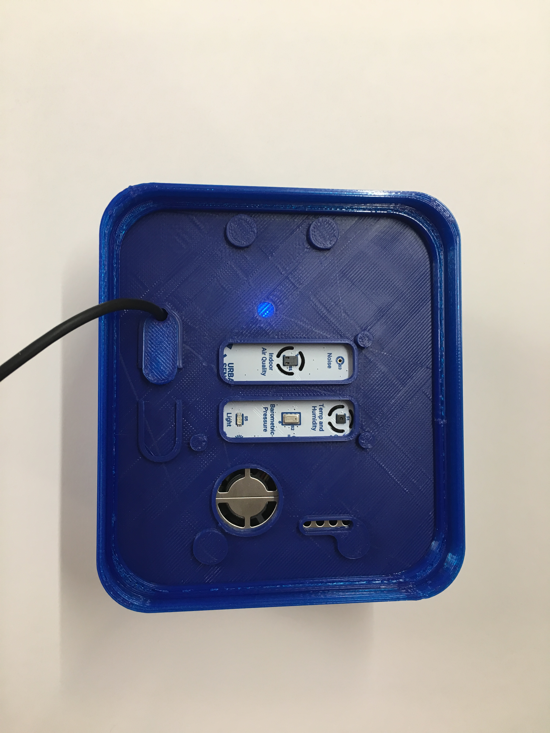
docs/Air/SCK2.1/SCK2.1_PMS5003/3D Printed SCK2.1 IaaC Style/From below.JPG
