fablabbcn/smartcitizen-enclosures/docs/Air/SCK2.1/SCK2.1_2PMS5003_4EC/4-electrochemical-alphasense-2pm/scas-4em-2pm-t-drawing-exploded-view.pdf

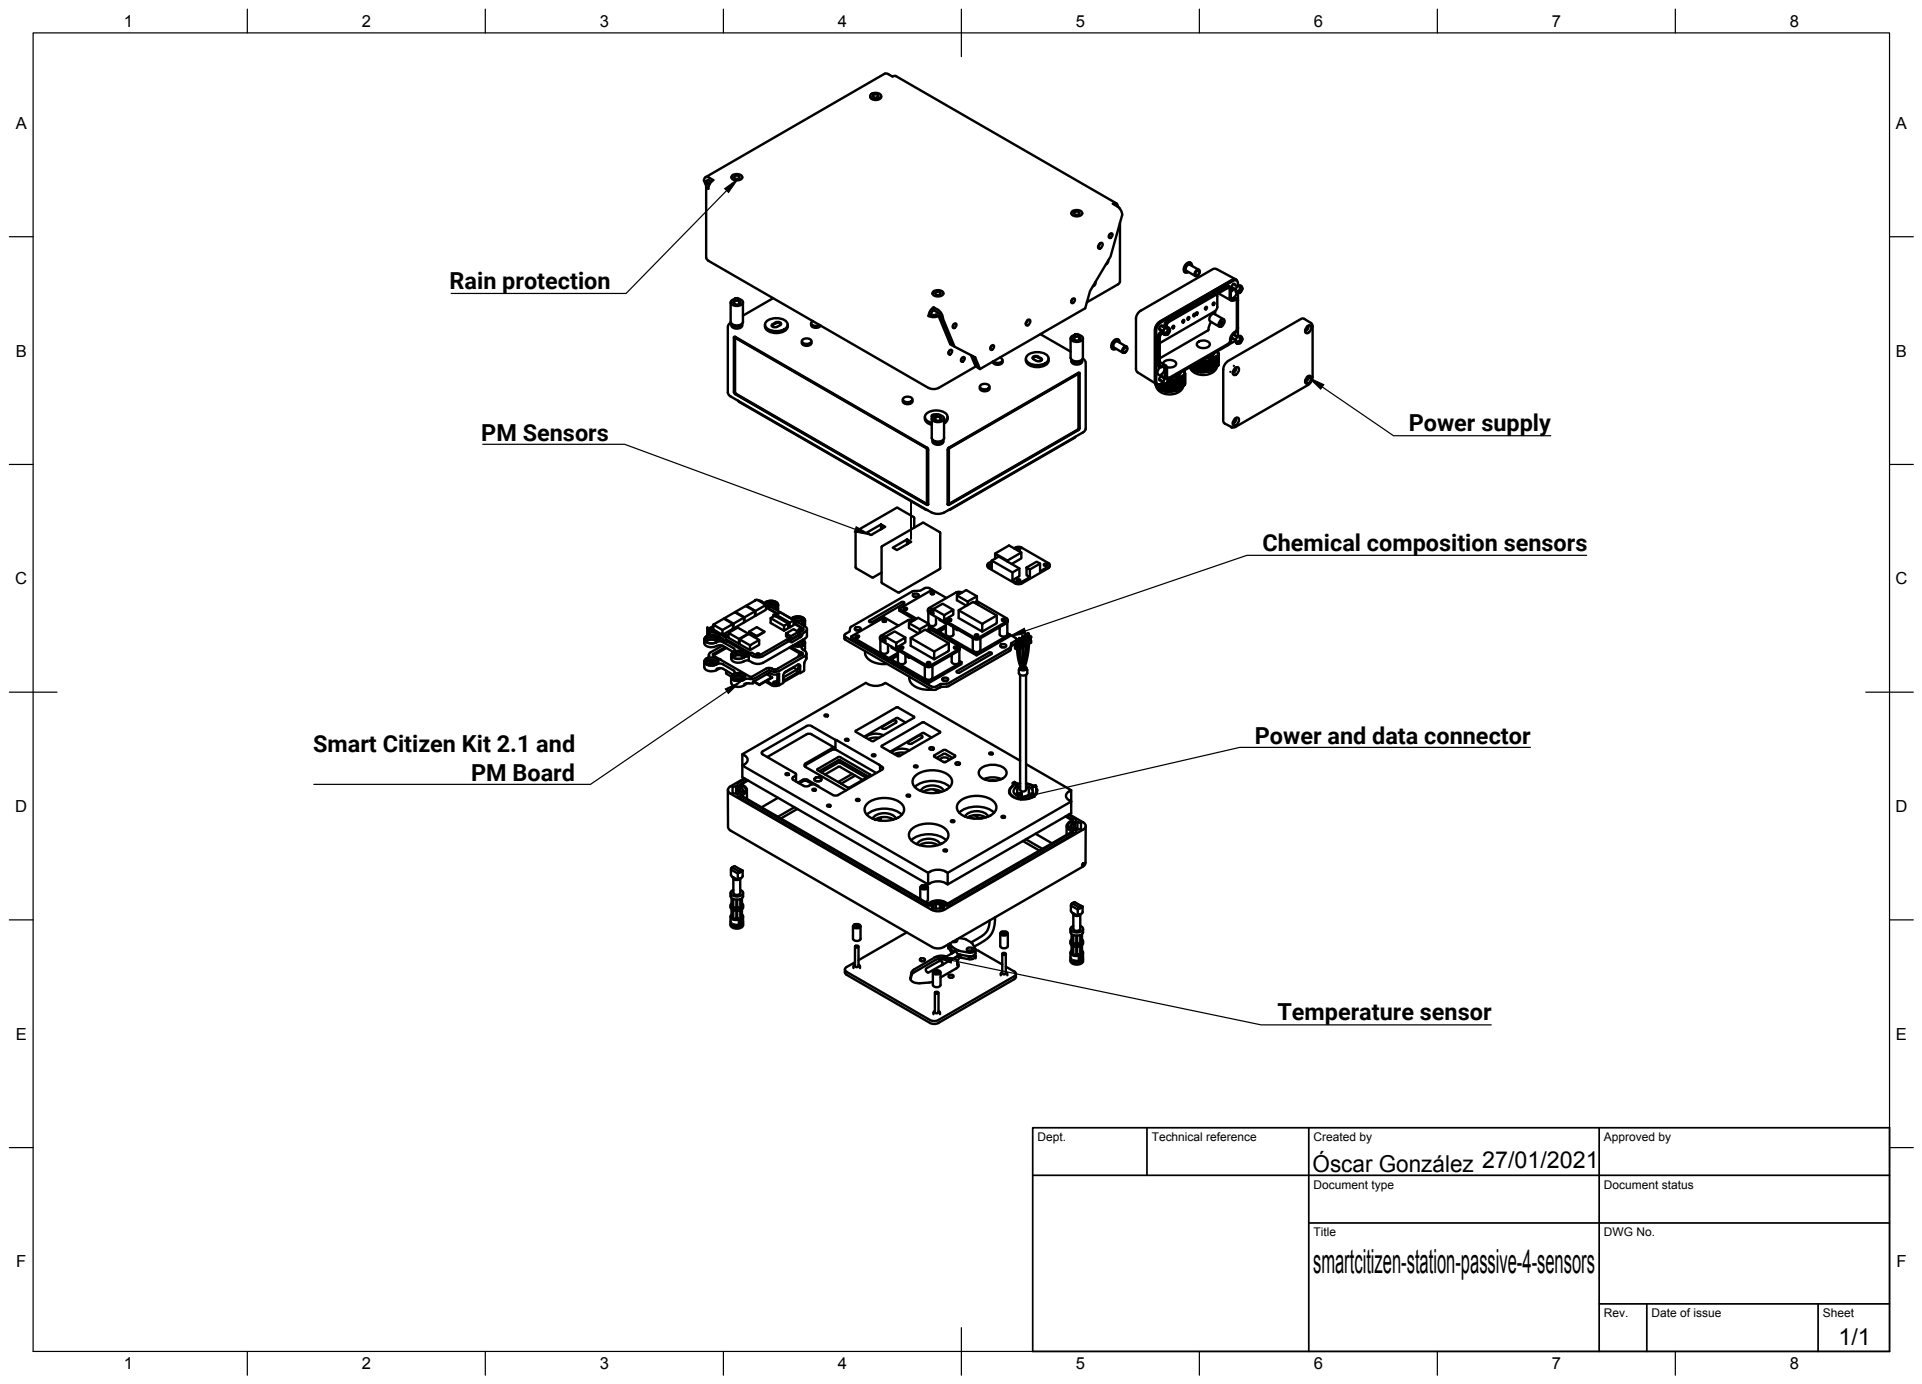
[picture p227: page 1]
Title; DWG No.; Rev.; Date of issue; Sheet; Rain protection; PM Board; Temperature sensor

Power supply PM Sensors

Chemical composition sensors

Power and data connector

Smart Citizen Kit 2.1 and

Dept. | Technical reference | Created by Óscar González 27/01/2021 | Approved by

Document type | Document status

smartcitizen-station-passive-4-sensors
