fablabbcn/smartcitizen-enclosures/docs/Air/SCK2.1/SCK2.1_2PMS5003_4EC/4-electrochemical-alphasense-2pm/scas-4em-2pm-t-drawing.pdf

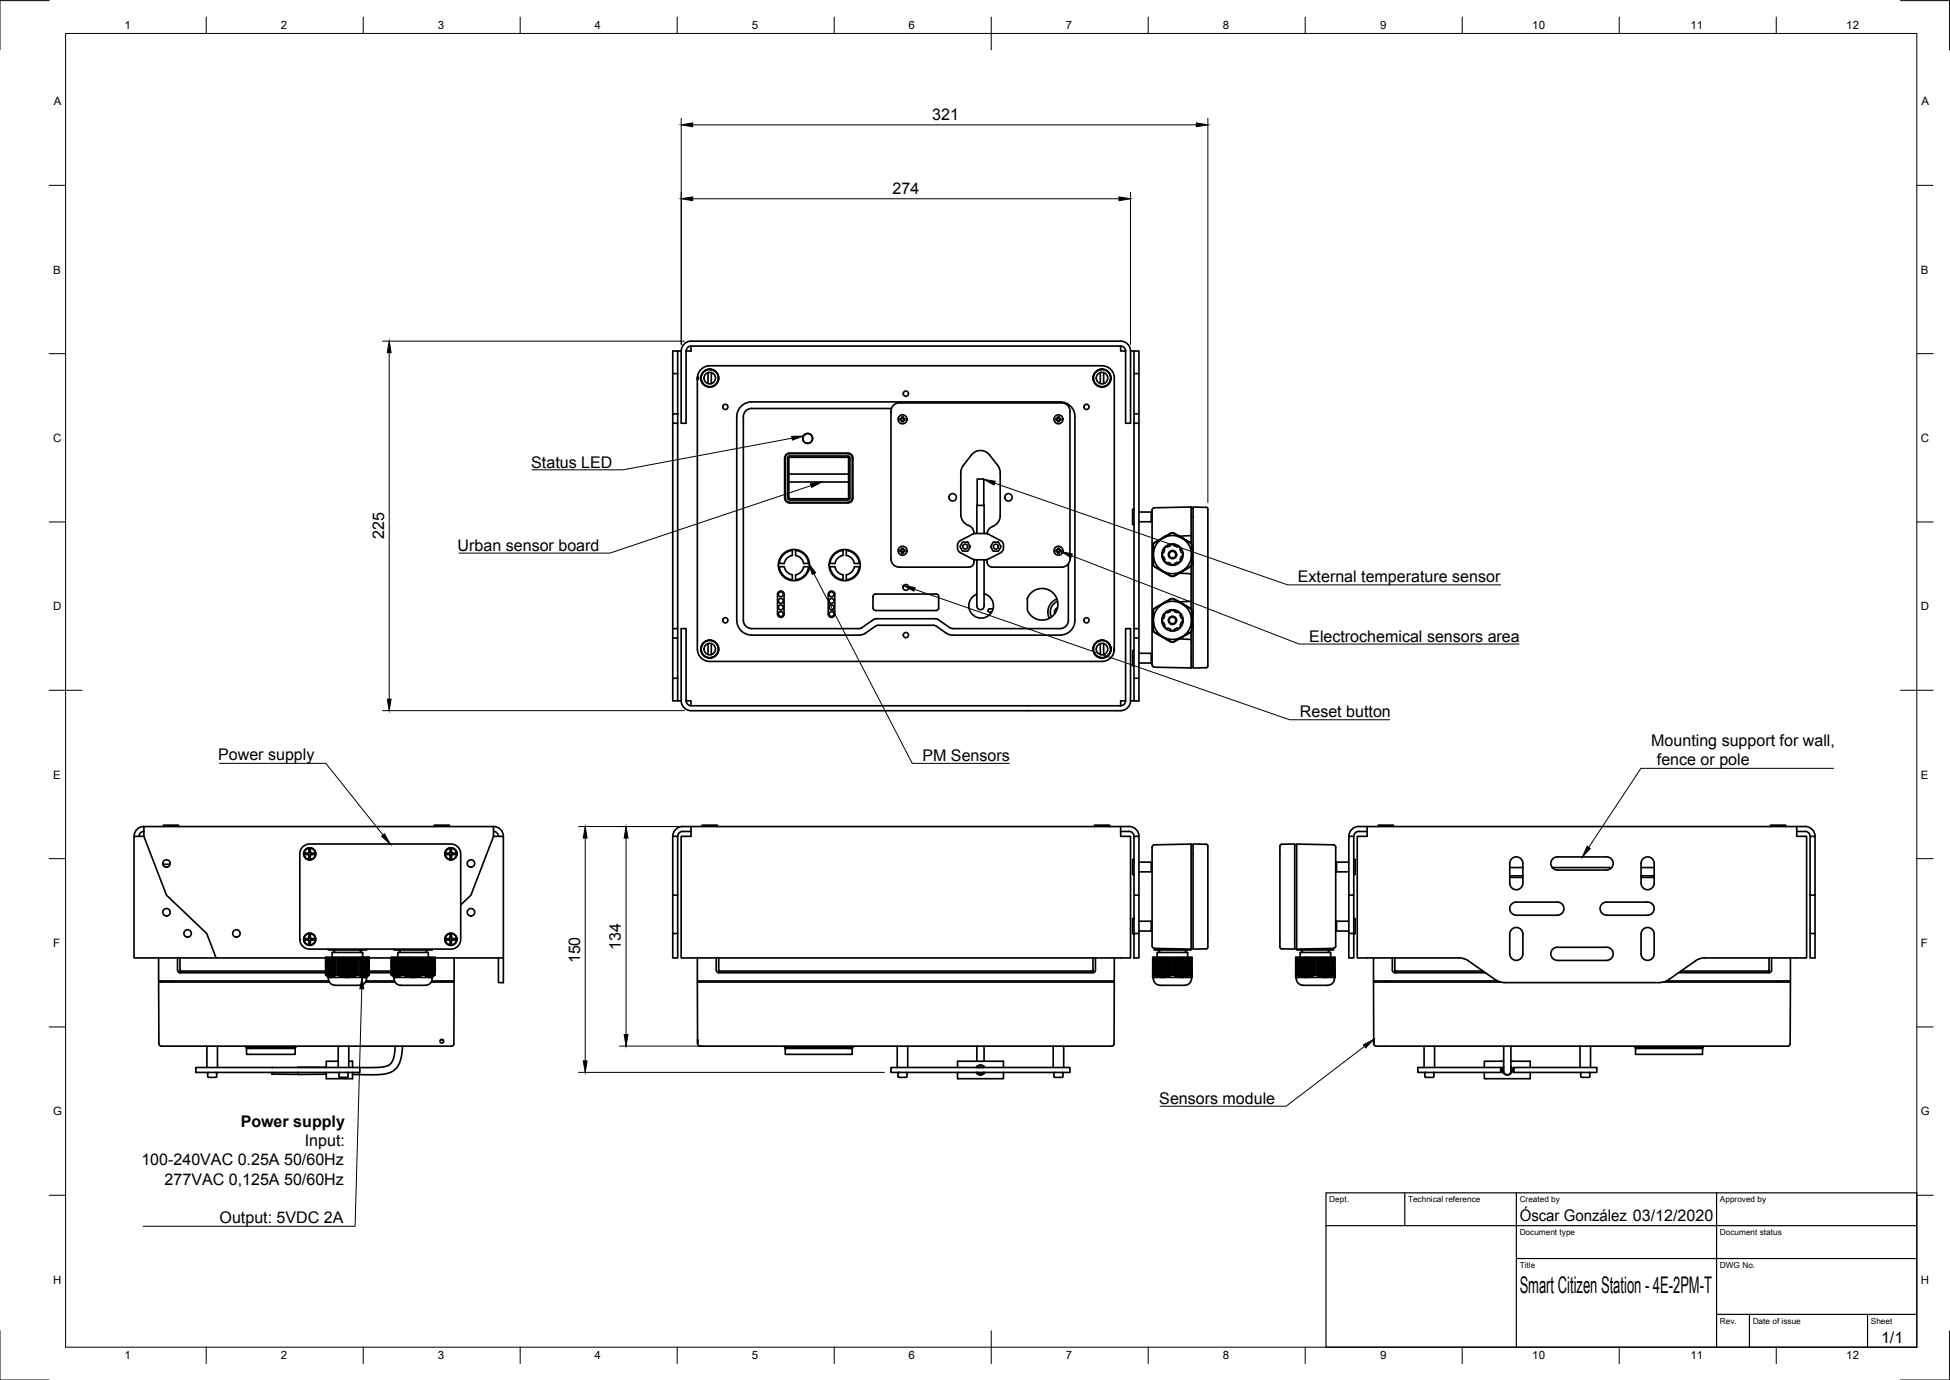
[picture p228: page 1]
Óscar González 225; Mounting support for wall, Power supply; fence or pole; Reset button; PM Sensors; Status LED; Power supply; 100-240VAC 0.25A 50/60Hz 277VAC 0,125A 50/60Hz; Output: 5VDC 2A; Sensors module

Urban sensor board

External temperature sensor

Electrochemical sensors area

Dept. | Technical reference | Created by 03/12/2020 | Approved by

Document type | Document status

Title Smart Citizen Station - 4E-2PM-T | DWG No.

Rev. | Date of issue | Sheet 1/1
