fablabbcn/smartcitizen-enclosures/docs/Air/SCK2.1/SCK2.1_PMS5003/CNC HDPE circle/overall_drawing.pdf

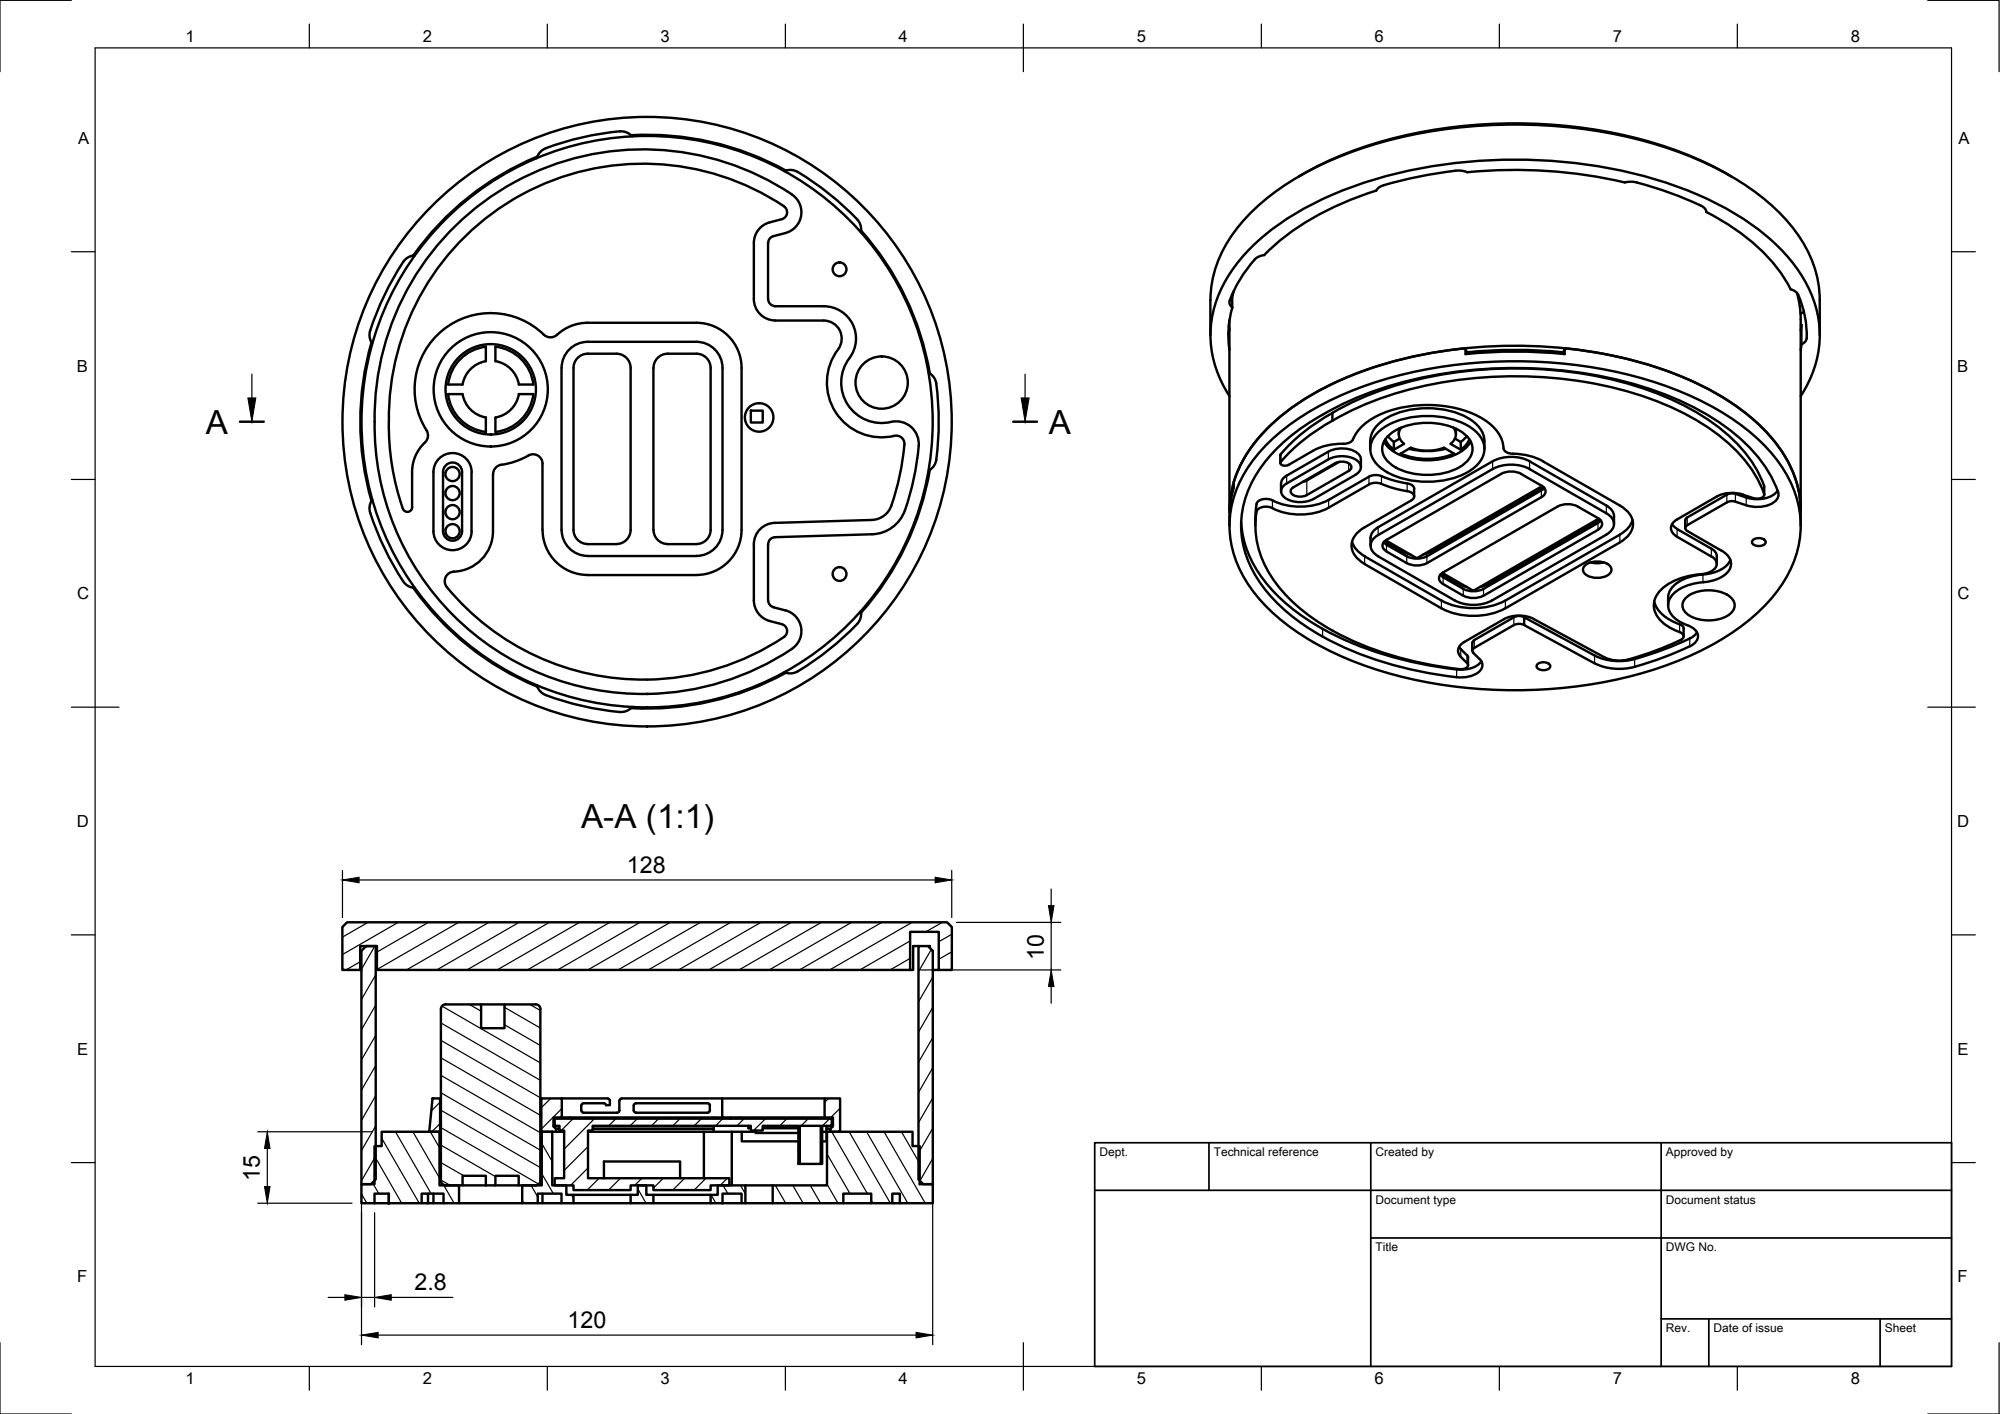
[picture p229: page 1]

Dept. | Technical reference | Created by | Approved by

Document type | Document status

Title | DWG No.

Rev. | Date of issue | Sheet

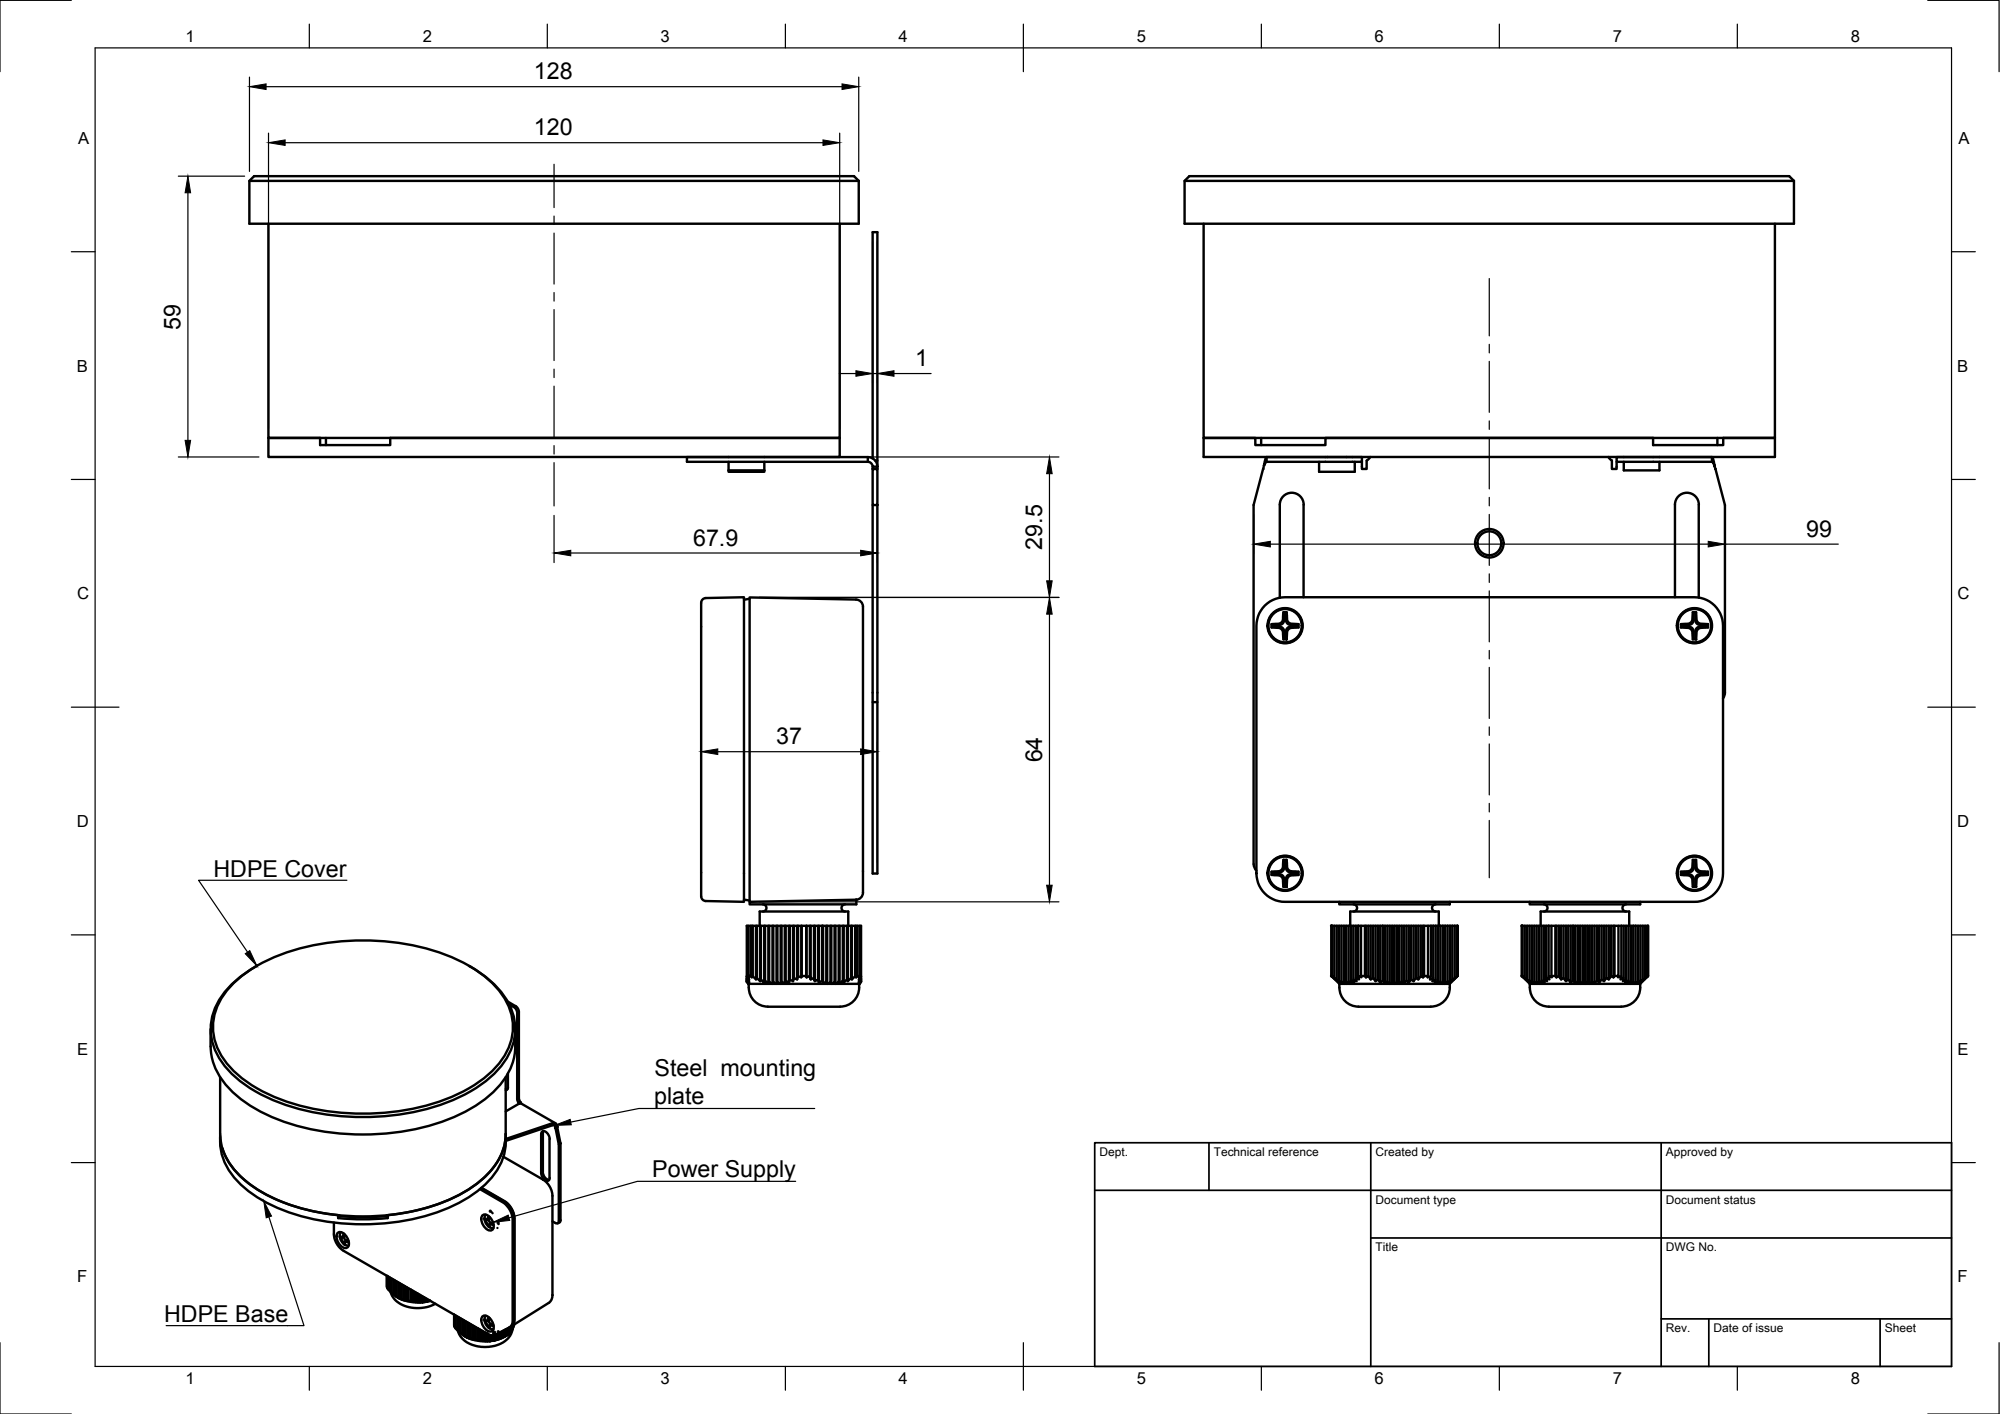
[picture p230: page 2]
Power Supply; Steel mounting; HDPE Cover; HDPE Base

Dept. | Technical reference | Created by | Approved by

Document type | Document status

Title | DWG No.

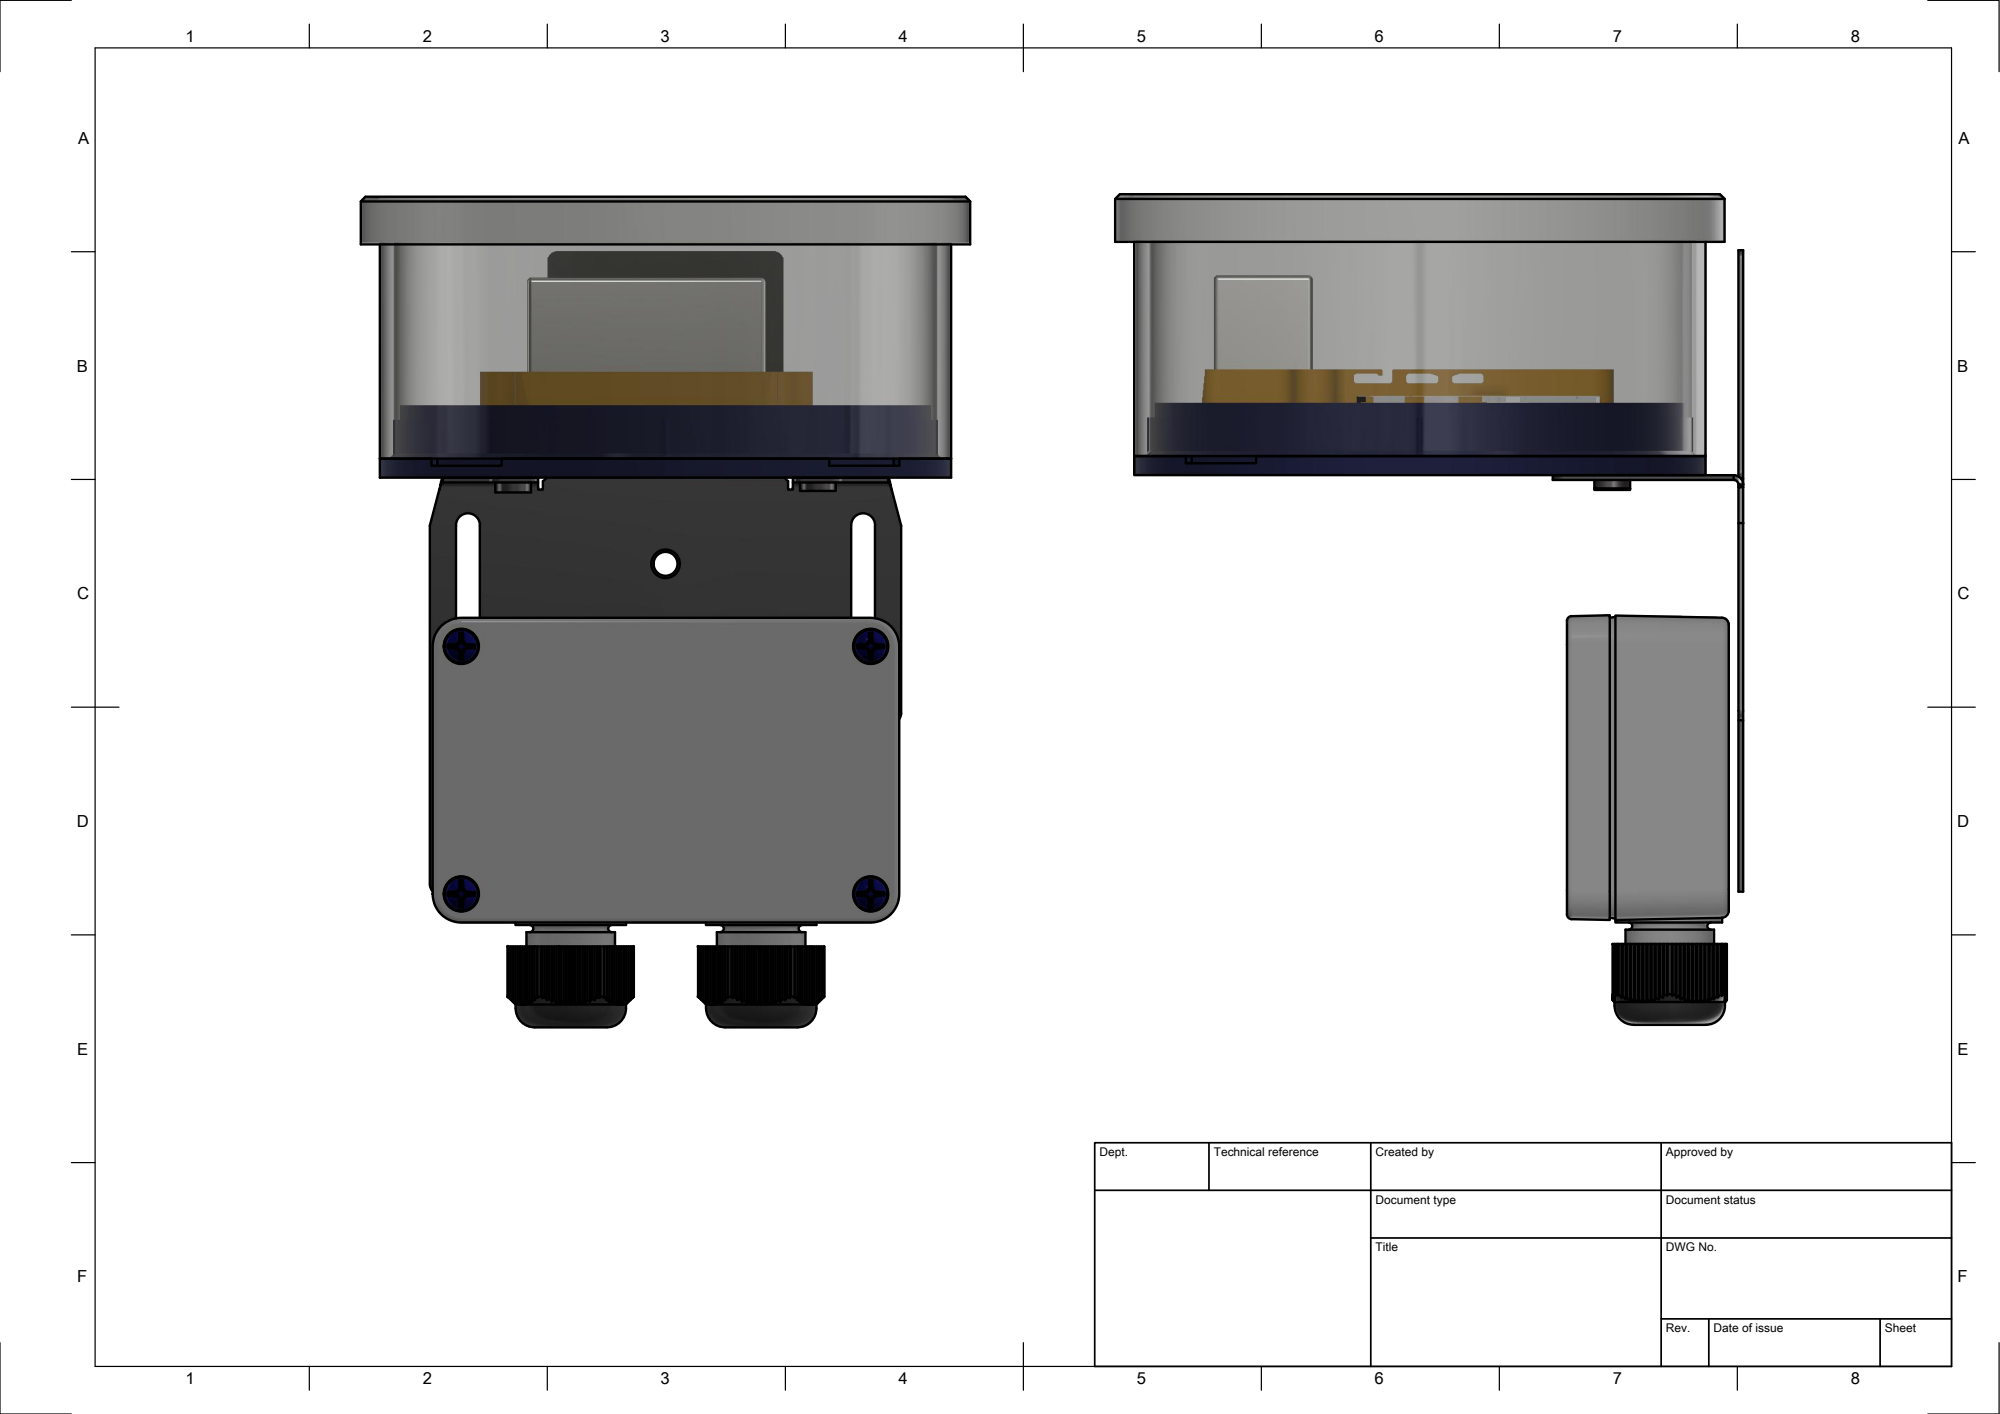
[picture p231: page 3]

Dept. | Technical reference | Created by | Approved by

Document type | Document status

Title | DWG No.
