fablabbcn/smartcitizen-enclosures/docs/Air/SCK2.1/SCK2.1_PMS5003/CNC HDPE circle/drawing_hdpe_base.pdf

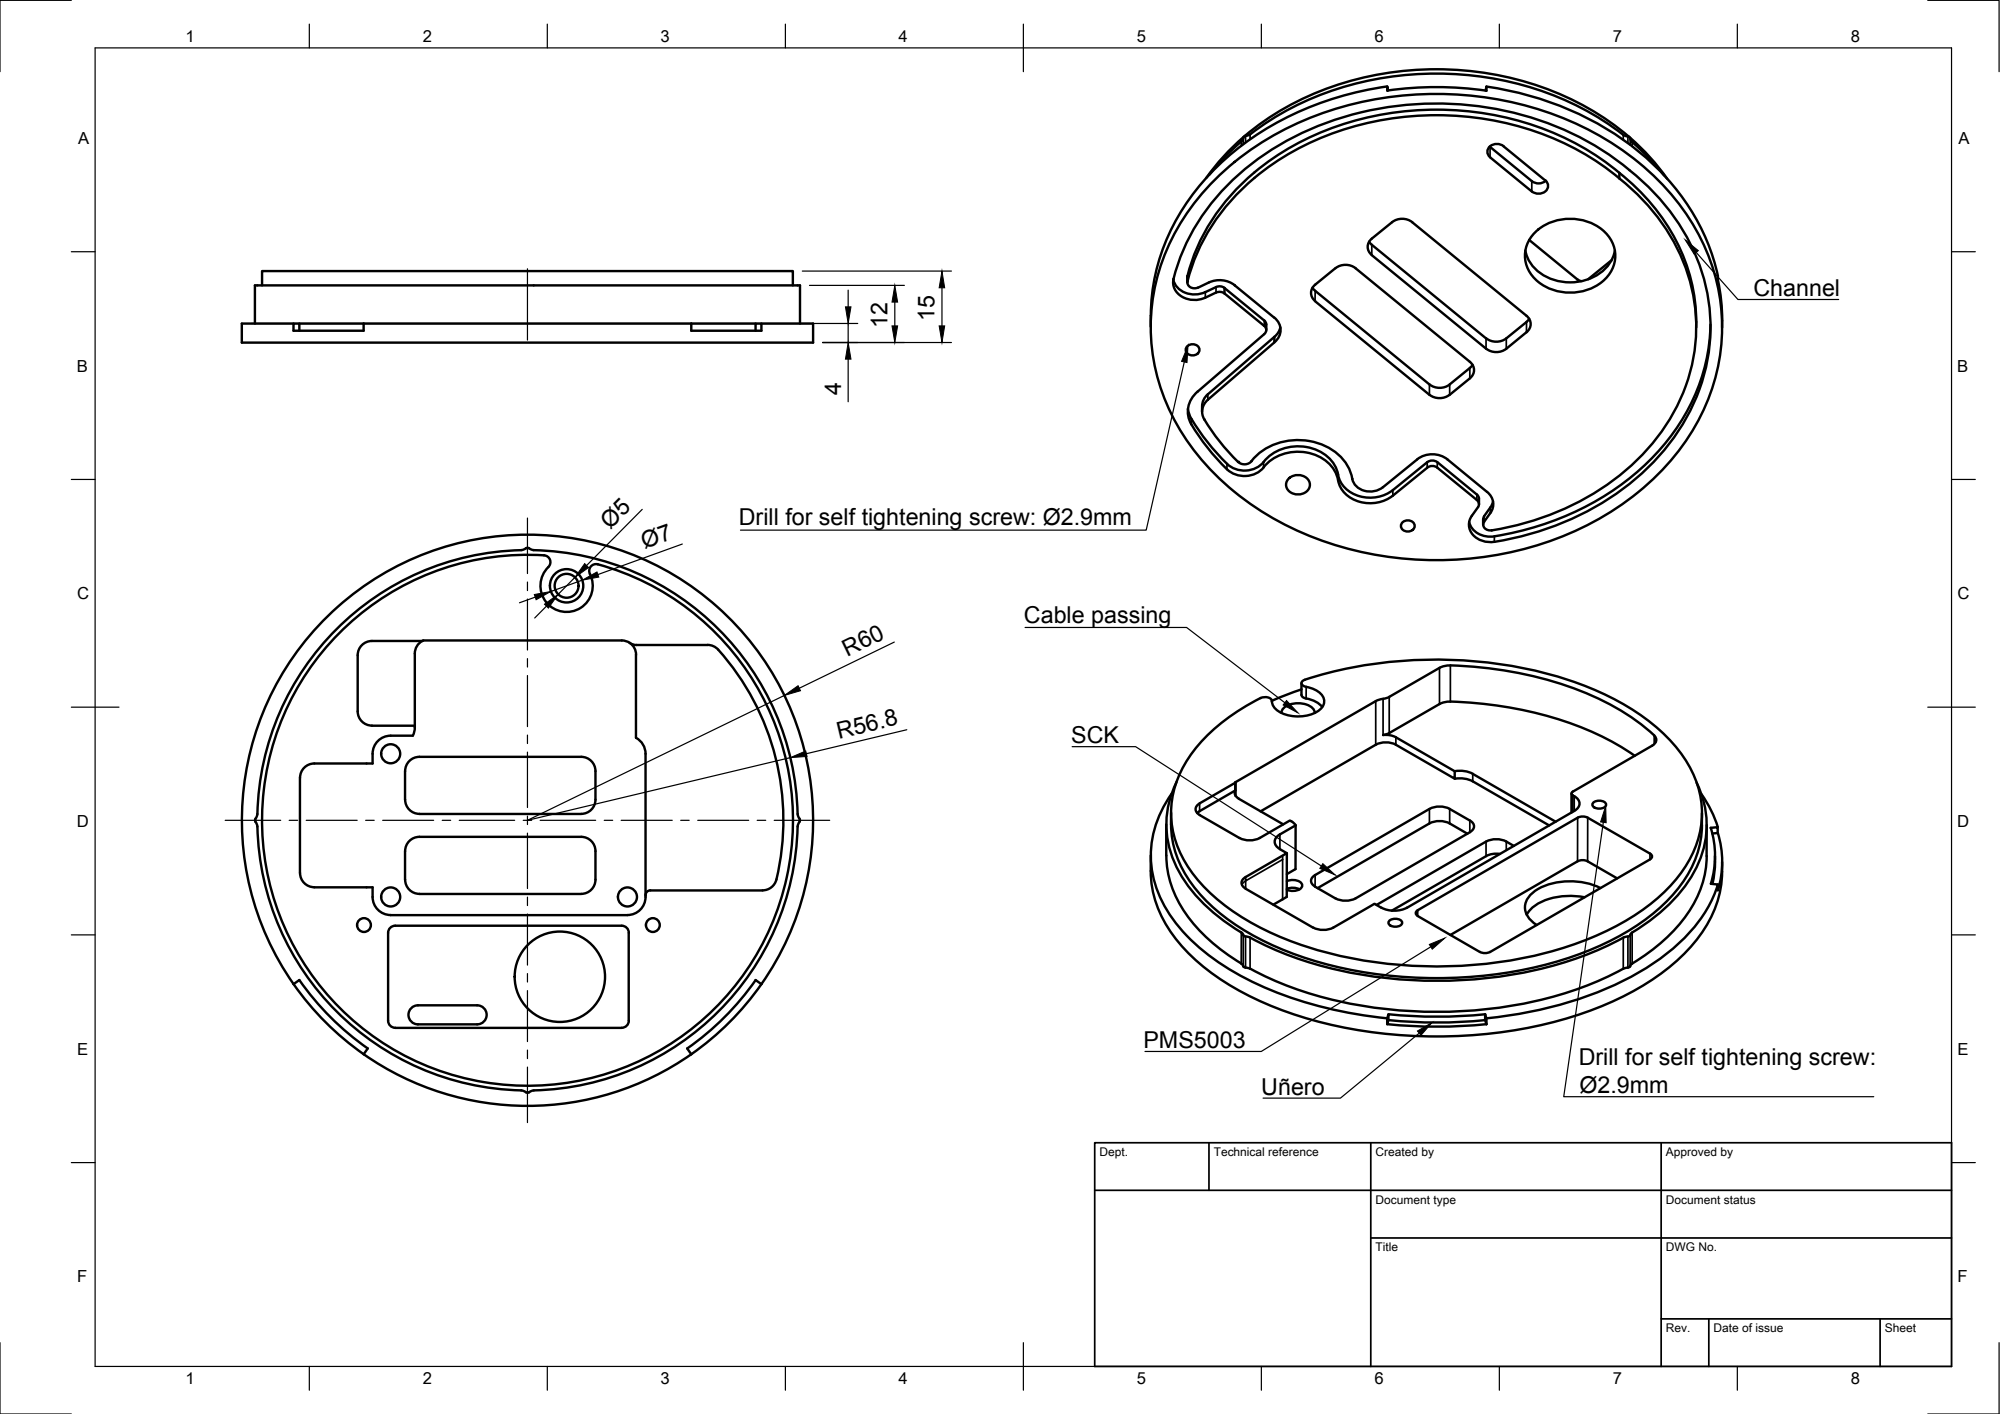
[picture p232: page 1]
Cable passing

Drill for self tightening screw: Ø2.9mm

Drill for self tightening screw:

Dept. | Technical reference | Created by | Approved by

Document type | Document status

Title | DWG No.

Rev. | Date of issue | Sheet
