fablabbcn/smartcitizen-enclosures/docs/Air/SCK2.1/SCK2.1_PMS5003/CNC HDPE circle/drawing_metal_sheet.pdf

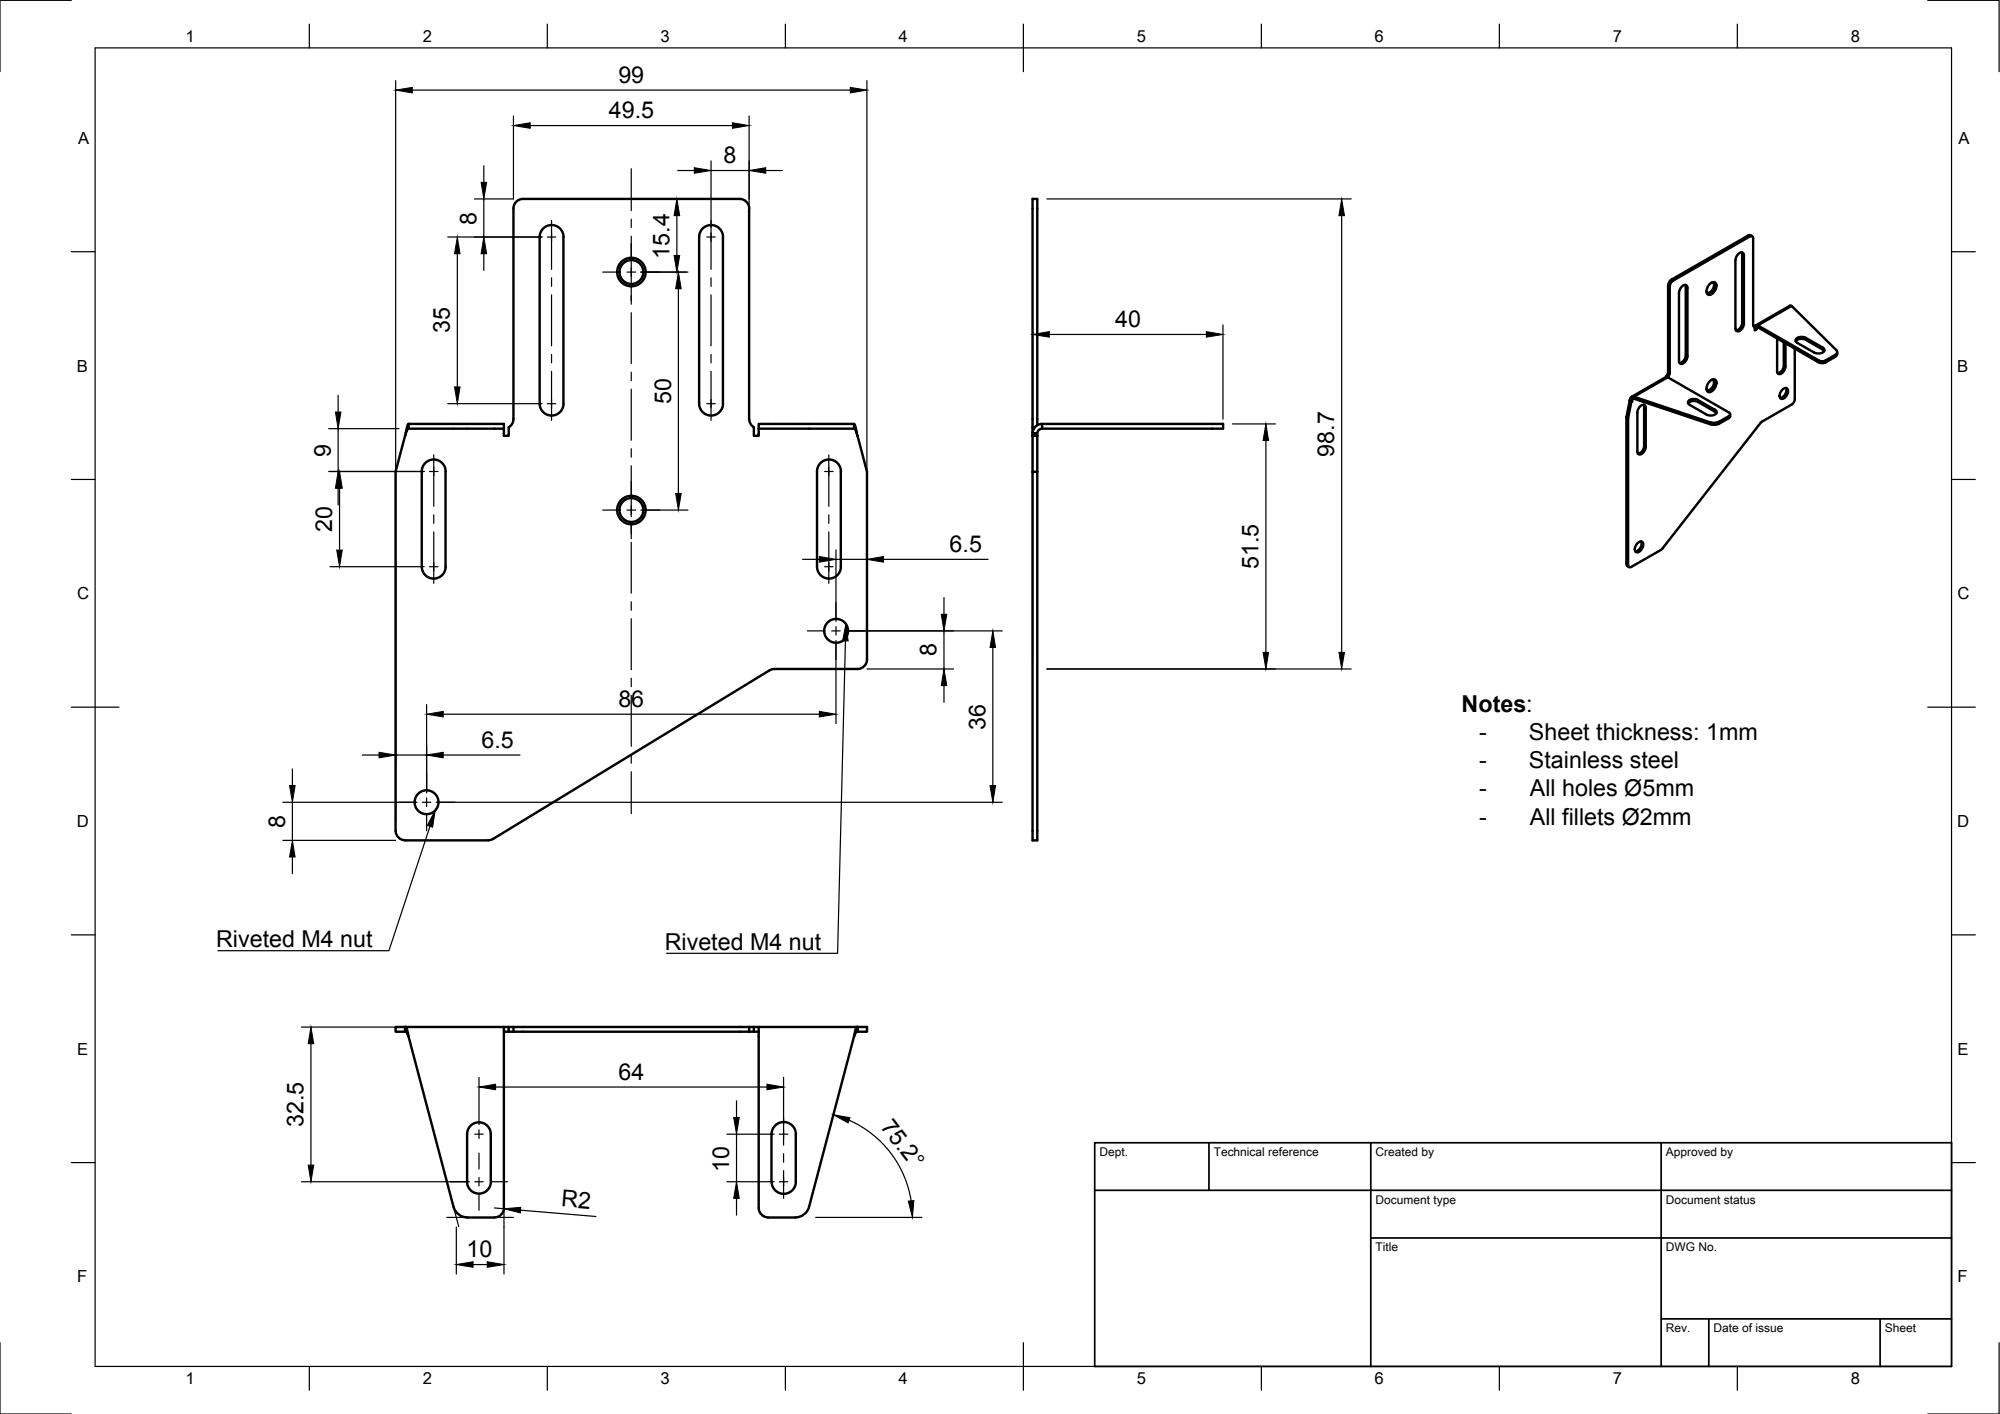
[picture p233: page 1]
Riveted M4 nut; Notes: -; Sheet thickness: 1mm; Stainless steel -; All holes Ø5mm; - All fillets Ø2mm 15.4 20

Dept. | Technical reference | Created by | Approved by

Document type | Document status

Title | DWG No.

Rev. | Date of issue | Sheet

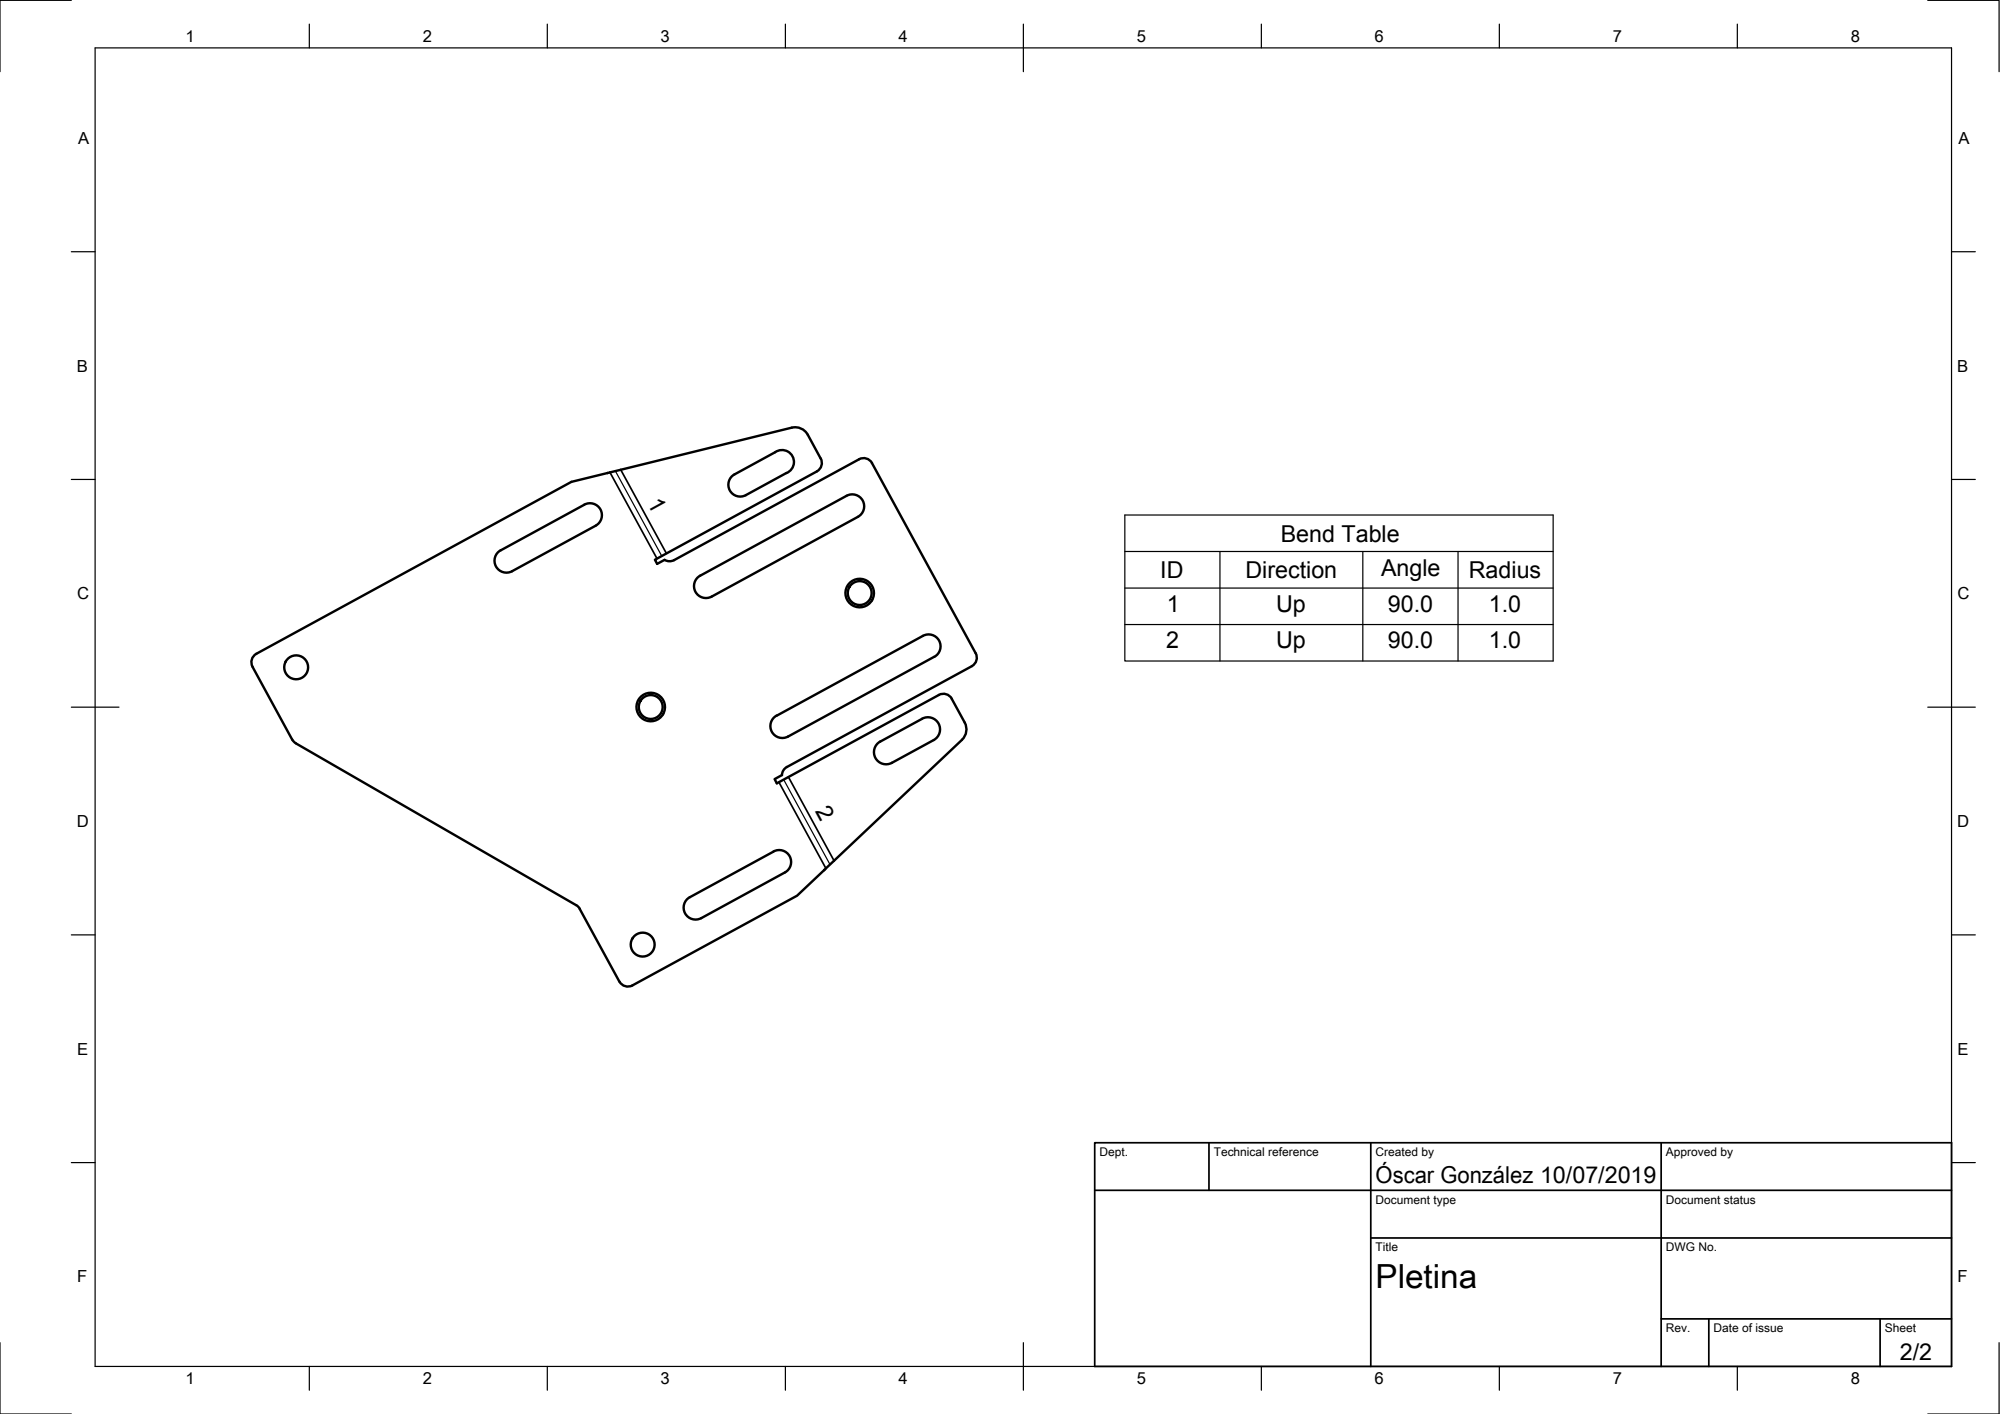
[picture p234: page 2]
Bend Table

ID | Direction | Angle | Radius
1 | Up | 90.0 | 1.0
2 | Up | 90.0 | 1.0

Dept. | Technical reference | Created by Óscar González 10/07/2019 | Approved by

Document type | Document status

Title Pletina | DWG No.

Rev. | Date of issue | Sheet 2/2
