fablabbcn/smartcitizen-enclosures/docs/Air/legacy/SmartCitizen Case V1.5.1/Smarcitizen Case MakingSense .pdf

56

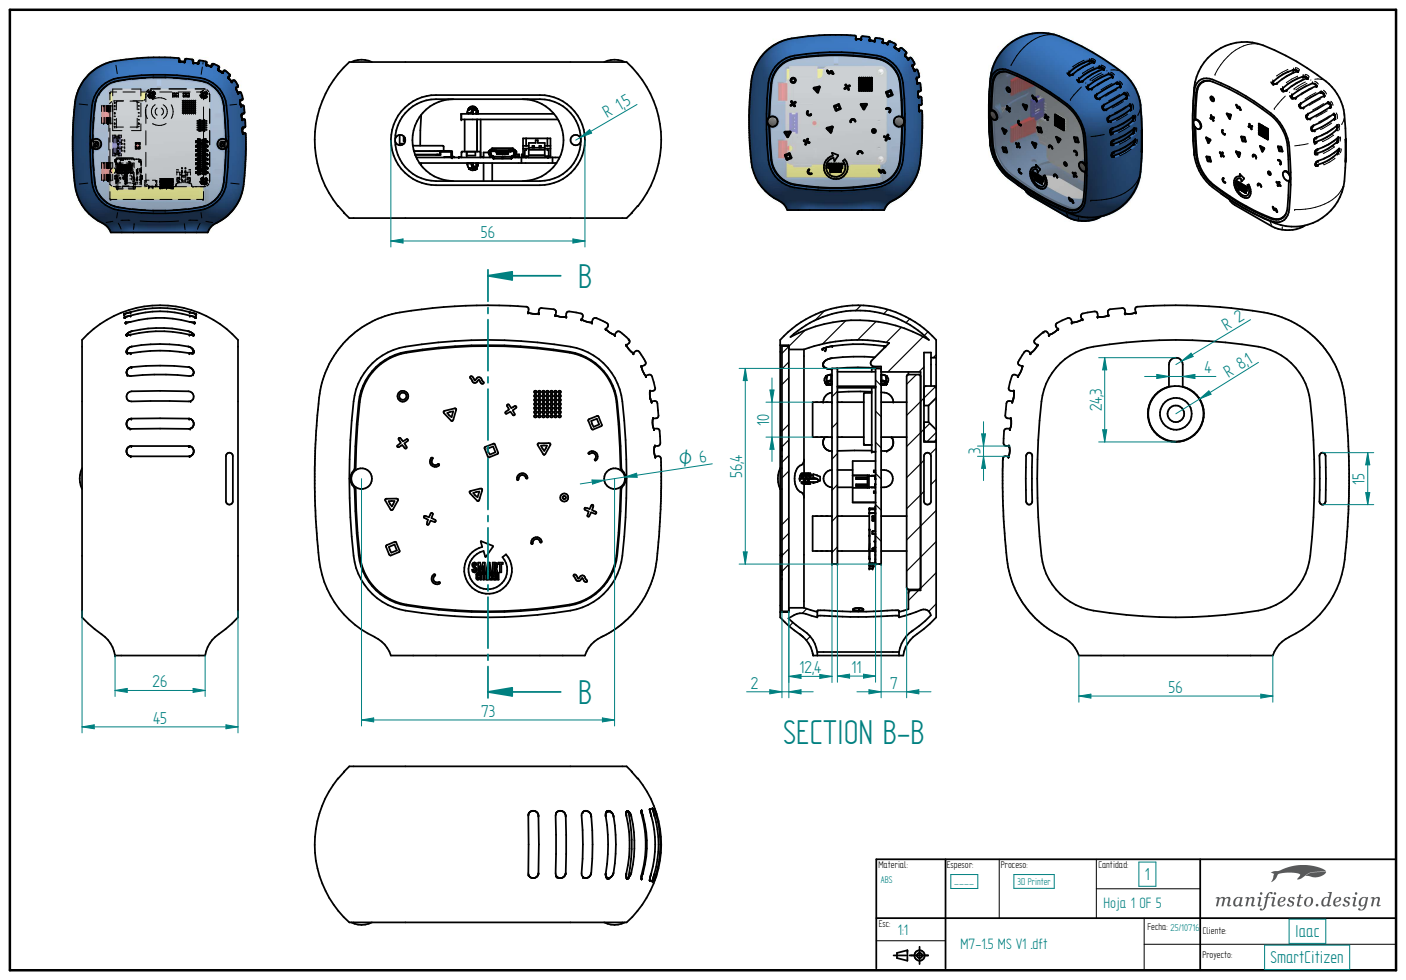
[picture p236: page 1]
Material:; Espesor:; Proceso:; Cantidad:; Hoja 1 OF 5; ABS; SmartCitizen ____; 3D Printer; SECTION B-B

Esc: | M7-1.5 MS V1 .dft | Fecha: 25/10716 1:1 | Cliente: | Iaac

Proyecto:
