fablabbcn/smartcitizen-enclosures/docs/Air/legacy/SmartCitizen Case Stevenson V0.0.1/M7-1.5-V10-2.pdf

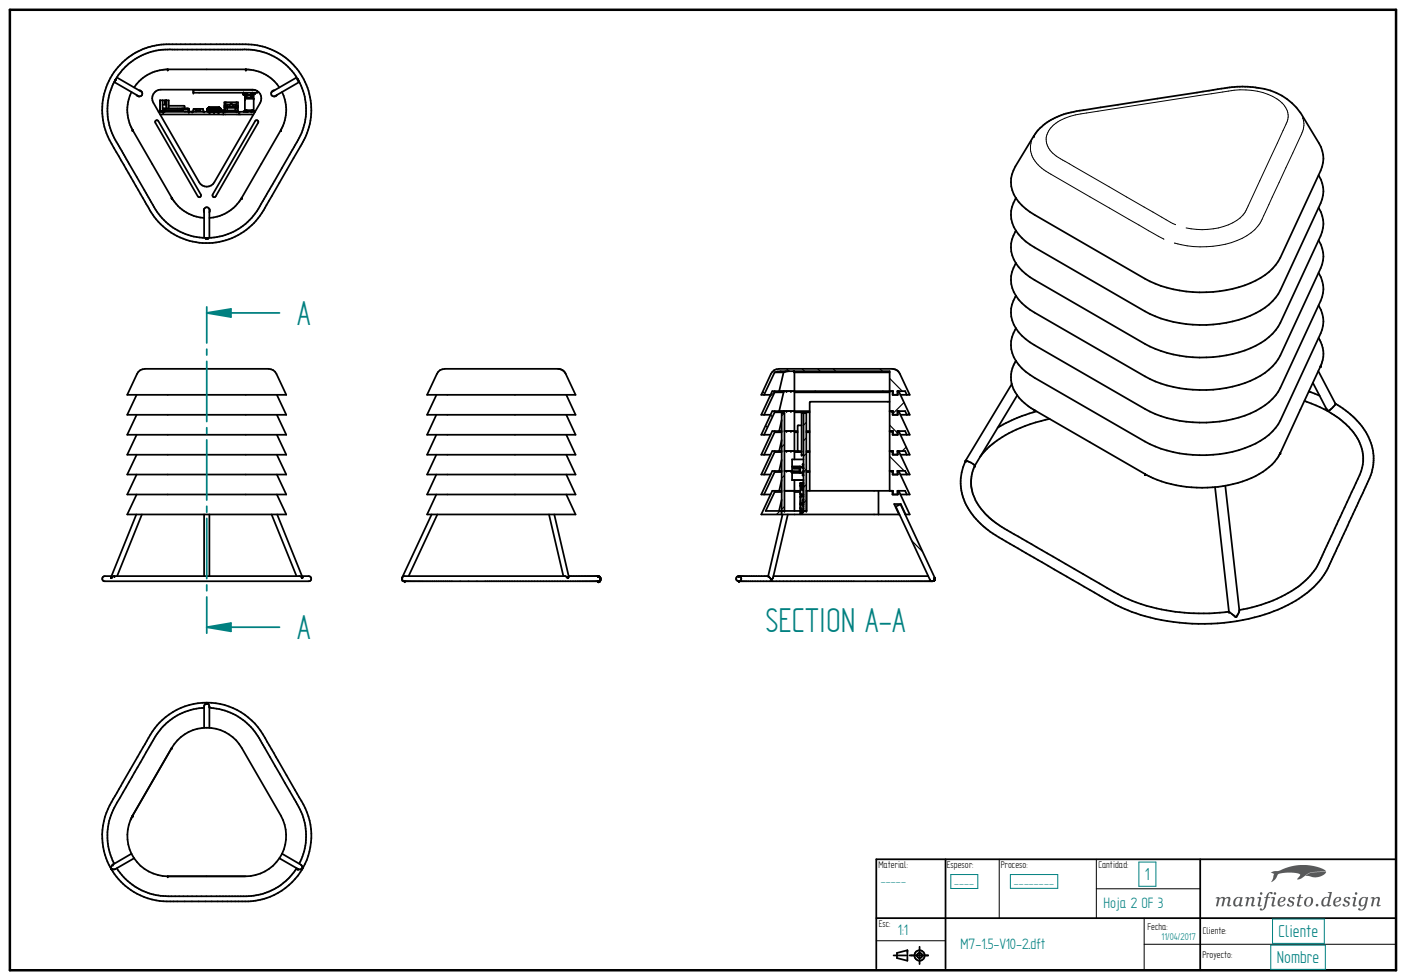
[picture p237: page 1]
Material:; Espesor:; Proceso:; Cantidad:; Cliente:; Proyecto:; Esc:; M7-1.5-V10-2.dft; Hoja 2 OF 3 _____; Fecha: ____; Cliente; Nombre; SECTION A-A
