fablabbcn/smartcitizen-enclosures/docs/Air/legacy/SmartCitizen Case V1.5.1/Smarcitizen Exploded View.pdf

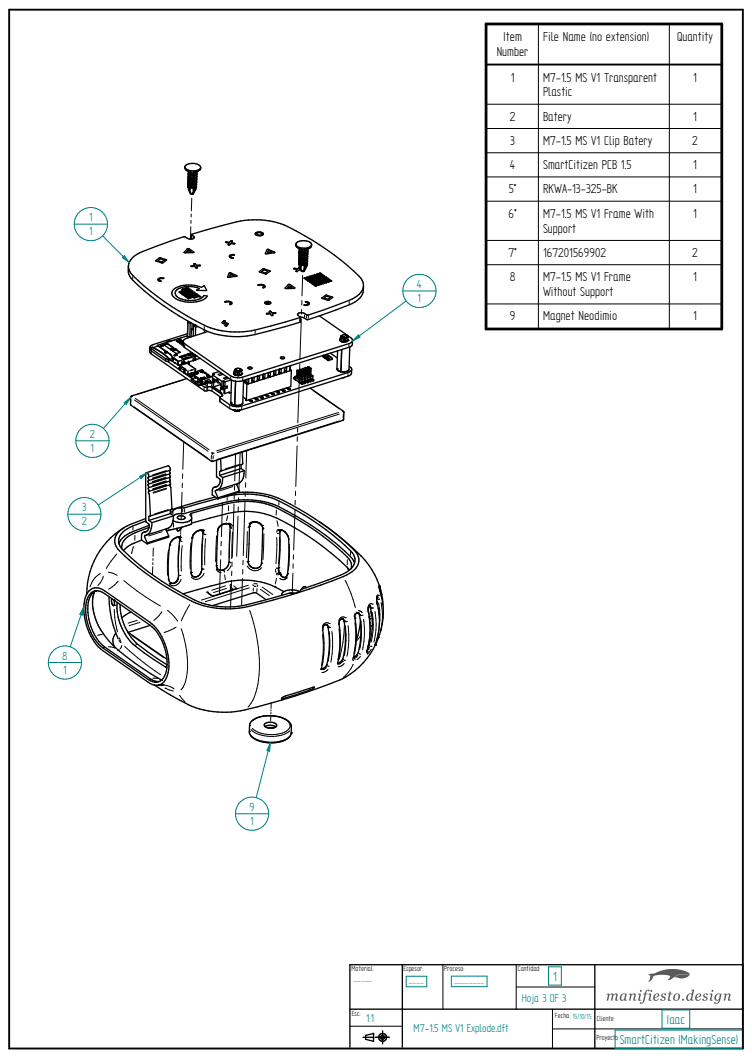
[picture p238: page 1]
Material:; Espesor:; Proceso:; Cantidad:; Cliente:; Proyecto:; Esc:; Hoja 3 OF 3; Fecha:; Iaac; SmartCitizen (MakingSense); Item Number; File Name (no extension); Quantity; M7-1.5 MS V1 Transparent; Plastic; Batery; M7-1.5 MS V1 Clip Batery; SmartCitizen PCB 1.5; RKWA-13-325-BK; M7-1.5 MS V1 Frame With; Support; M7-1.5 MS V1 Frame; Without Support; Magnet Neodimio

M7-1.5 MS V1 Explode.dft
