fablabbcn/smartcitizen-enclosures/docs/Air/legacy/SmartCitizen Case Stevenson V0.0.1/M7-1.5-V10-2 explotado.pdf

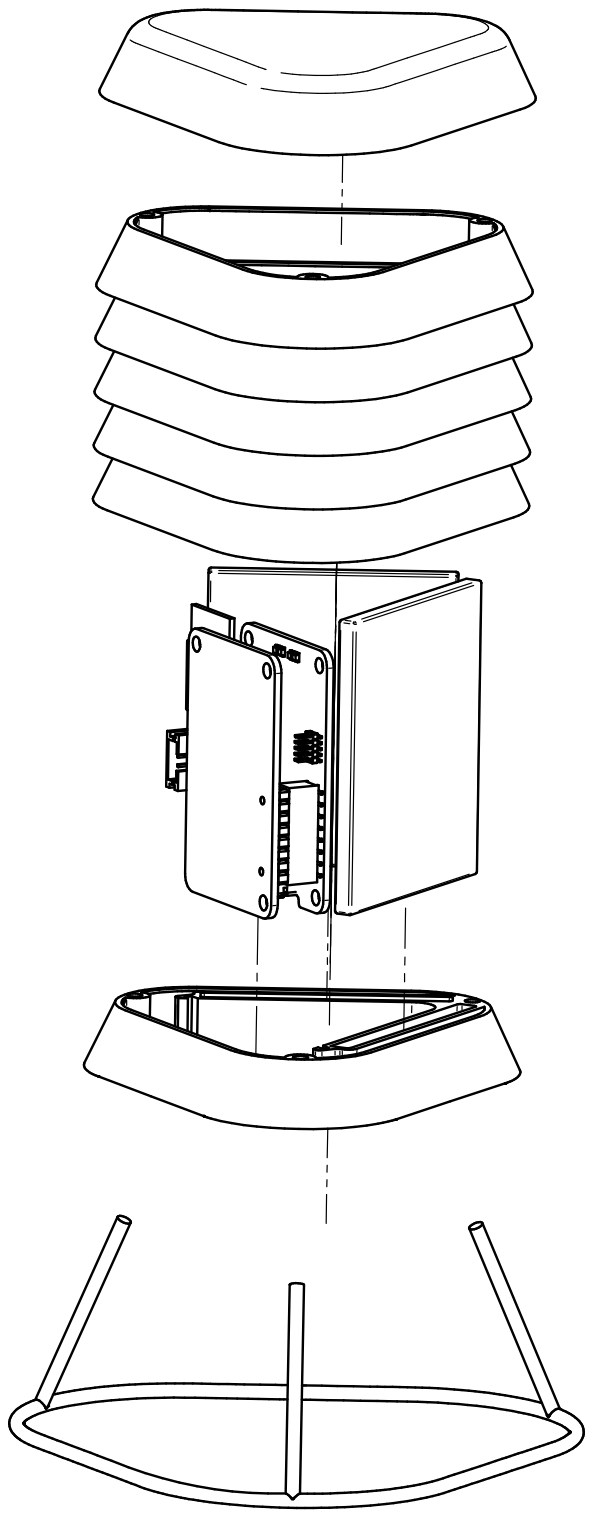
[picture p239: page 1]
