fablabbcn/smartcitizen-enclosures/docs/Air/SCK2.1/SCK2.1_PMS5003/SCK_3Dprint_Assembly_GER_EN_USTTG_IIGS_2023/2022-05-16 16.21.05.jpg

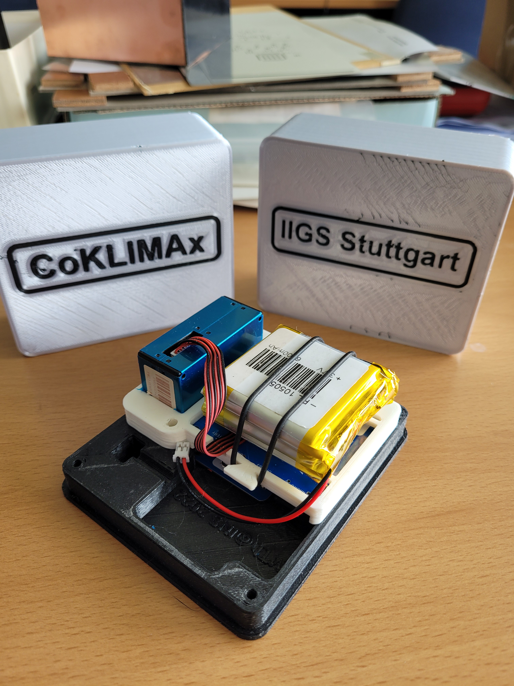
docs/Air/SCK2.1/SCK2.1_PMS5003/SCK_3Dprint_Assembly_GER_EN_USTTG_IIGS_2023/2022-05-16 16.21.05.jpg
